inajob/rakuchord/docs/imgs/cheatsheet.jpg

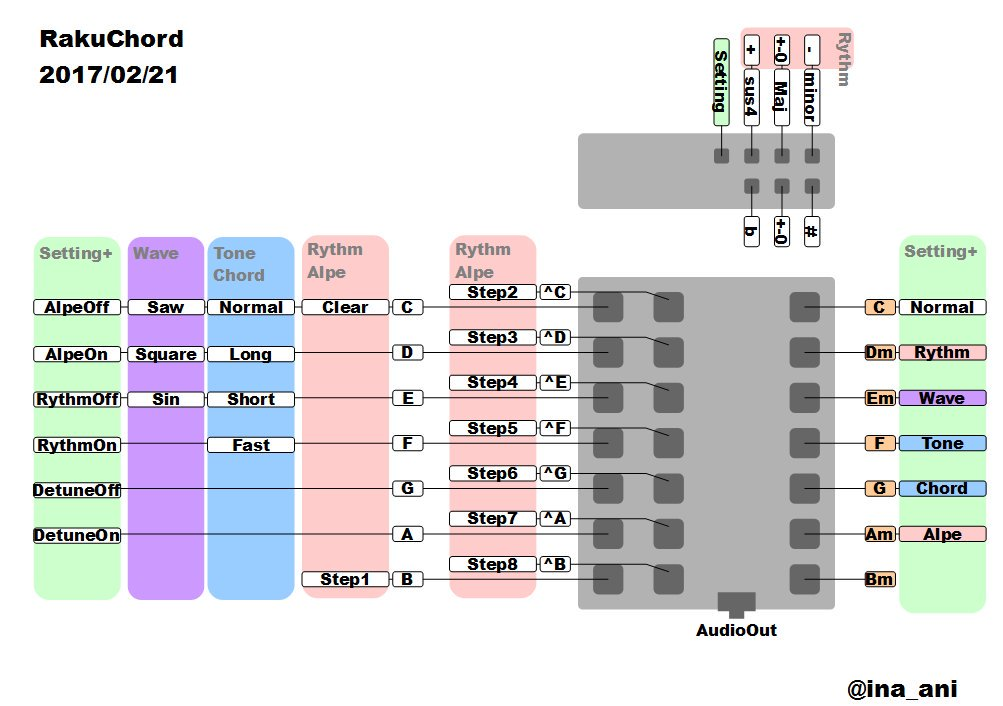
docs/imgs/cheatsheet.jpg
