inajob/rakuchord/docs/imgs/display-v1-3.png

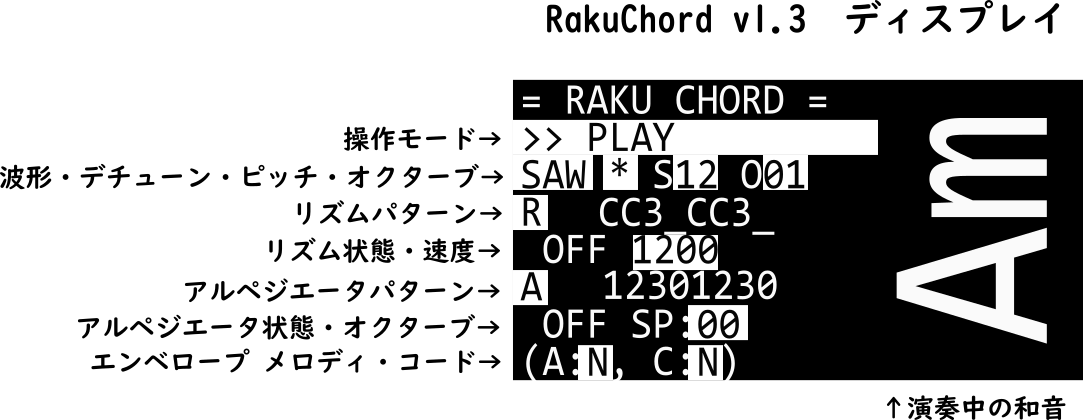
docs/imgs/display-v1-3.png
