inajob/rakuchord/docs/imgs/first-rakuchord.png

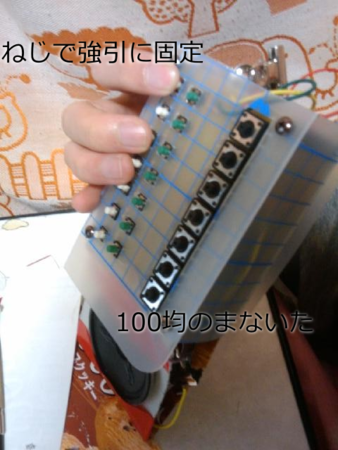
docs/imgs/first-rakuchord.png
