inajob/rakuchord/docs/imgs/latest-rakuchord.jpg

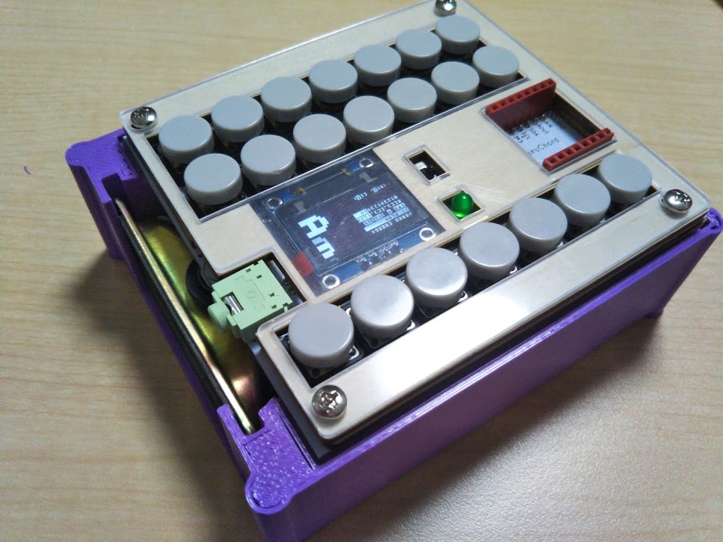
docs/imgs/latest-rakuchord.jpg
