inajob/rakuchord/docs/imgs/many-rakuchord.jpg

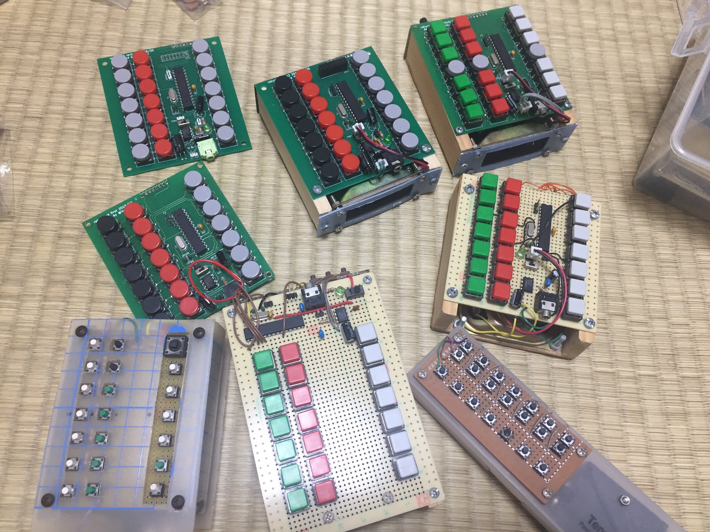
docs/imgs/many-rakuchord.jpg
