inajob/rakuchord/docs/imgs/rakuchord2018.jpg

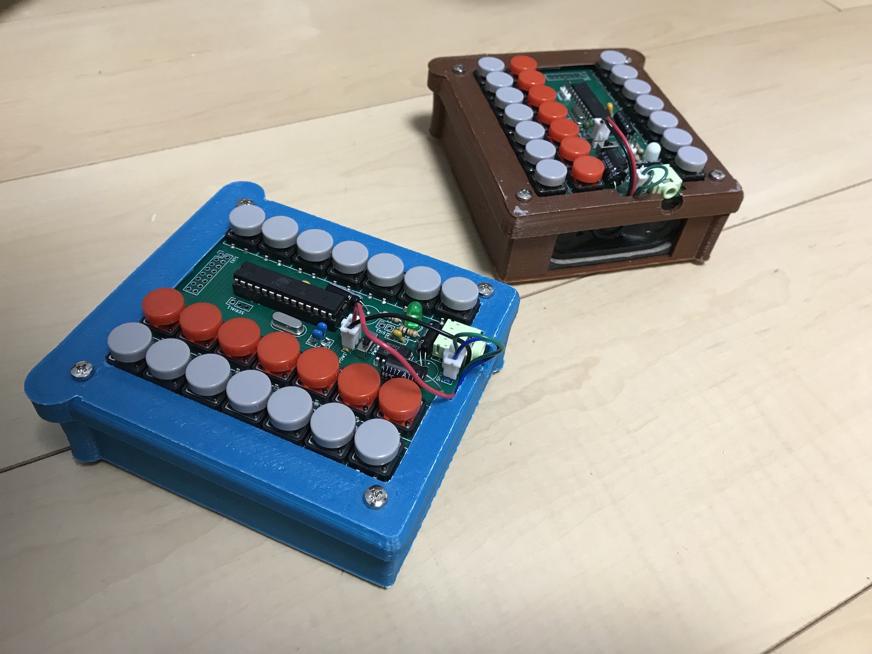
docs/imgs/rakuchord2018.jpg
