inajob/rakuchord/docs/imgs/rakuchord-long.jpg

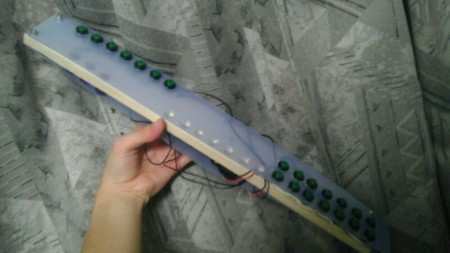
docs/imgs/rakuchord-long.jpg
