inajob/rakuchord/docs/imgs/rakuchord-mobile-3.png

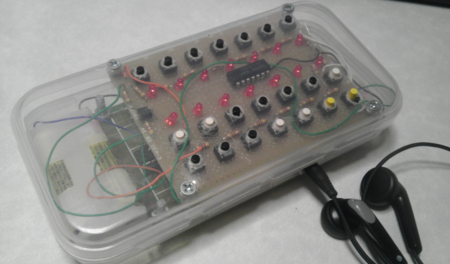
docs/imgs/rakuchord-mobile-3.png
