inajob/rakuchord/docs/imgs/rakuchord-p-v1-4.png

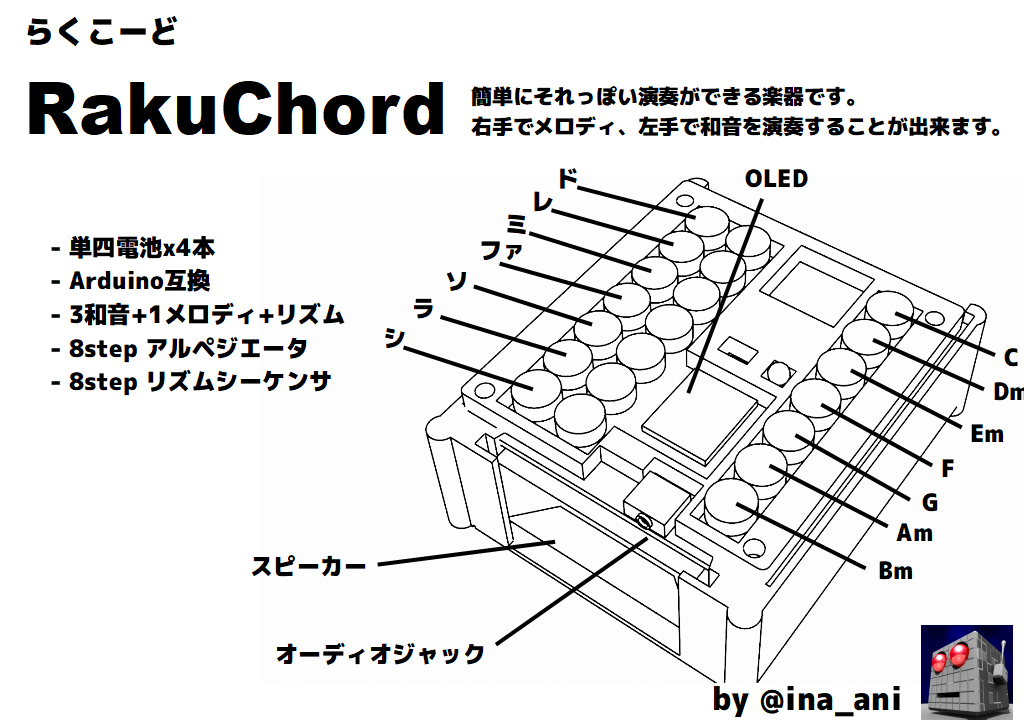
docs/imgs/rakuchord-p-v1-4.png
