inajob/rakuchord/docs/imgs/rakuchord-p.jpg

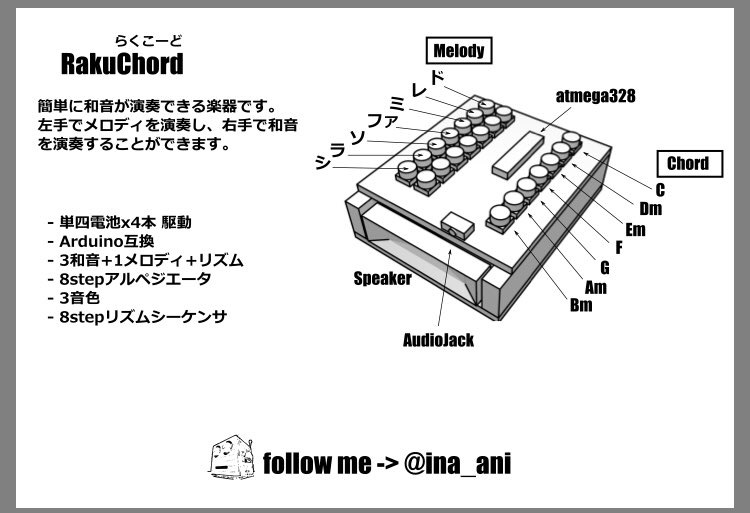
docs/imgs/rakuchord-p.jpg
