inajob/rakuchord/docs/imgs/rakuchord-v1-3-2.jpg

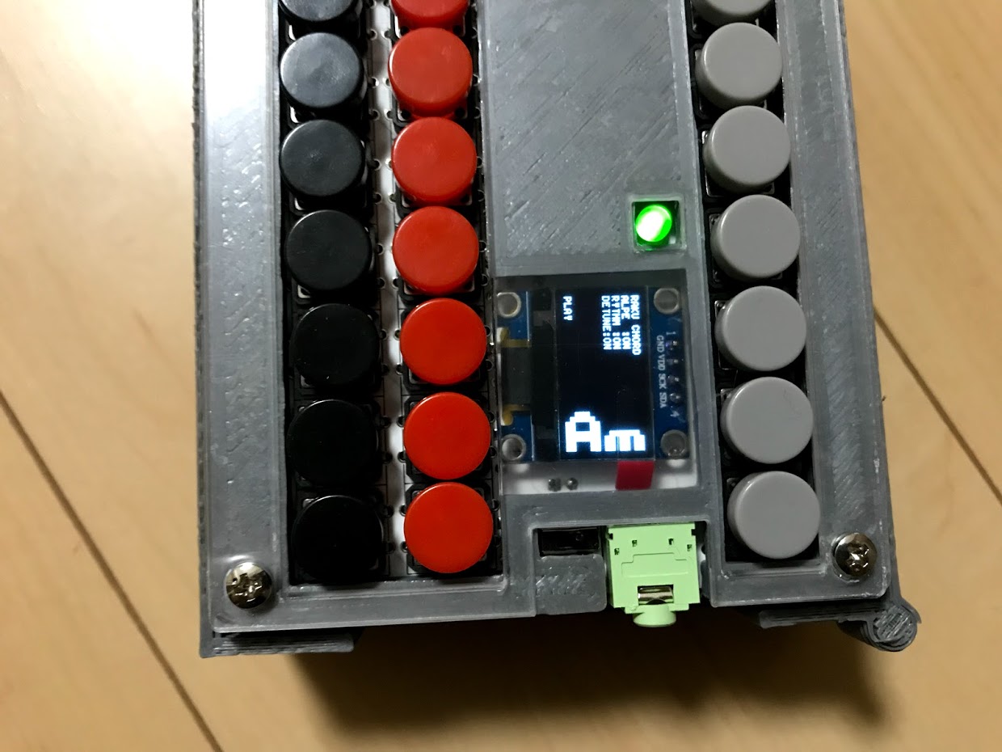
docs/imgs/rakuchord-v1-3-2.jpg
