inajob/rakuchord/docs/imgs/rakuchord-v1-3.jpg

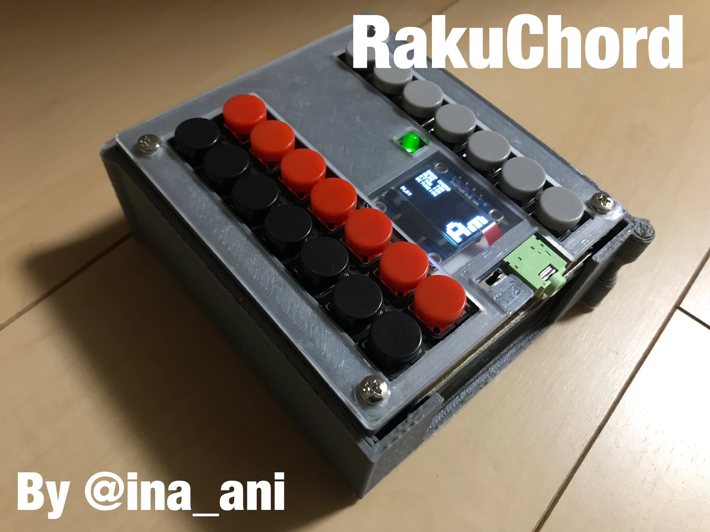
docs/imgs/rakuchord-v1-3.jpg
