inajob/rakuchord/docs/imgs/subkey.jpg

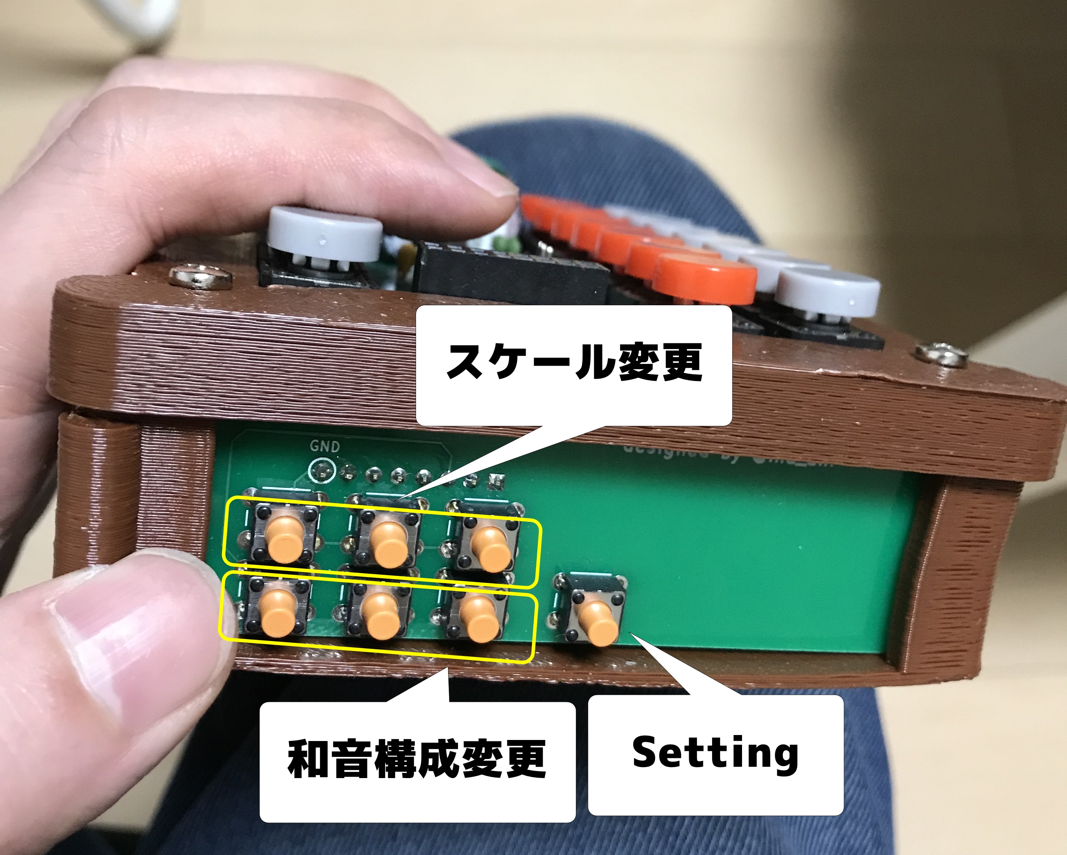
docs/imgs/subkey.jpg
