inajob/rakuchord/docs/imgs/instruction-out-1-4/order.png

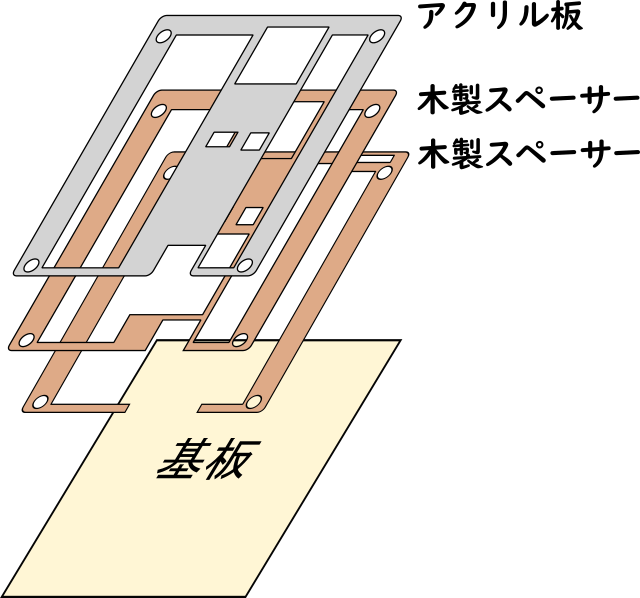
docs/imgs/instruction-out-1-4/order.png
