inajob/rakuchord/docs/imgs/instruction-out/000-first-parts.jpg

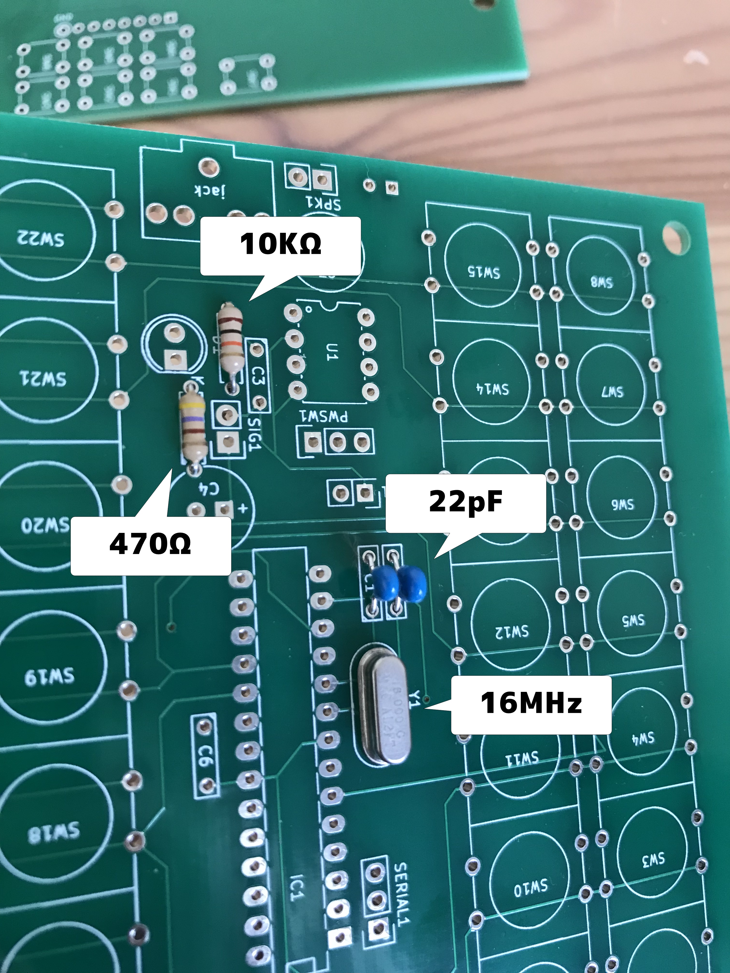
docs/imgs/instruction-out/000-first-parts.jpg
