inajob/rakuchord/docs/imgs/instruction-out/001-first-parts-back.jpg

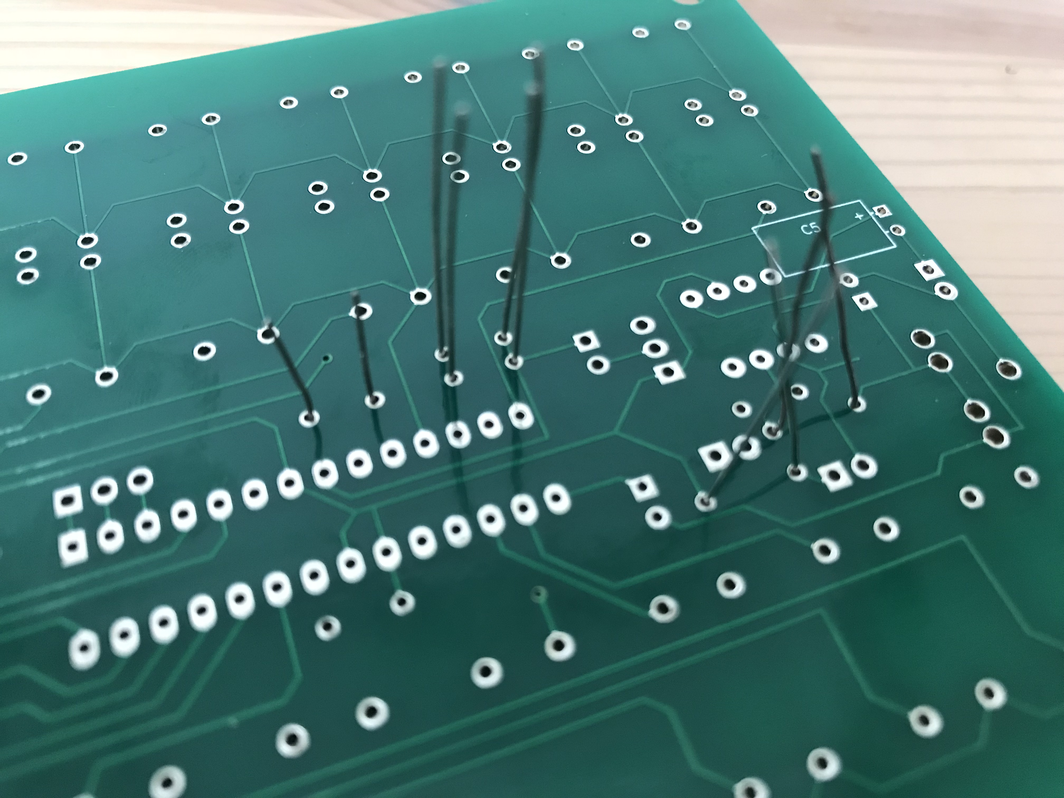
docs/imgs/instruction-out/001-first-parts-back.jpg
