inajob/rakuchord/docs/imgs/instruction-out/002-first-parts-pliers.jpg

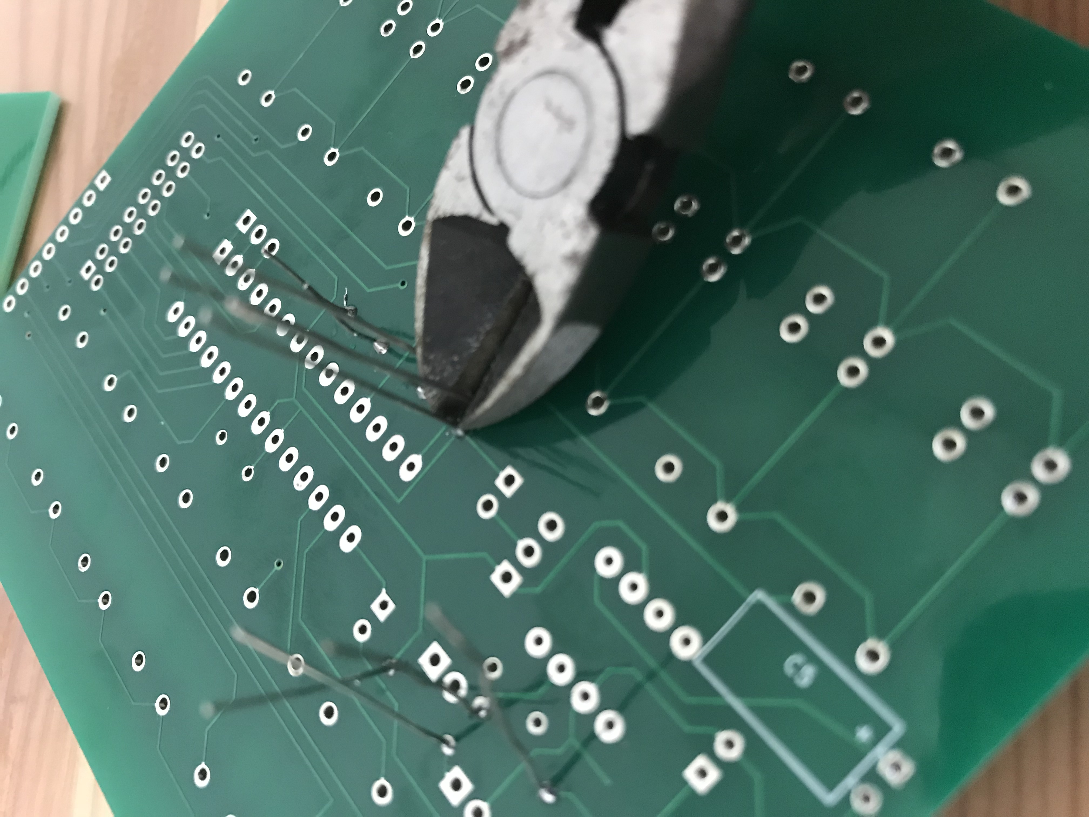
docs/imgs/instruction-out/002-first-parts-pliers.jpg
