inajob/rakuchord/docs/imgs/instruction-out/003-first-parts-complete.jpg

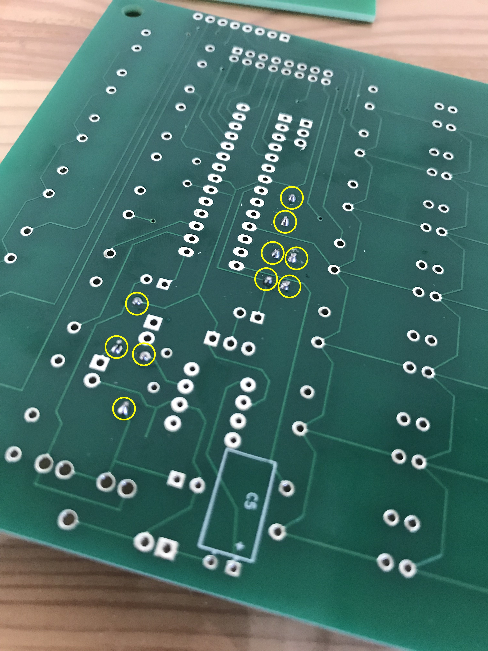
docs/imgs/instruction-out/003-first-parts-complete.jpg
