inajob/rakuchord/docs/imgs/instruction-out/004-second-parts-dub.jpg

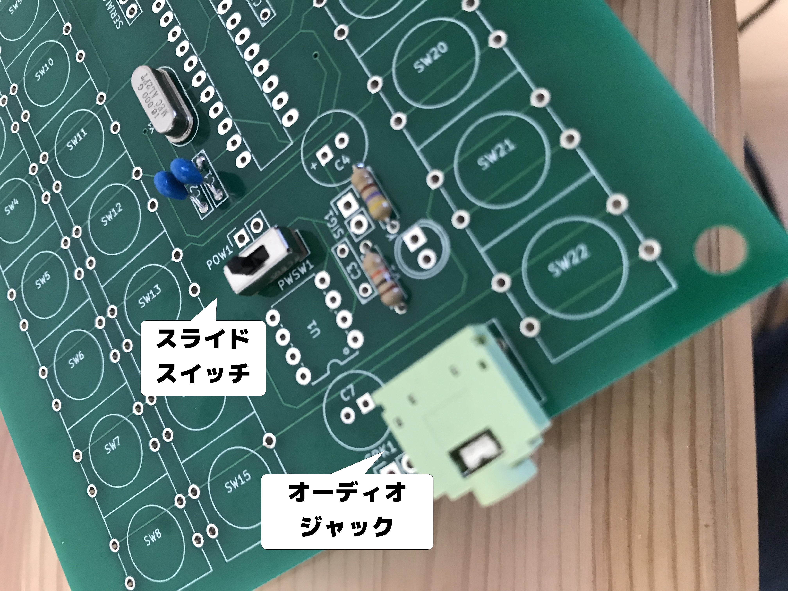
docs/imgs/instruction-out/004-second-parts-dub.jpg
