inajob/rakuchord/docs/imgs/instruction-out/005-second-parts.jpg

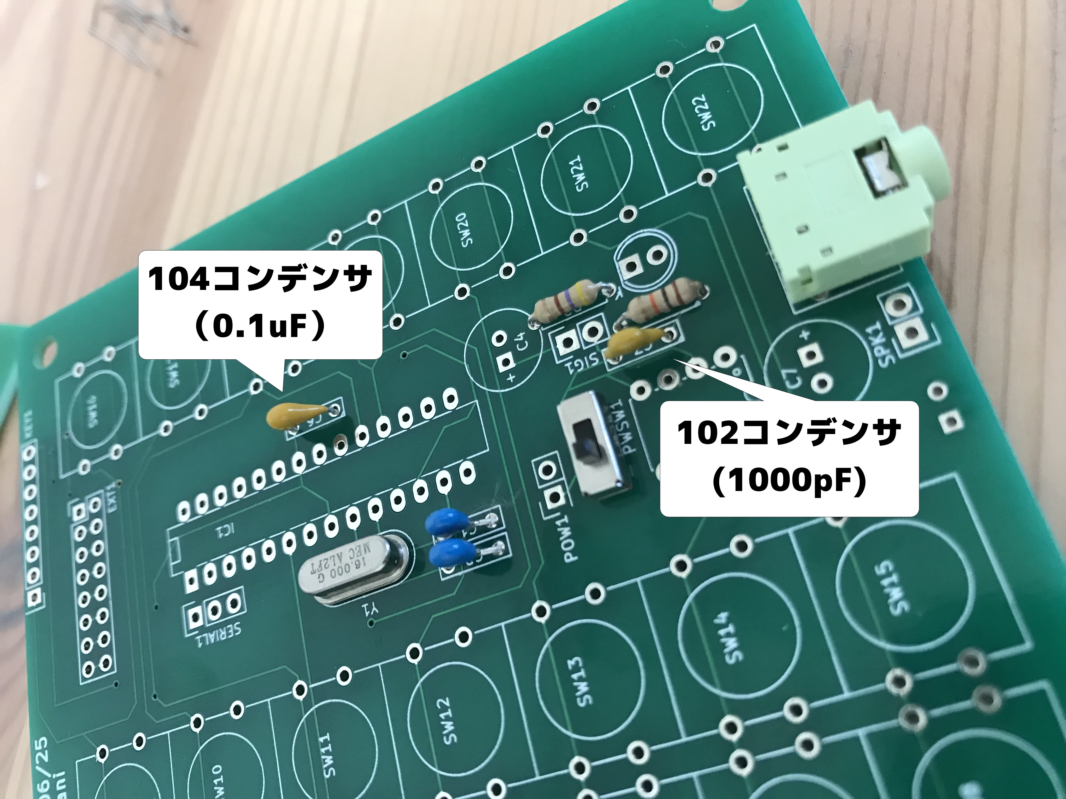
docs/imgs/instruction-out/005-second-parts.jpg
