inajob/rakuchord/docs/imgs/instruction-out/006-second-parts-tips.jpg

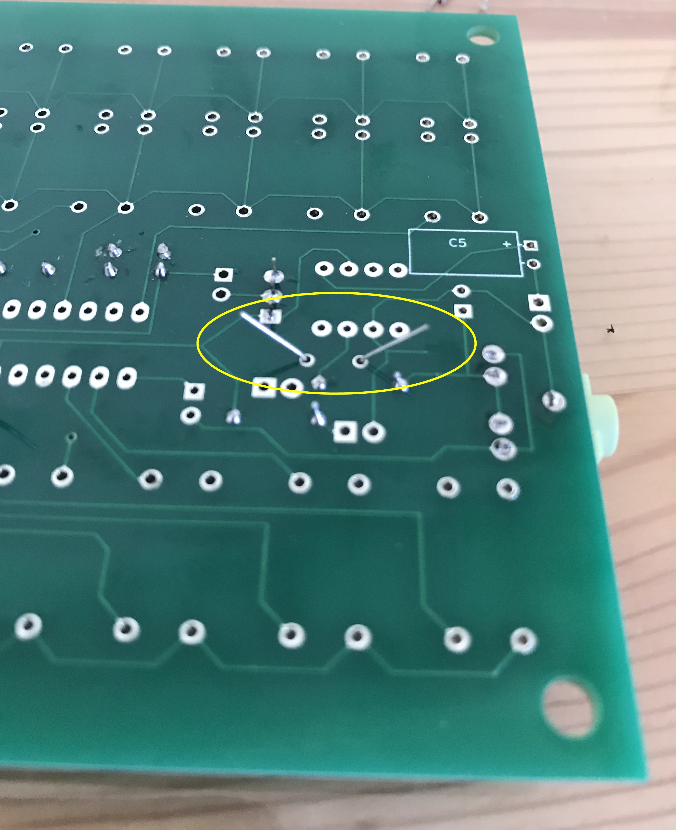
docs/imgs/instruction-out/006-second-parts-tips.jpg
