inajob/rakuchord/docs/imgs/instruction-out/007-third-parts-dub.jpg

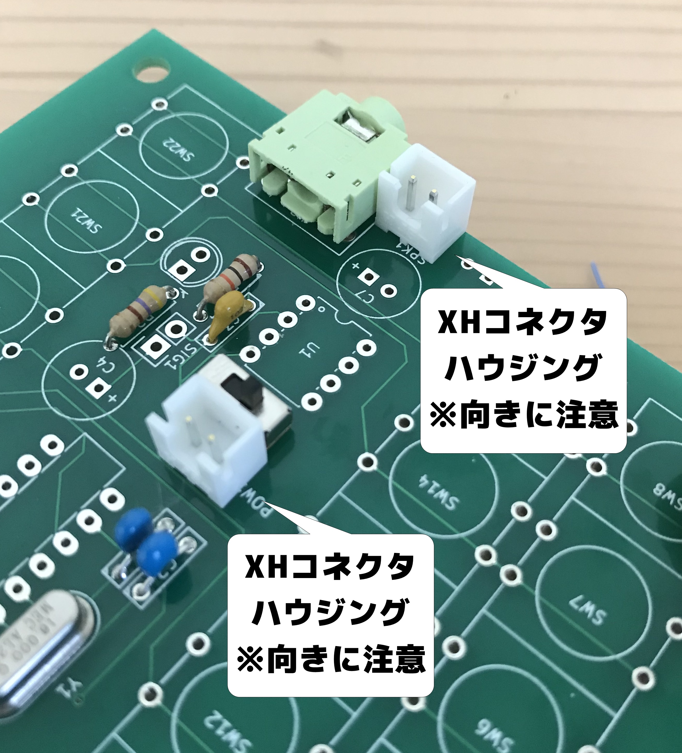
docs/imgs/instruction-out/007-third-parts-dub.jpg
