inajob/rakuchord/docs/imgs/instruction-out/008-third-parts.jpg

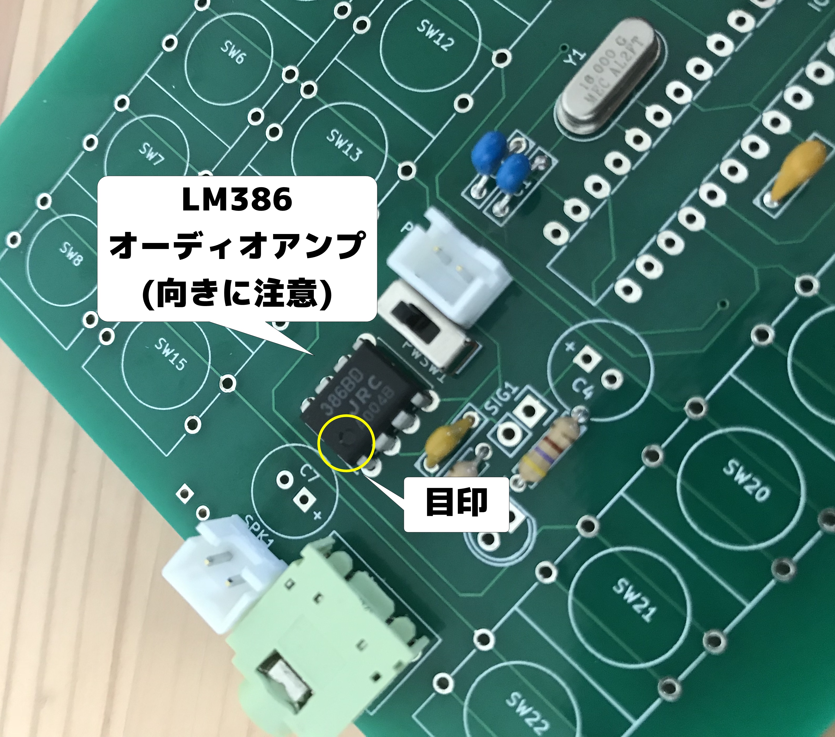
docs/imgs/instruction-out/008-third-parts.jpg
