inajob/rakuchord/docs/imgs/instruction-out/009-forth-parts.jpg

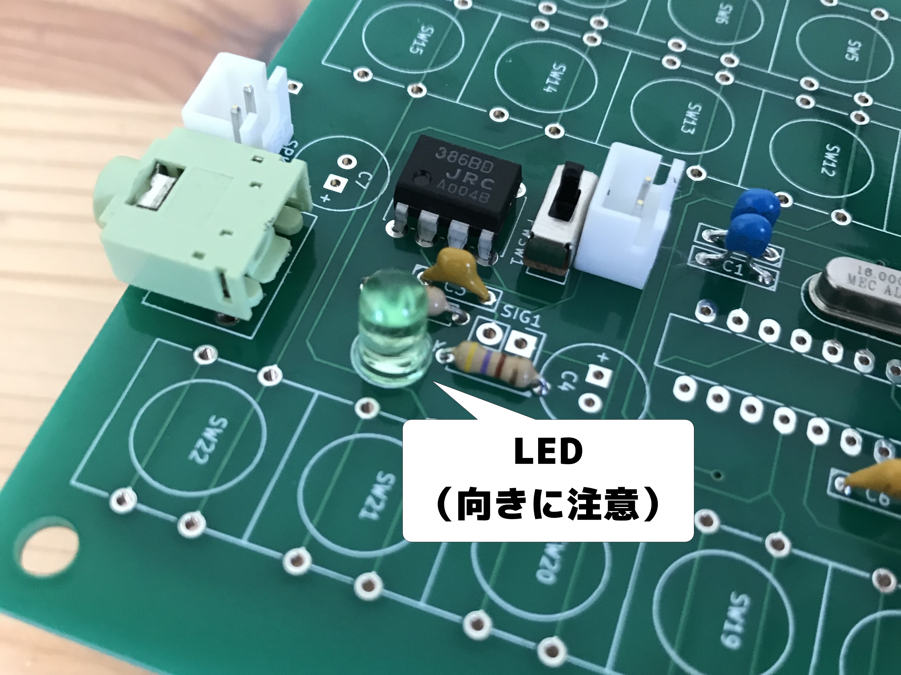
docs/imgs/instruction-out/009-forth-parts.jpg
