inajob/rakuchord/docs/imgs/instruction-out/010-forth-parts-tips.jpg

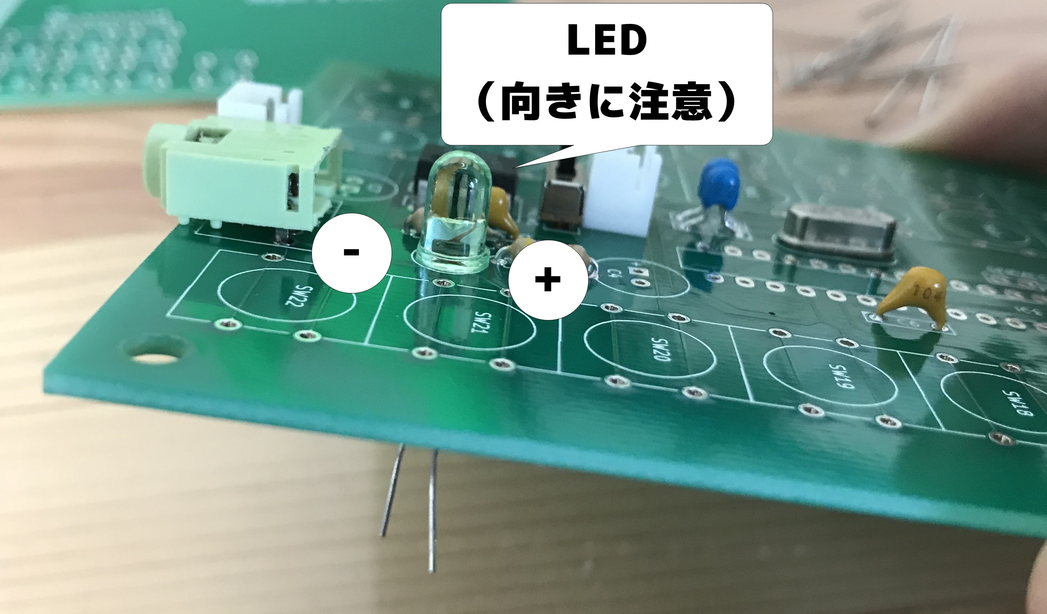
docs/imgs/instruction-out/010-forth-parts-tips.jpg
