inajob/rakuchord/docs/imgs/instruction-out/011-forth-parts-tips-dub.jpg

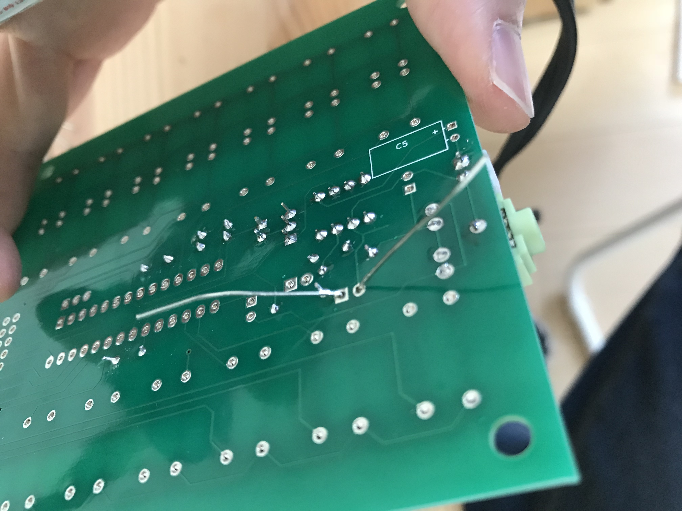
docs/imgs/instruction-out/011-forth-parts-tips-dub.jpg
