inajob/rakuchord/docs/imgs/instruction-out/012-fifth-parts.jpg

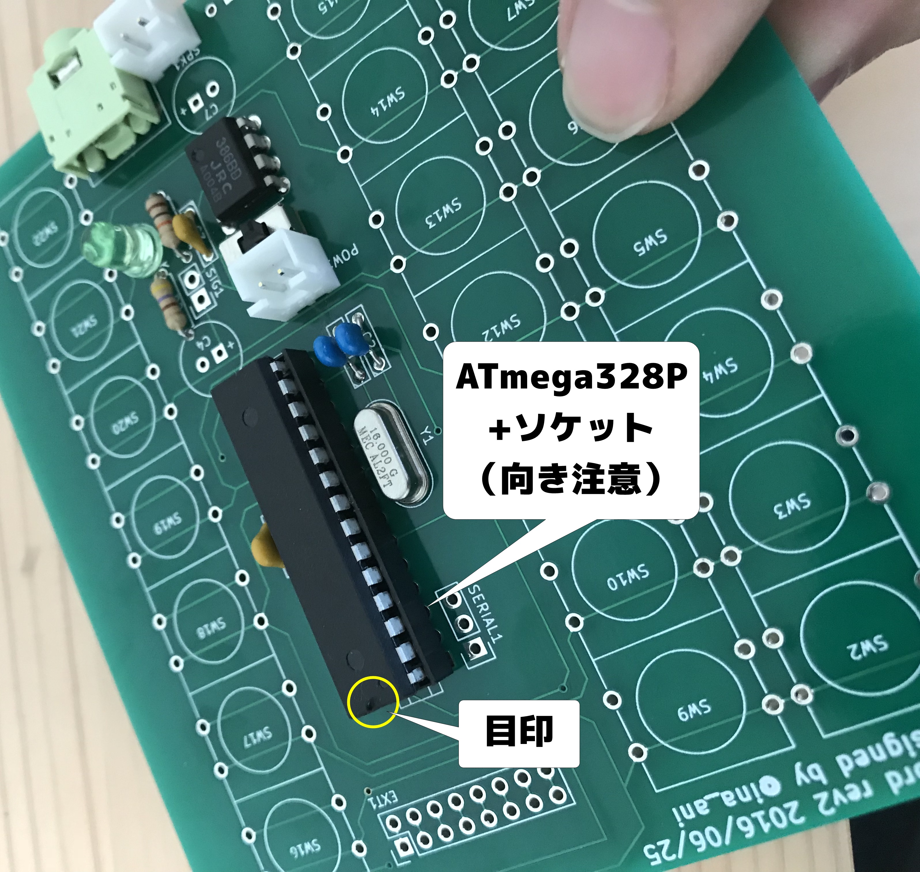
docs/imgs/instruction-out/012-fifth-parts.jpg
