inajob/rakuchord/docs/imgs/instruction-out/013-sixth-parts.jpg

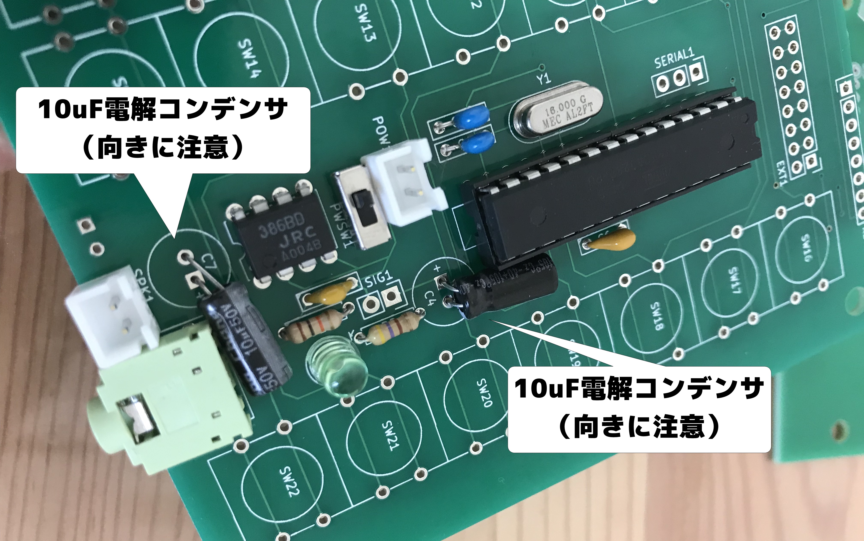
docs/imgs/instruction-out/013-sixth-parts.jpg
