inajob/rakuchord/docs/imgs/instruction-out/014-seventh-parts.jpg

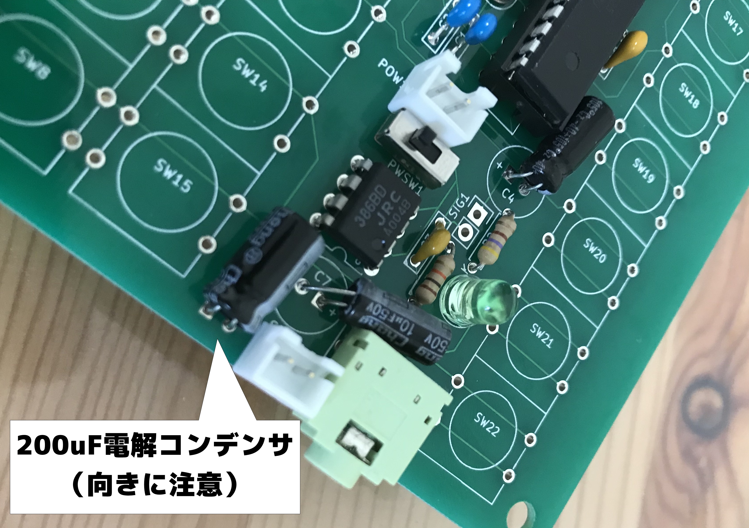
docs/imgs/instruction-out/014-seventh-parts.jpg
