inajob/rakuchord/docs/imgs/parts-1-4/acrylic-cover.jpg

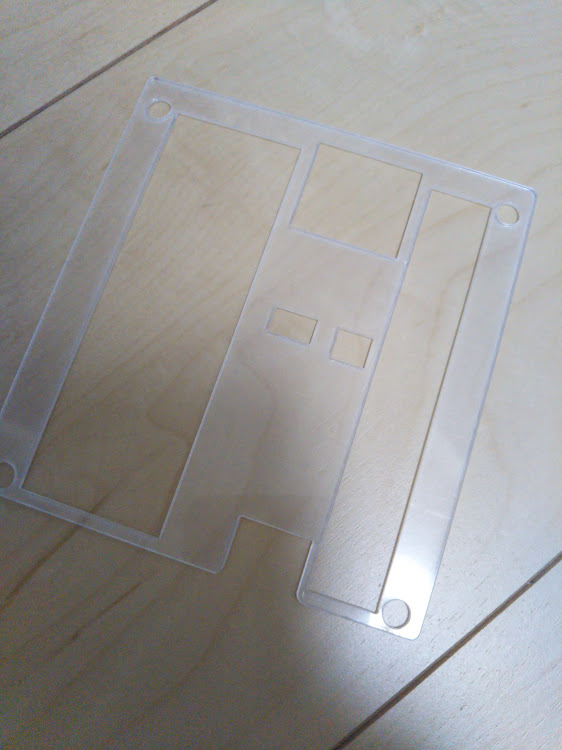
docs/imgs/parts-1-4/acrylic-cover.jpg
