inajob/rakuchord/docs/imgs/parts-1-4/spacer-a.jpg

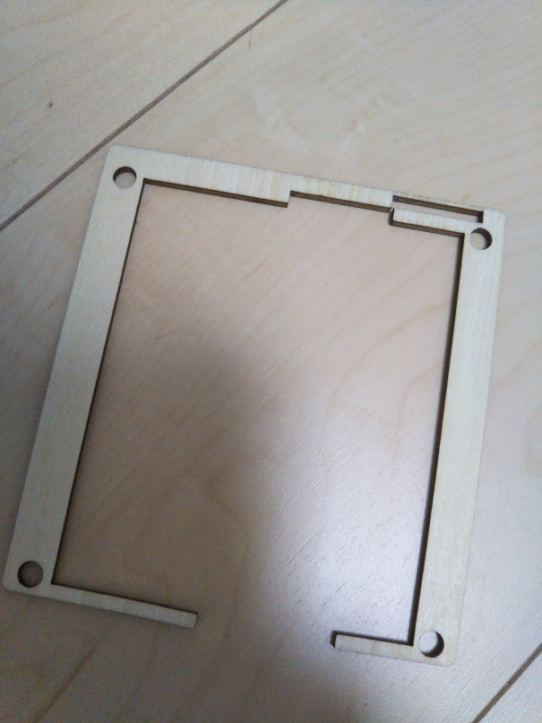
docs/imgs/parts-1-4/spacer-a.jpg
