inajob/rakuchord/docs/imgs/parts-1-4/spacer-b.jpg

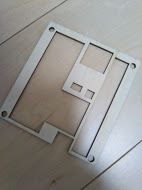
docs/imgs/parts-1-4/spacer-b.jpg
