inajob/rakuchord/docs/imgs/parts-1-4/volume.jpg

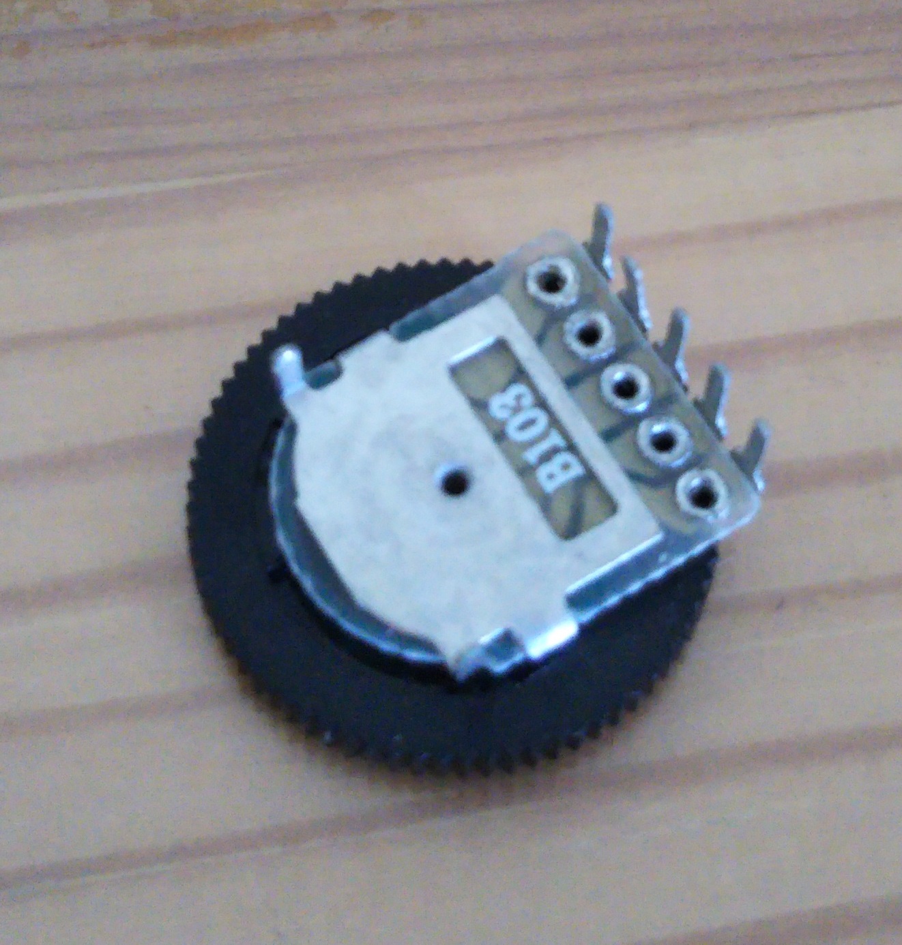
docs/imgs/parts-1-4/volume.jpg
