inajob/rakuchord/docs/imgs/parts-3/c106.jpg

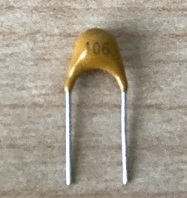
docs/imgs/parts-3/c106.jpg
