inajob/rakuchord/docs/imgs/parts-3/socket8.jpg

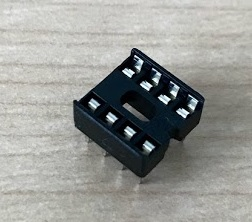
docs/imgs/parts-3/socket8.jpg
