inajob/rakuchord/docs/imgs/parts-next/main.jpg

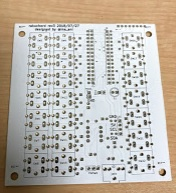
docs/imgs/parts-next/main.jpg
