inajob/rakuchord/docs/imgs/parts-next/oled.jpg

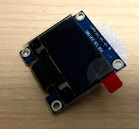
docs/imgs/parts-next/oled.jpg
