inajob/rakuchord/docs/imgs/parts-next/top.jpg

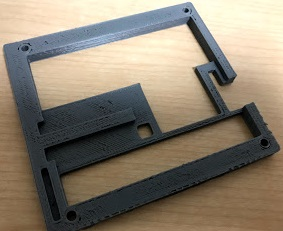
docs/imgs/parts-next/top.jpg
