inajob/rakuchord/docs/imgs/parts/8lpin.jpg

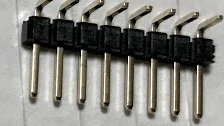
docs/imgs/parts/8lpin.jpg
