inajob/rakuchord/docs/imgs/parts/8pinsocket.jpg

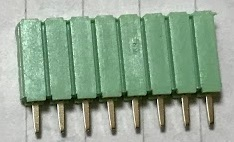
docs/imgs/parts/8pinsocket.jpg
