inajob/rakuchord/docs/imgs/parts/battery.jpg

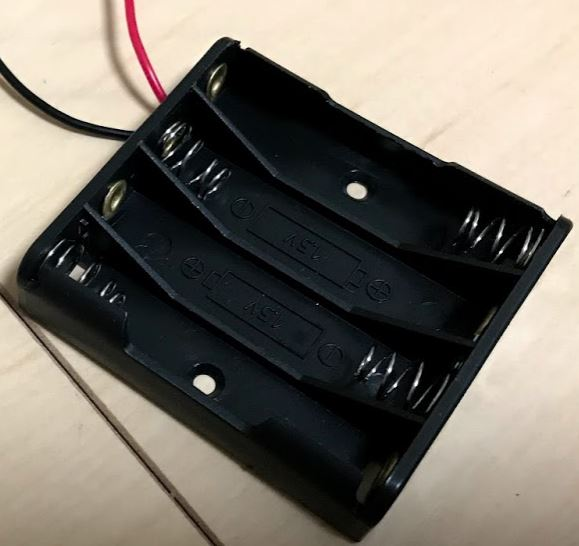
docs/imgs/parts/battery.jpg
