inajob/rakuchord/docs/imgs/parts/boltmodel.jpg

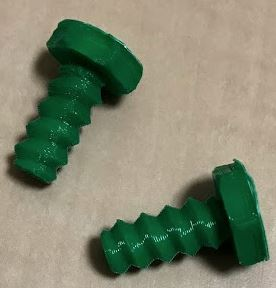
docs/imgs/parts/boltmodel.jpg
