inajob/rakuchord/docs/imgs/parts/bottom.jpg

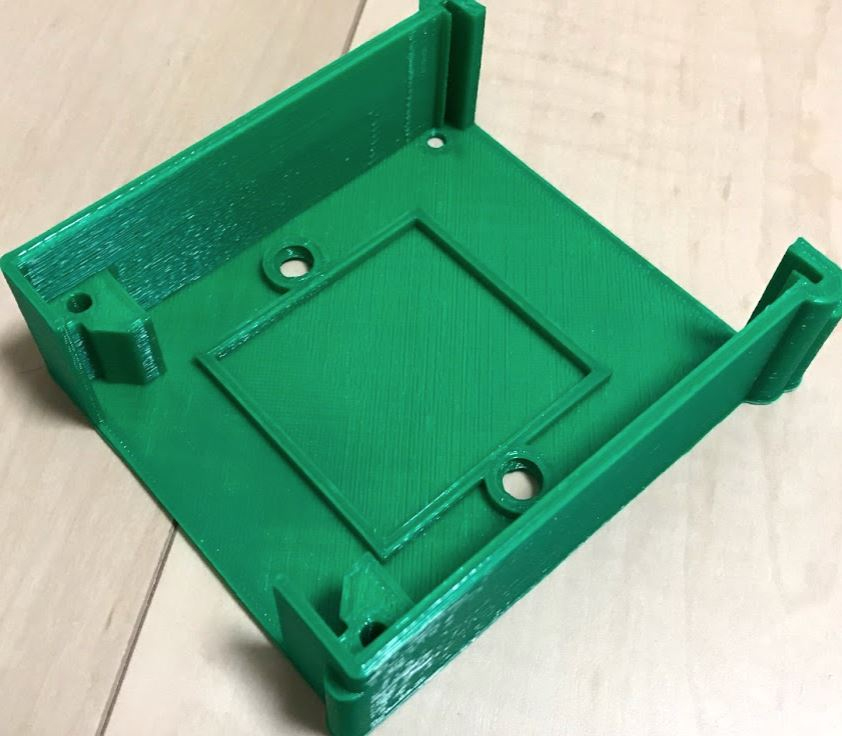
docs/imgs/parts/bottom.jpg
