inajob/rakuchord/docs/imgs/parts/c102.jpg

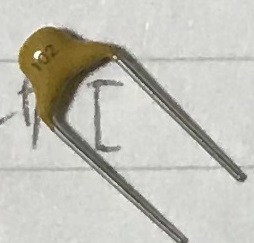
docs/imgs/parts/c102.jpg
