inajob/rakuchord/docs/imgs/parts/c104.jpg

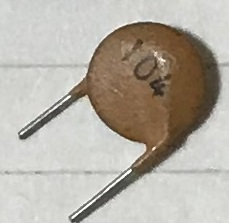
docs/imgs/parts/c104.jpg
