inajob/rakuchord/docs/imgs/parts/c220.jpg

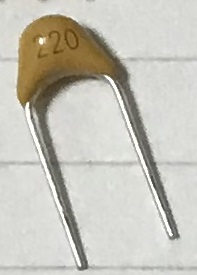
docs/imgs/parts/c220.jpg
