inajob/rakuchord/docs/imgs/parts/crystal.jpg

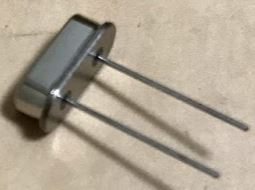
docs/imgs/parts/crystal.jpg
