inajob/rakuchord/docs/imgs/parts/ec10.jpg

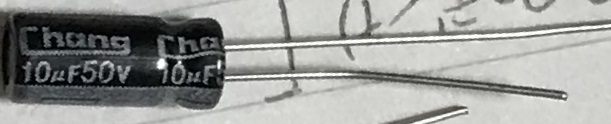
docs/imgs/parts/ec10.jpg
