inajob/rakuchord/docs/imgs/parts/ec220.jpg

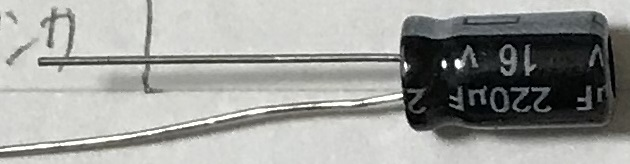
docs/imgs/parts/ec220.jpg
