inajob/rakuchord/docs/imgs/parts/holder.jpg

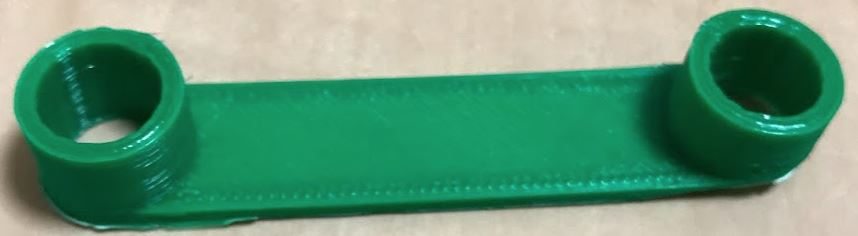
docs/imgs/parts/holder.jpg
