inajob/rakuchord/docs/imgs/parts/jack.jpg

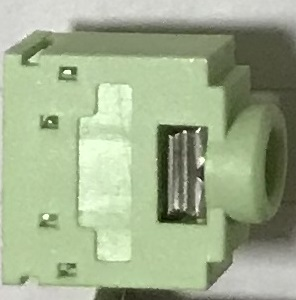
docs/imgs/parts/jack.jpg
