inajob/rakuchord/docs/imgs/parts/lm386.jpg

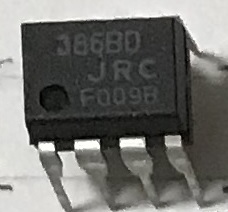
docs/imgs/parts/lm386.jpg
