inajob/rakuchord/docs/imgs/parts/main.jpg

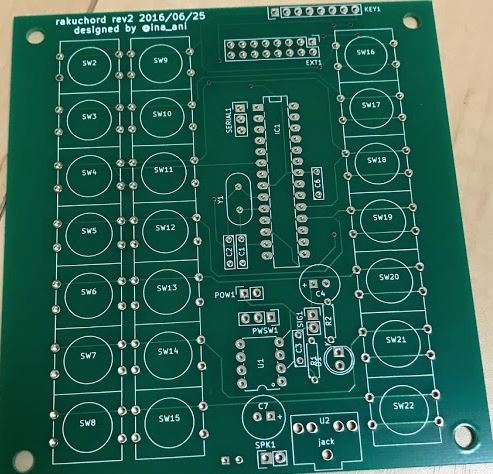
docs/imgs/parts/main.jpg
