inajob/rakuchord/docs/imgs/parts/slideswitch.jpg

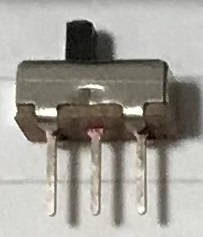
docs/imgs/parts/slideswitch.jpg
