inajob/rakuchord/docs/imgs/parts/speaker.jpg

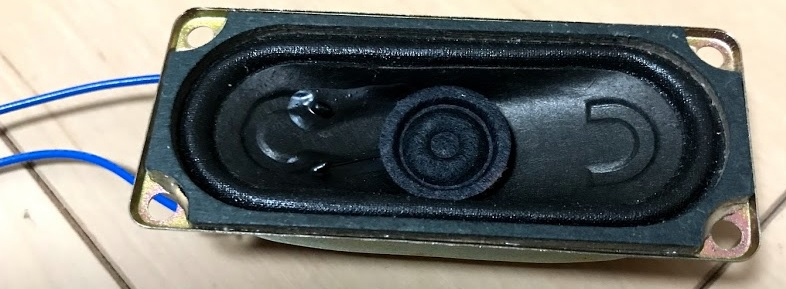
docs/imgs/parts/speaker.jpg
