inajob/rakuchord/docs/imgs/parts/sub.jpg

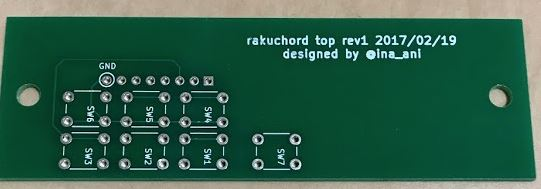
docs/imgs/parts/sub.jpg
