inajob/rakuchord/docs/imgs/parts/sw6.jpg

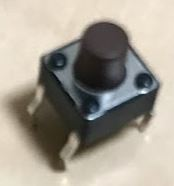
docs/imgs/parts/sw6.jpg
