inajob/rakuchord/docs/imgs/parts/sw12.jpg

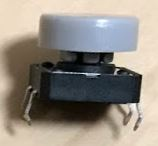
docs/imgs/parts/sw12.jpg
