inajob/rakuchord/docs/imgs/parts/top.jpg

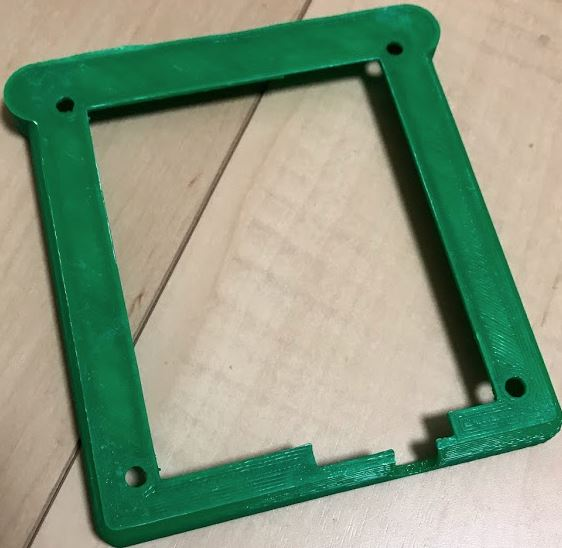
docs/imgs/parts/top.jpg
