inajob/rakuchord/docs/imgs/parts/xhconnector.jpg

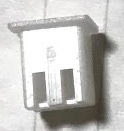
docs/imgs/parts/xhconnector.jpg
