inajob/rakuchord/docs/imgs/howto-hold.jpg

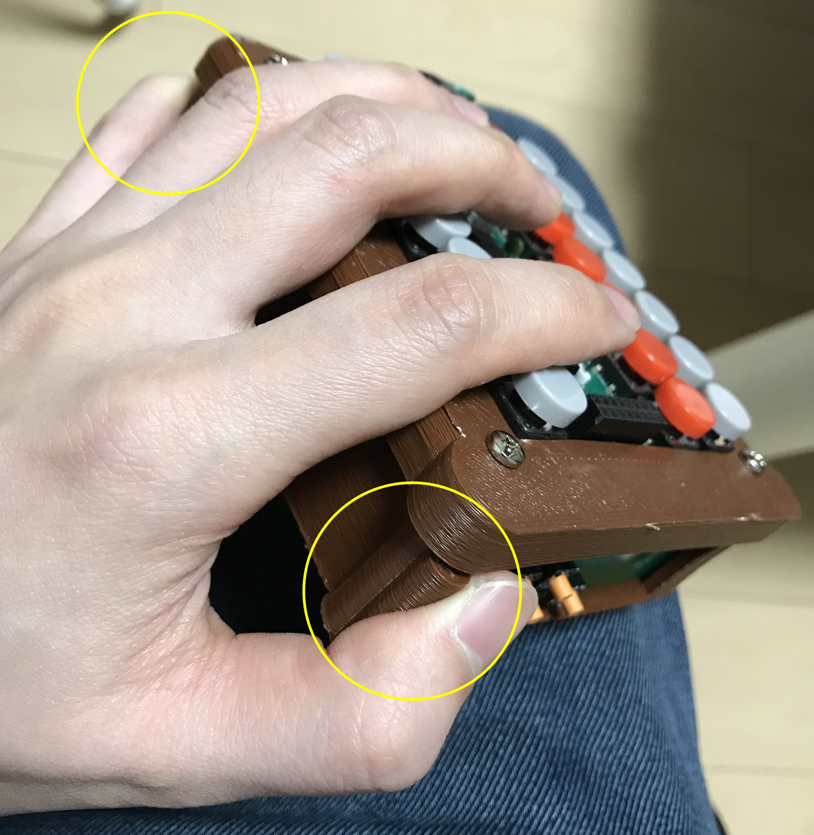
docs/imgs/howto-hold.jpg
