inajob/rakuchord/docs/imgs/instruction-out-1-4/0000-board.jpg

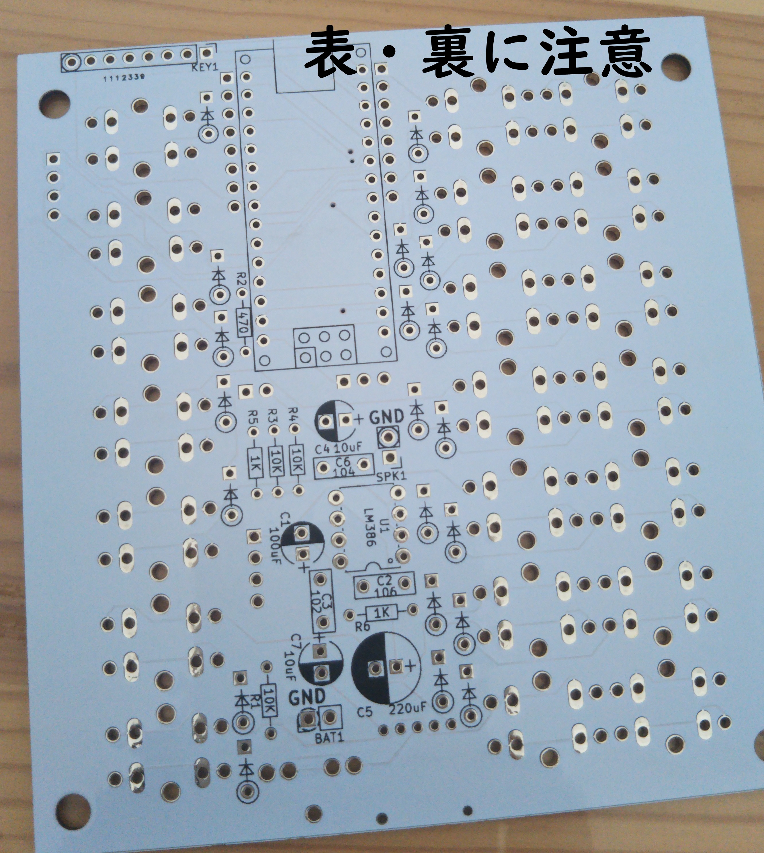
docs/imgs/instruction-out-1-4/0000-board.jpg
