inajob/rakuchord/docs/imgs/instruction-out-1-4/0100-diode.jpg

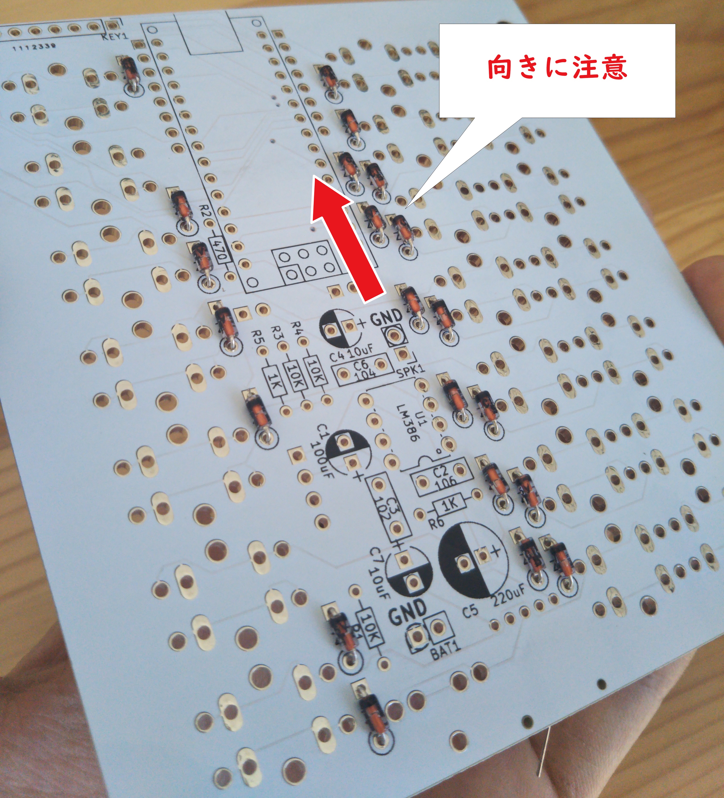
docs/imgs/instruction-out-1-4/0100-diode.jpg
