inajob/rakuchord/docs/imgs/instruction-out-1-4/0110-diode-foot.jpg

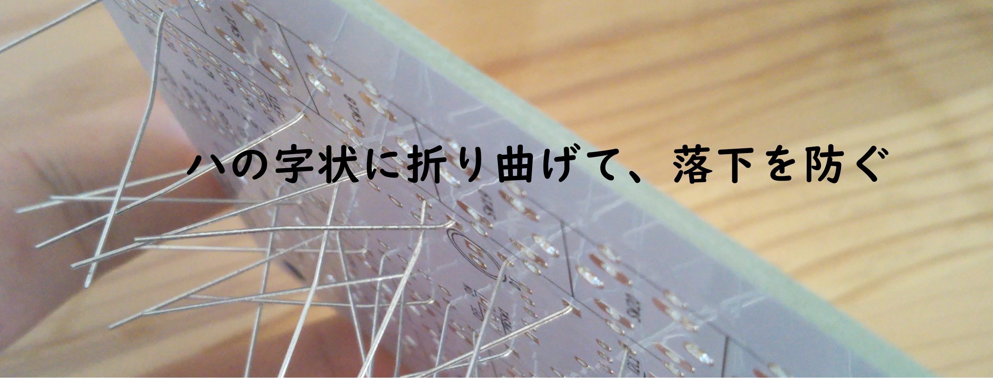
docs/imgs/instruction-out-1-4/0110-diode-foot.jpg
