inajob/rakuchord/docs/imgs/instruction-out-1-4/0120-diode-mount.jpg

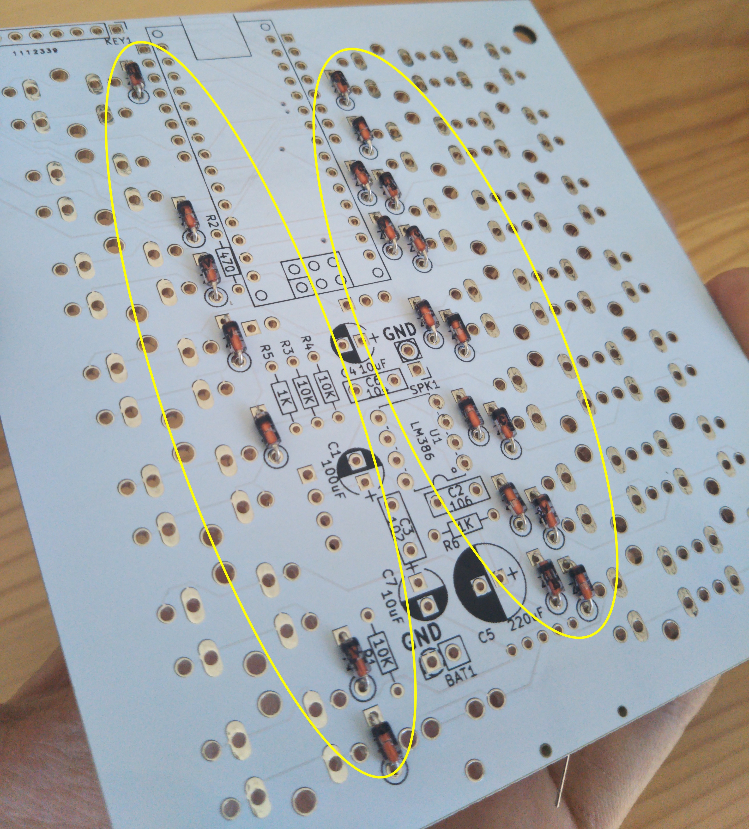
docs/imgs/instruction-out-1-4/0120-diode-mount.jpg
