inajob/rakuchord/docs/imgs/instruction-out-1-4/0130-diode-back.jpg

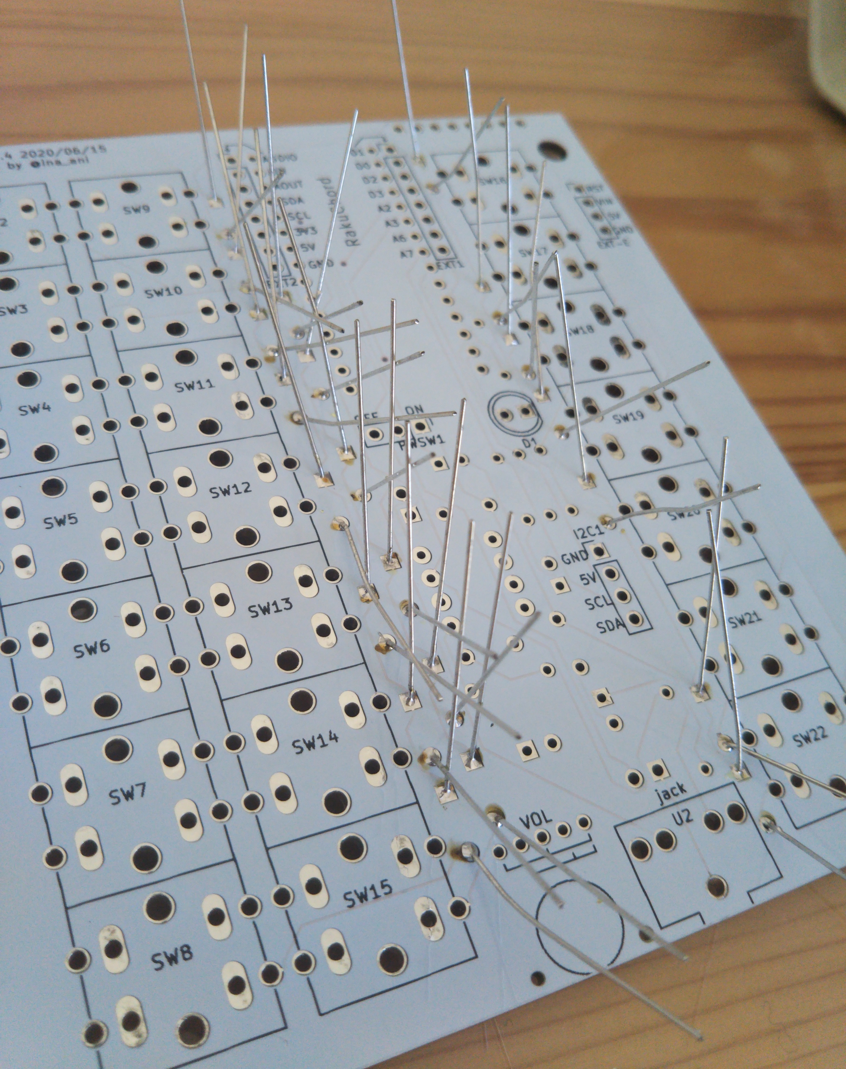
docs/imgs/instruction-out-1-4/0130-diode-back.jpg
