inajob/rakuchord/docs/imgs/instruction-out-1-4/0140-diode-pilers.jpg

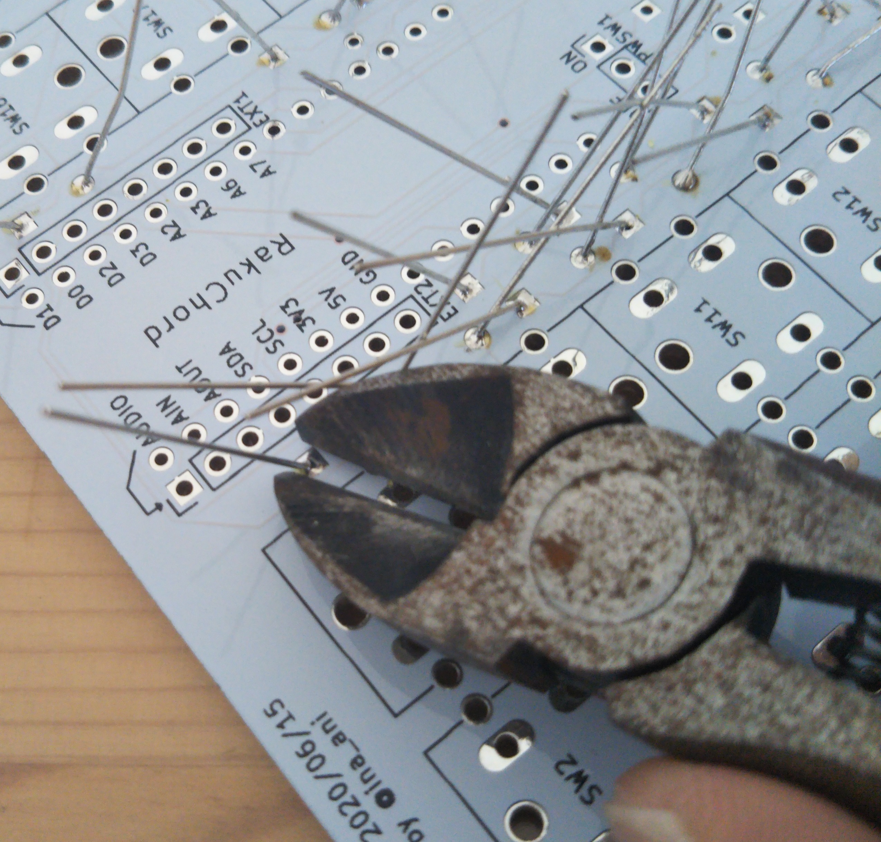
docs/imgs/instruction-out-1-4/0140-diode-pilers.jpg
