inajob/rakuchord/docs/imgs/instruction-out-1-4/0150-diode-back-comp.jpg

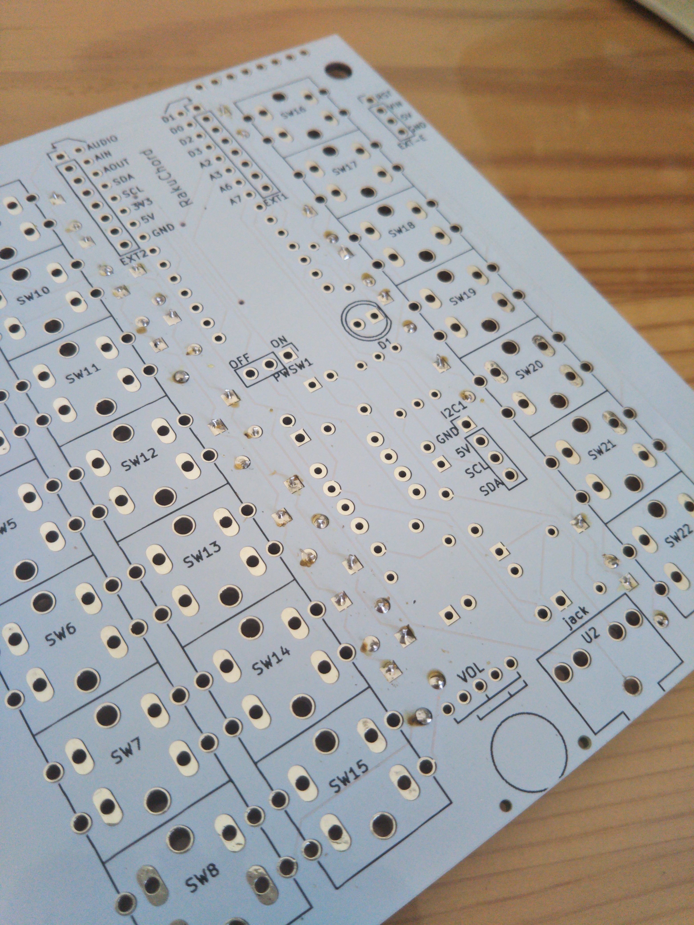
docs/imgs/instruction-out-1-4/0150-diode-back-comp.jpg
