inajob/rakuchord/docs/imgs/instruction-out-1-4/0210-register.jpg

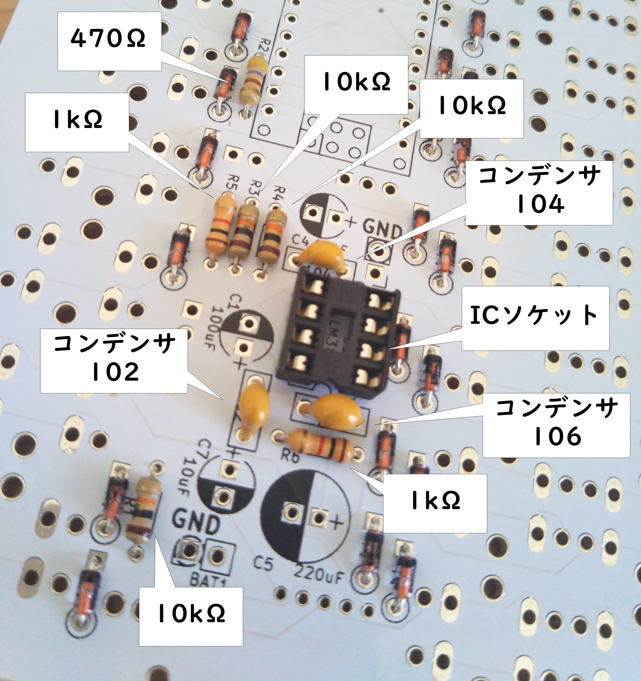
docs/imgs/instruction-out-1-4/0210-register.jpg
