inajob/rakuchord/docs/imgs/instruction-out-1-4/0211-lm386.jpg

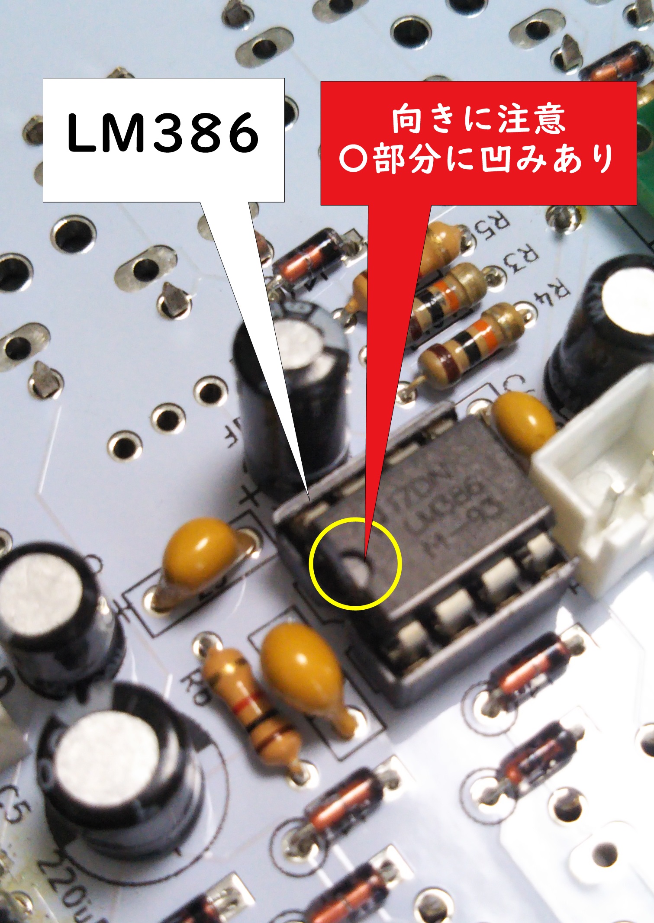
docs/imgs/instruction-out-1-4/0211-lm386.jpg
