inajob/rakuchord/docs/imgs/instruction-out-1-4/0410-connector.jpg

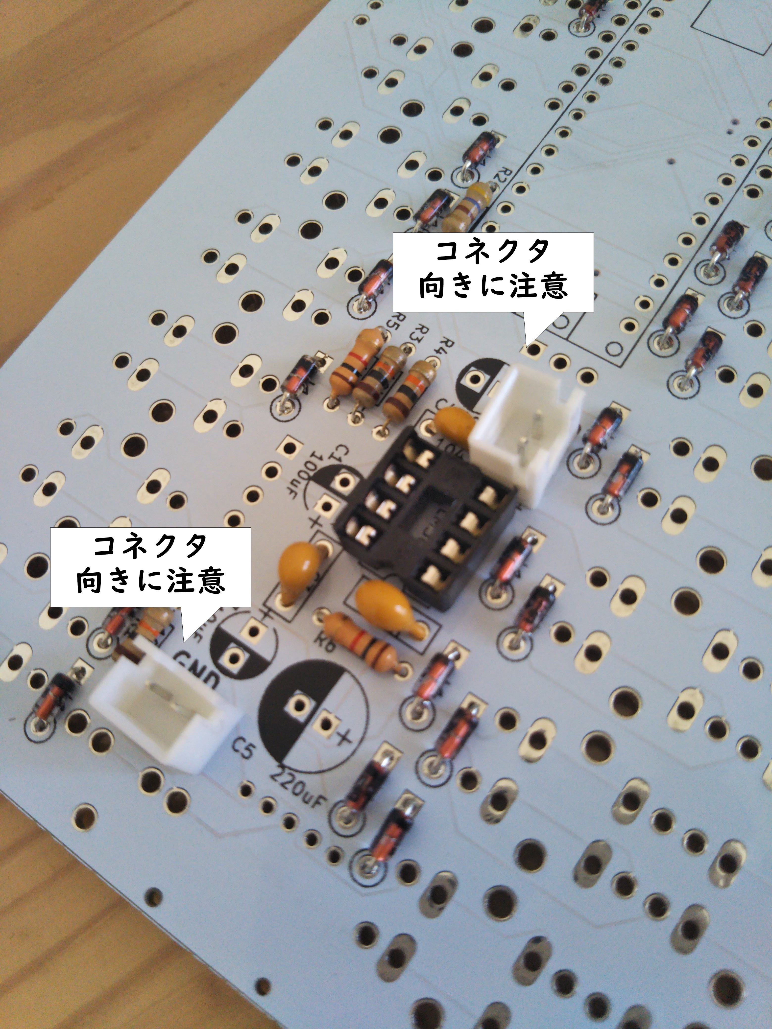
docs/imgs/instruction-out-1-4/0410-connector.jpg
