inajob/rakuchord/docs/imgs/instruction-out-1-4/0510-ecap.jpg

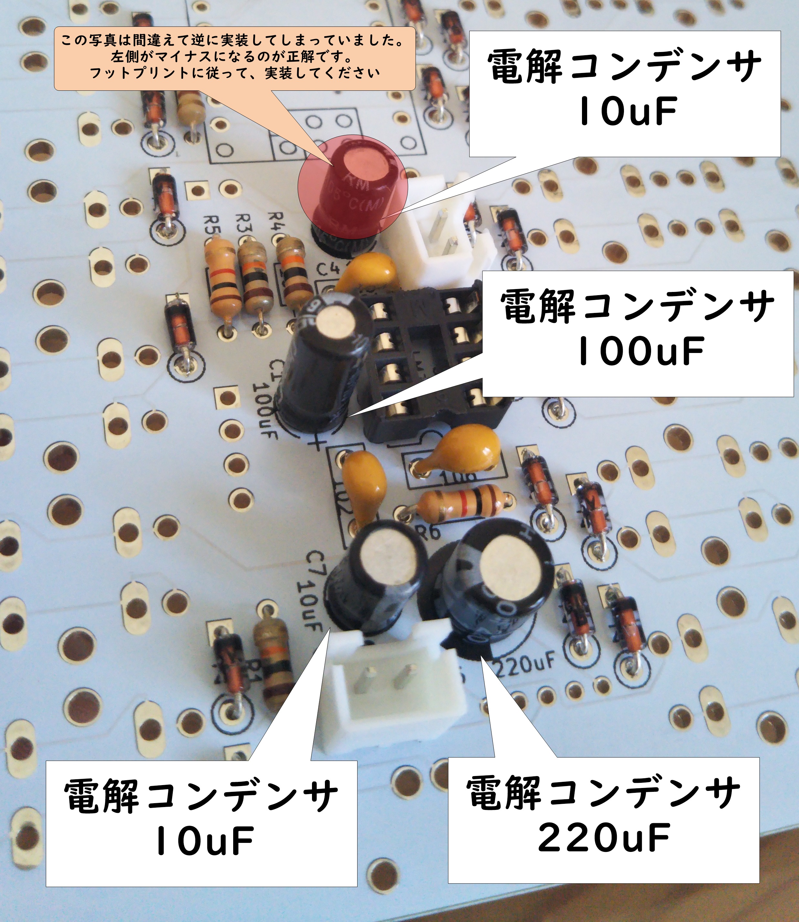
docs/imgs/instruction-out-1-4/0510-ecap.jpg
