inajob/rakuchord/docs/imgs/instruction-out-1-4/0610-arduino.jpg

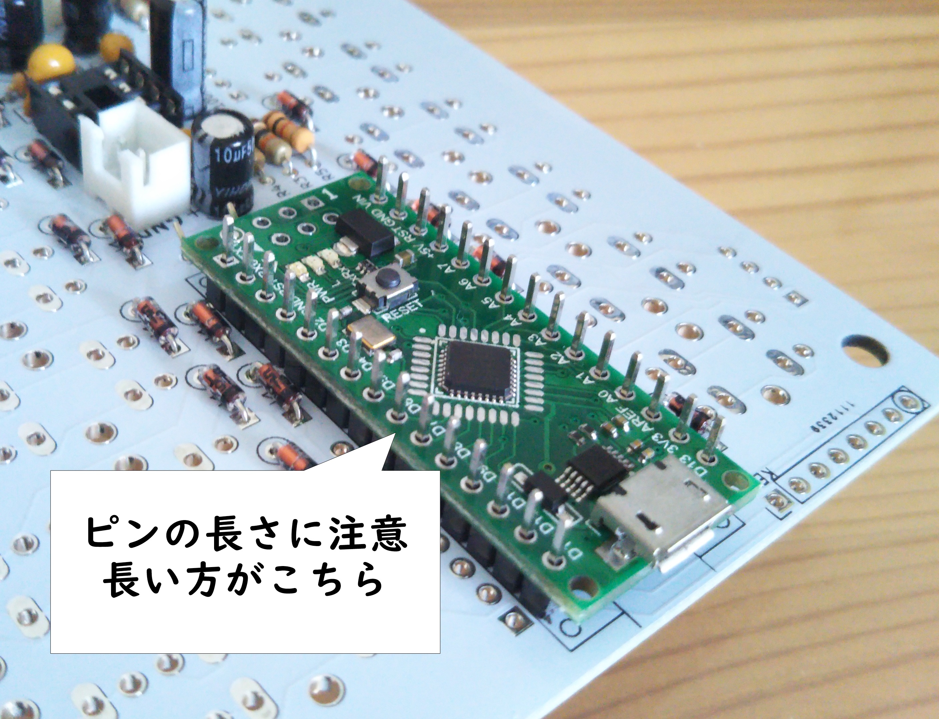
docs/imgs/instruction-out-1-4/0610-arduino.jpg
