inajob/rakuchord/docs/imgs/instruction-out-1-4/0620-arduino-back.jpg

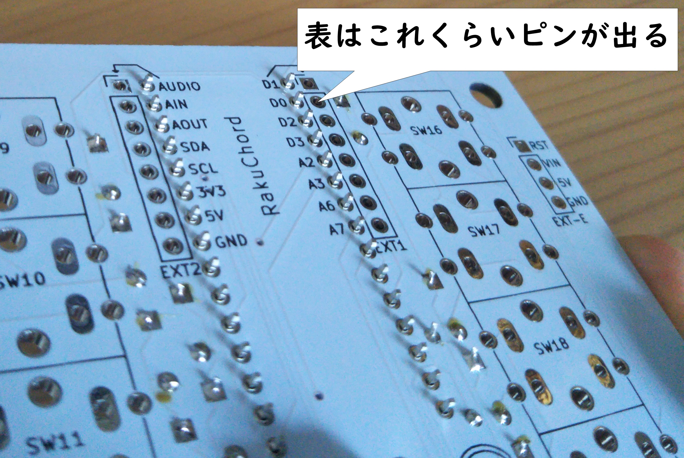
docs/imgs/instruction-out-1-4/0620-arduino-back.jpg
