inajob/rakuchord/docs/imgs/instruction-out-1-4/0710-switch.jpg

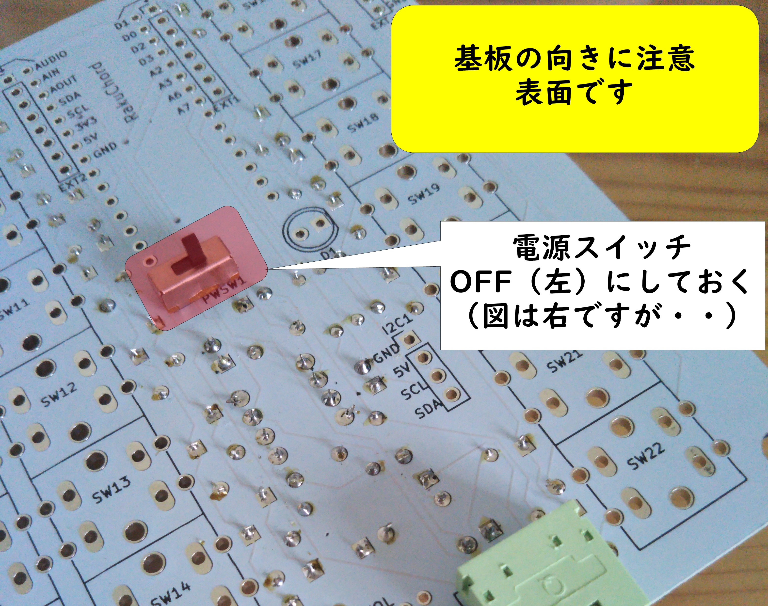
docs/imgs/instruction-out-1-4/0710-switch.jpg
