inajob/rakuchord/docs/imgs/instruction-out-1-4/0810-jack.jpg

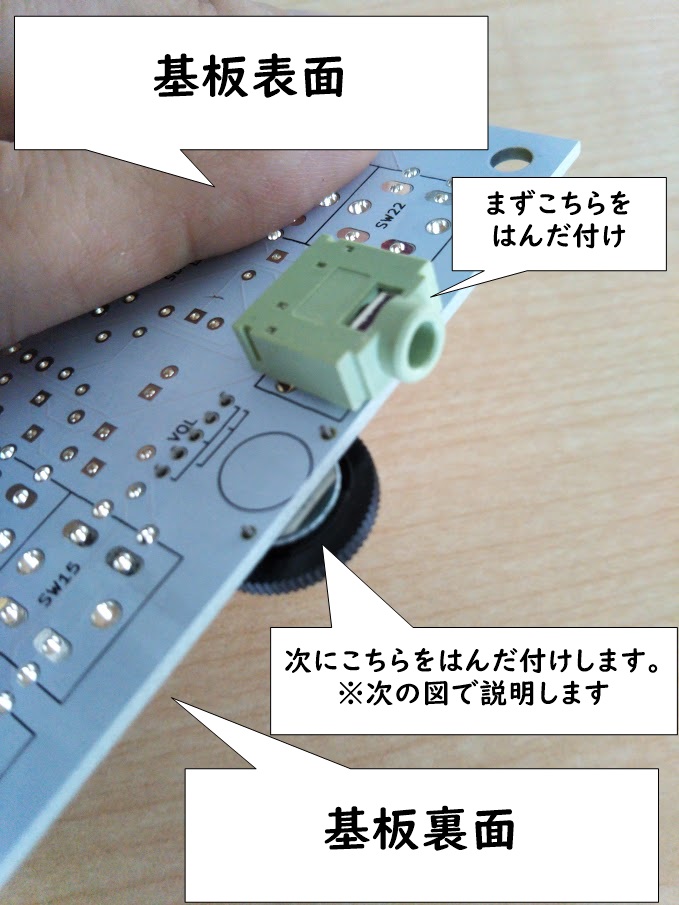
docs/imgs/instruction-out-1-4/0810-jack.jpg
