inajob/rakuchord/docs/imgs/instruction-out-1-4/0820-volume-hack.jpg

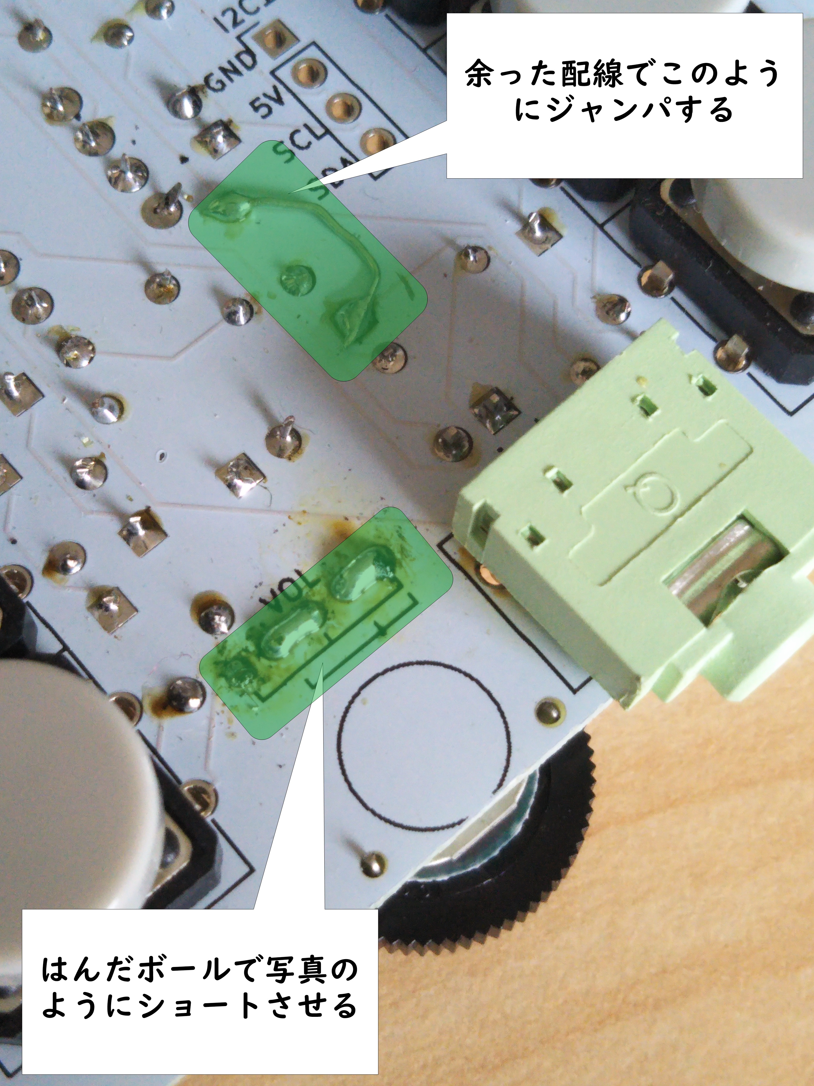
docs/imgs/instruction-out-1-4/0820-volume-hack.jpg
