inajob/rakuchord/docs/imgs/instruction-out-1-4/0910-check.jpg

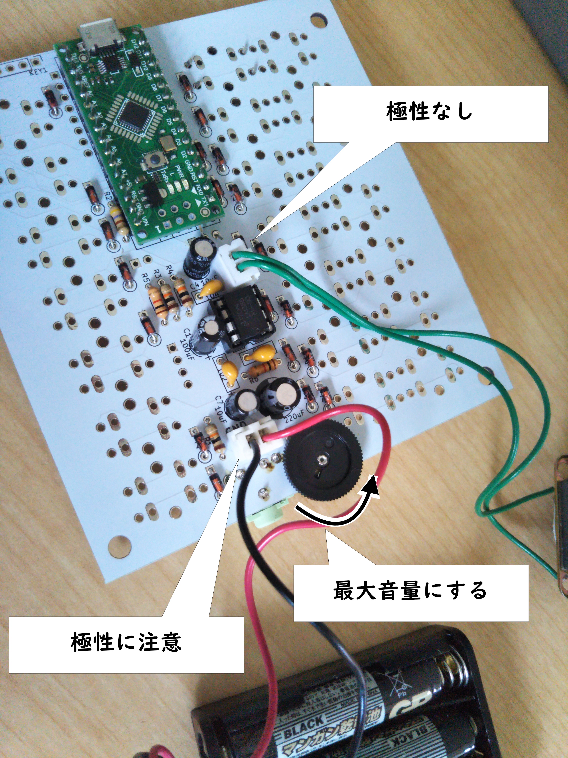
docs/imgs/instruction-out-1-4/0910-check.jpg
