inajob/rakuchord/docs/imgs/instruction-out-1-4/1010-buttons.jpg

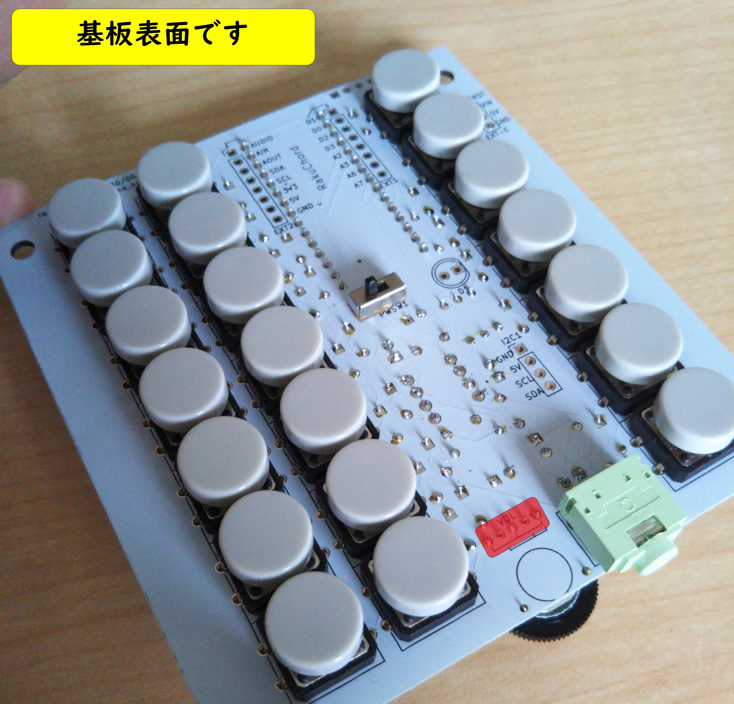
docs/imgs/instruction-out-1-4/1010-buttons.jpg
