inajob/rakuchord/docs/imgs/instruction-out-1-4/1110-led.jpg

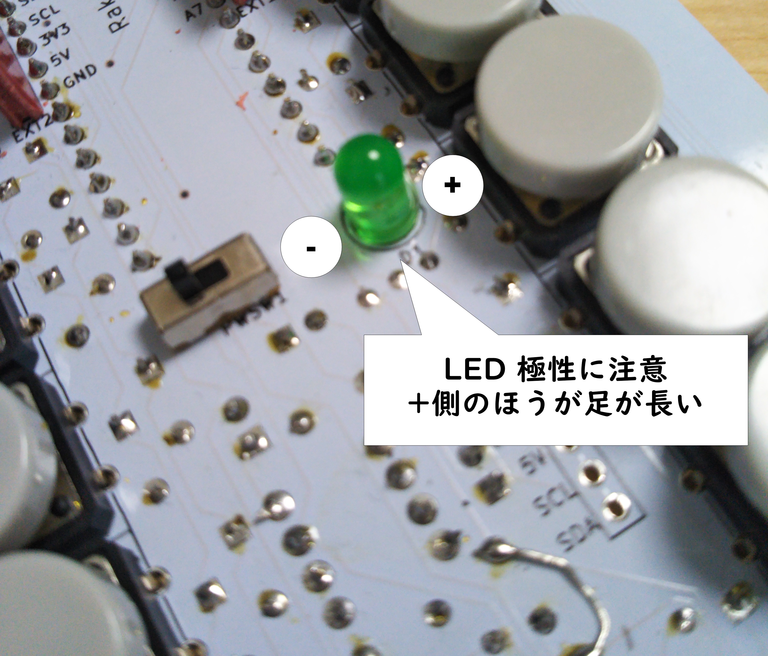
docs/imgs/instruction-out-1-4/1110-led.jpg
