inajob/rakuchord/docs/imgs/instruction-out-1-4/1710-oled-mount.jpg

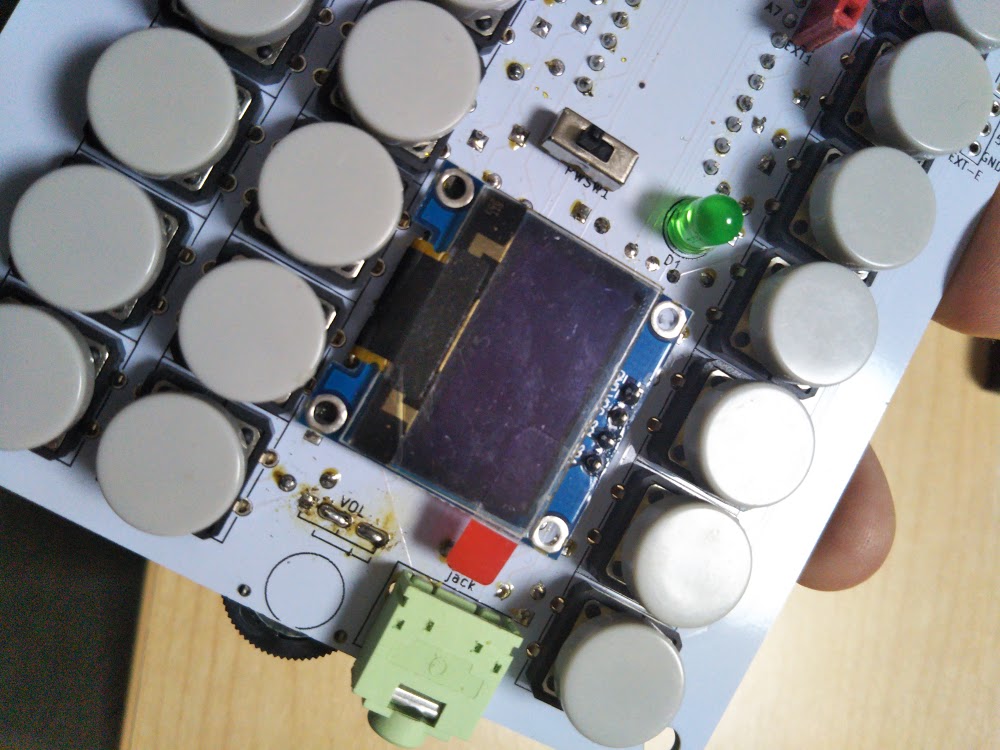
docs/imgs/instruction-out-1-4/1710-oled-mount.jpg
