inajob/rakuchord/docs/imgs/instruction-out-1-4/1720-oled-check.jpg

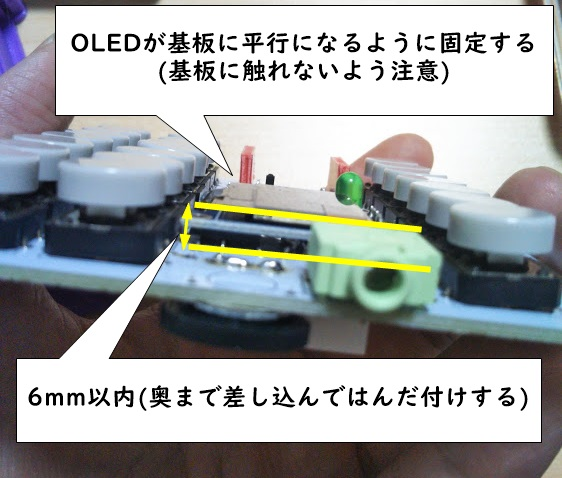
docs/imgs/instruction-out-1-4/1720-oled-check.jpg
