inajob/rakuchord/docs/imgs/instruction-out-1-4/1810-speaker.jpg

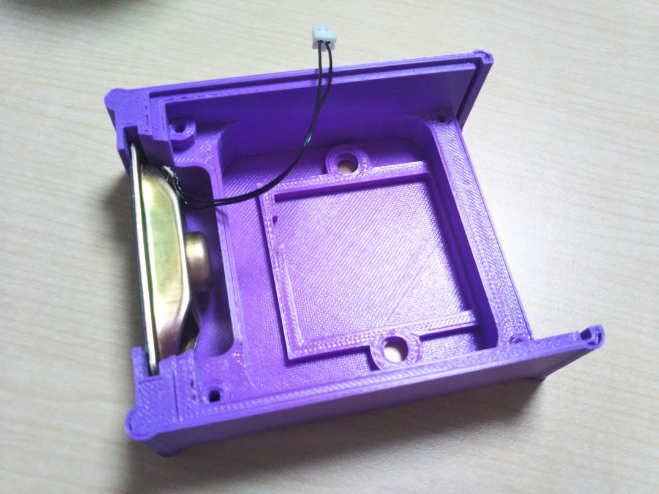
docs/imgs/instruction-out-1-4/1810-speaker.jpg
