inajob/rakuchord/docs/imgs/instruction-out-1-4/1820-battery.jpg

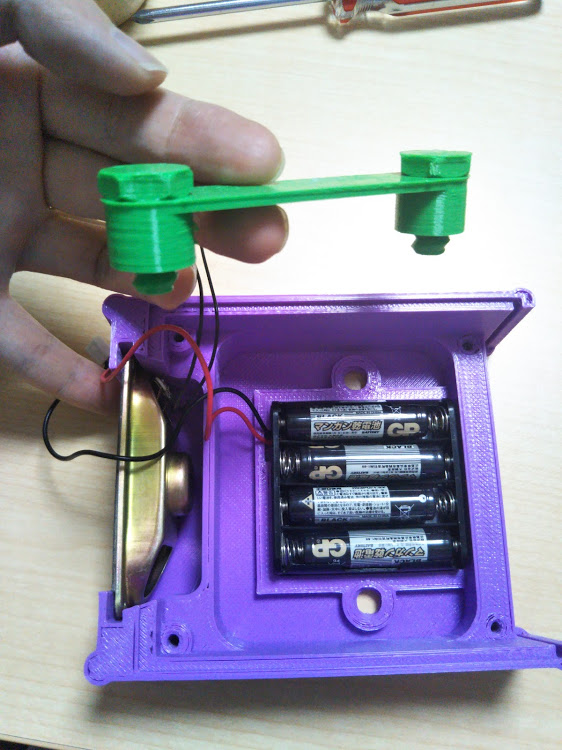
docs/imgs/instruction-out-1-4/1820-battery.jpg
