inajob/rakuchord/docs/imgs/instruction-out-1-4/1910-nut.jpg

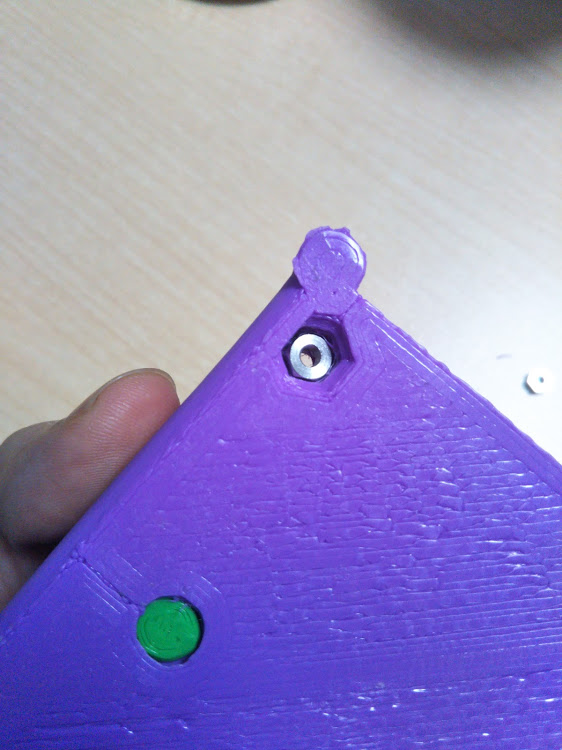
docs/imgs/instruction-out-1-4/1910-nut.jpg
