inajob/rakuchord/docs/imgs/instruction-out-1-4/1920-driver.jpg

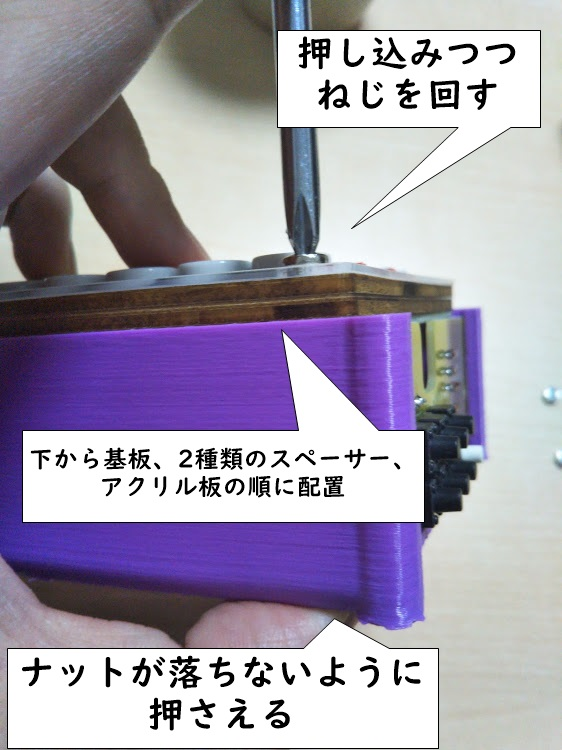
docs/imgs/instruction-out-1-4/1920-driver.jpg
