inajob/rakuchord/docs/imgs/instruction-out-1-4/1930-bottom-nut.jpg

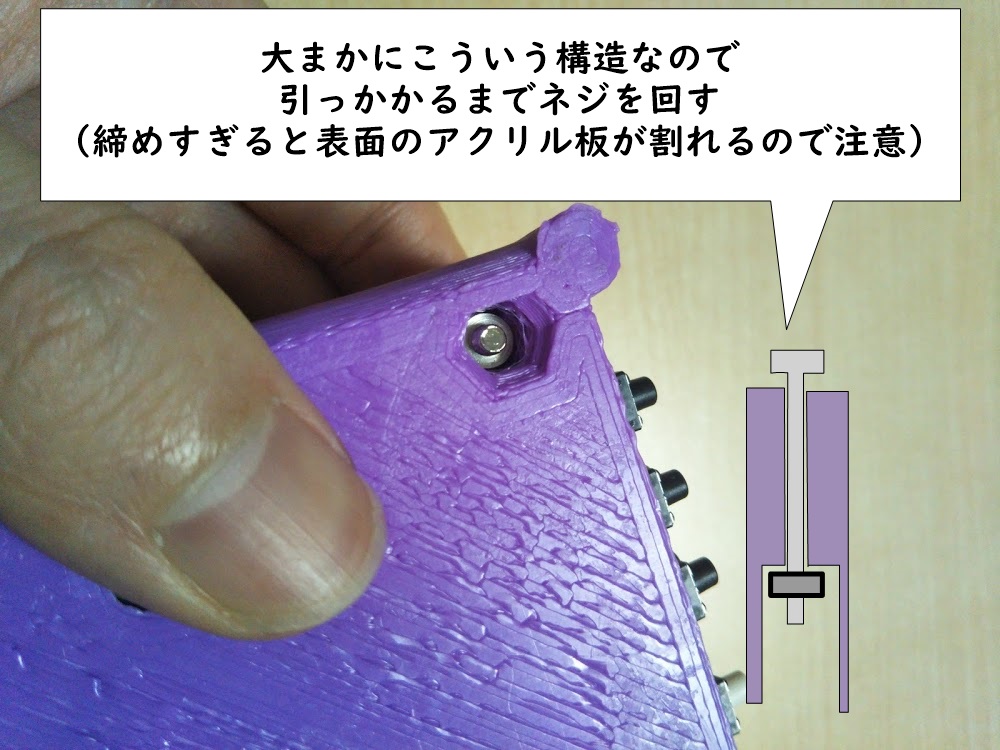
docs/imgs/instruction-out-1-4/1930-bottom-nut.jpg
