inajob/rakuchord/docs/imgs/instruction-out-3/0410-ecap.jpg

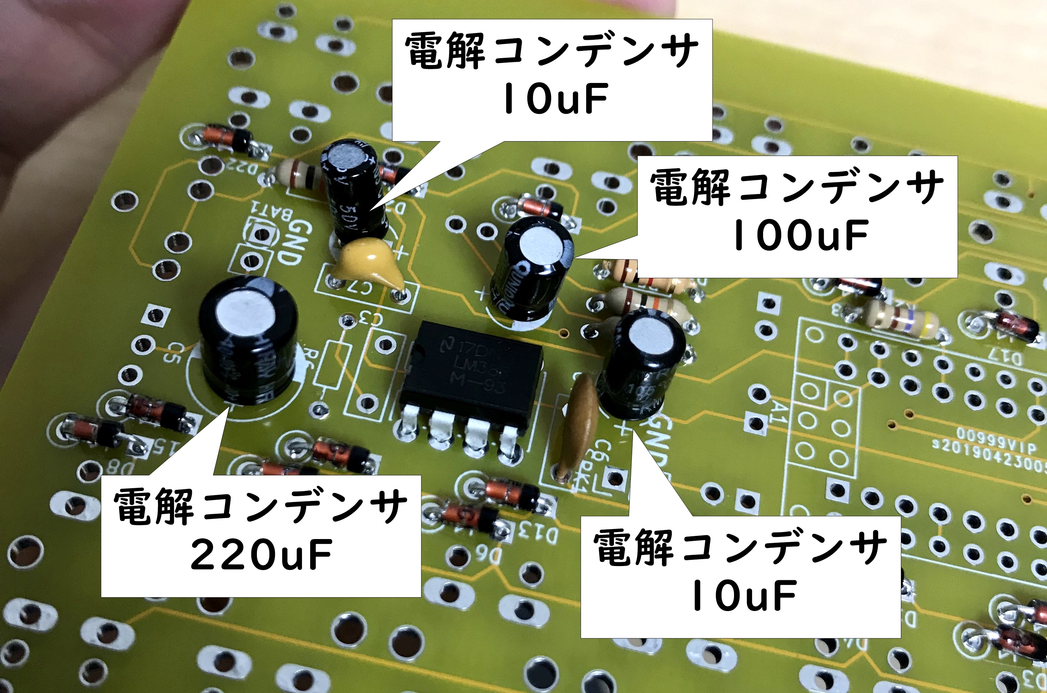
docs/imgs/instruction-out-3/0410-ecap.jpg
