inajob/rakuchord/docs/imgs/instruction-out-3/0510-connector.jpg

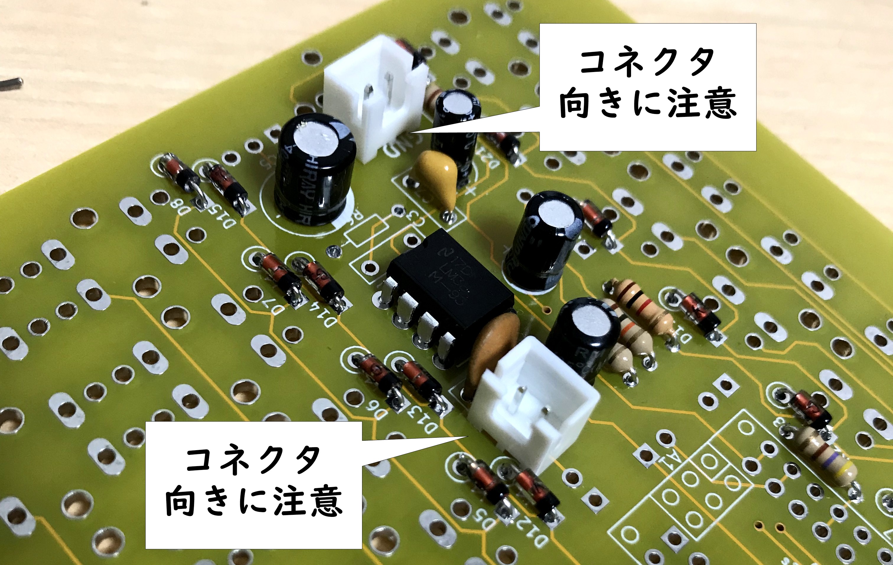
docs/imgs/instruction-out-3/0510-connector.jpg
