inajob/rakuchord/docs/imgs/instruction-out-3/0720-switch-back.jpg

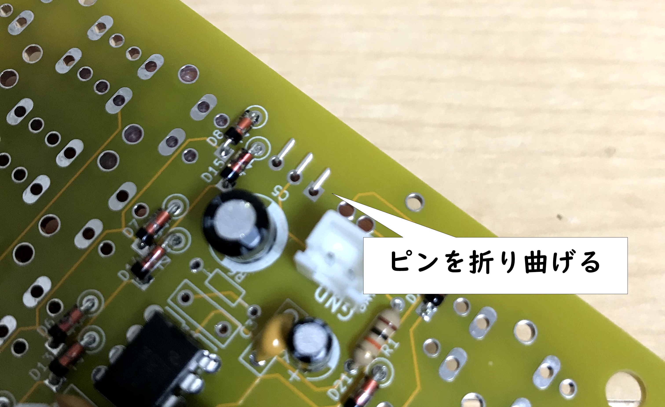
docs/imgs/instruction-out-3/0720-switch-back.jpg
