inajob/rakuchord/docs/imgs/instruction-out-next/0000-board.jpg

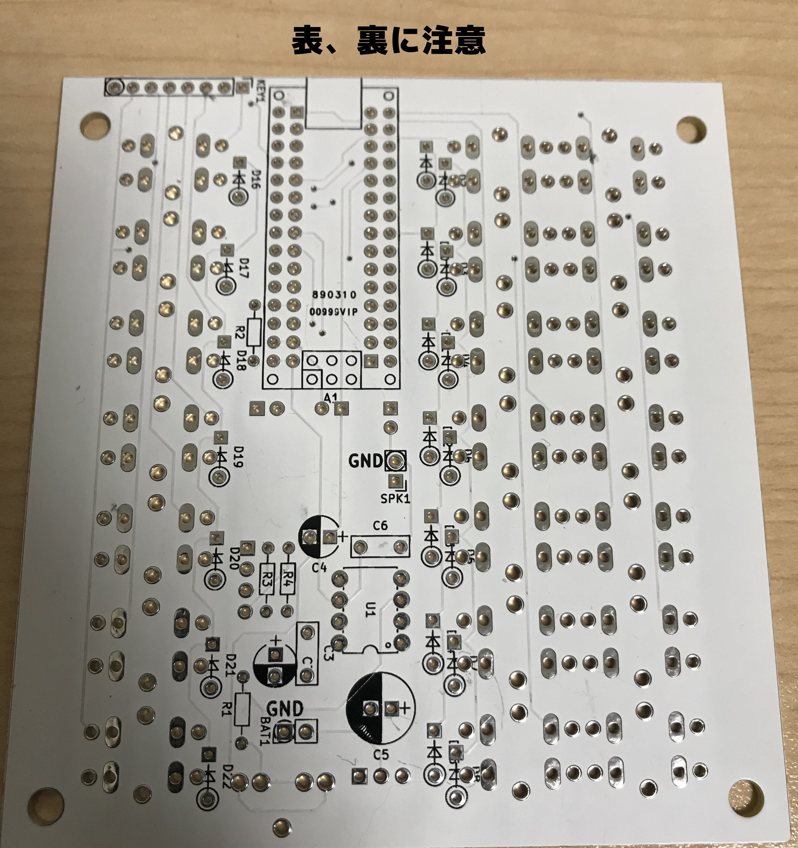
docs/imgs/instruction-out-next/0000-board.jpg
