inajob/rakuchord/docs/imgs/instruction-out-next/0100-diode.jpg

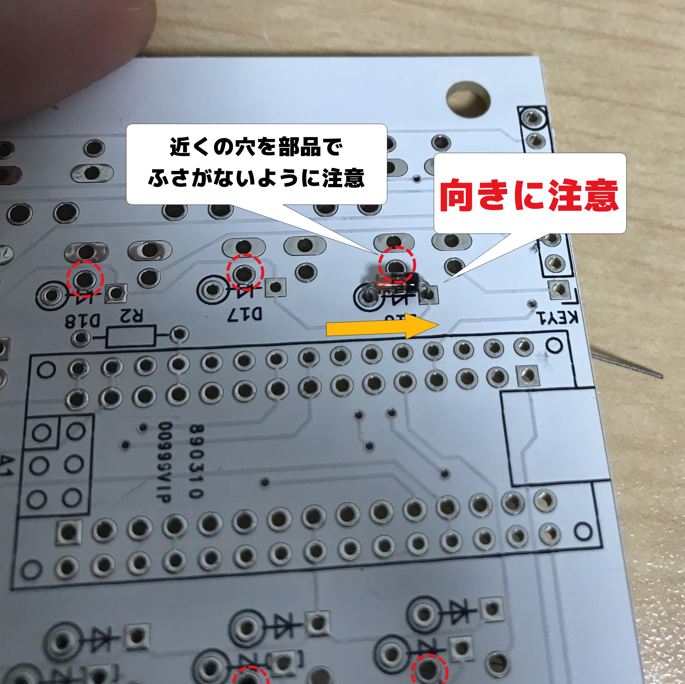
docs/imgs/instruction-out-next/0100-diode.jpg
