inajob/rakuchord/docs/imgs/instruction-out-next/0130-diode-back.jpg

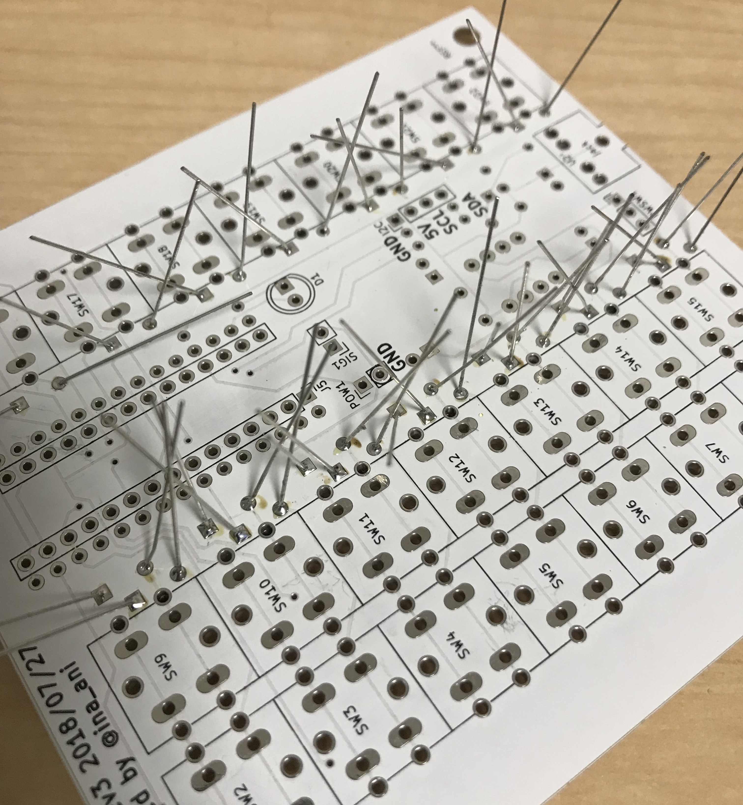
docs/imgs/instruction-out-next/0130-diode-back.jpg
