inajob/rakuchord/docs/imgs/instruction-out-next/0140-diode-pilers.jpg

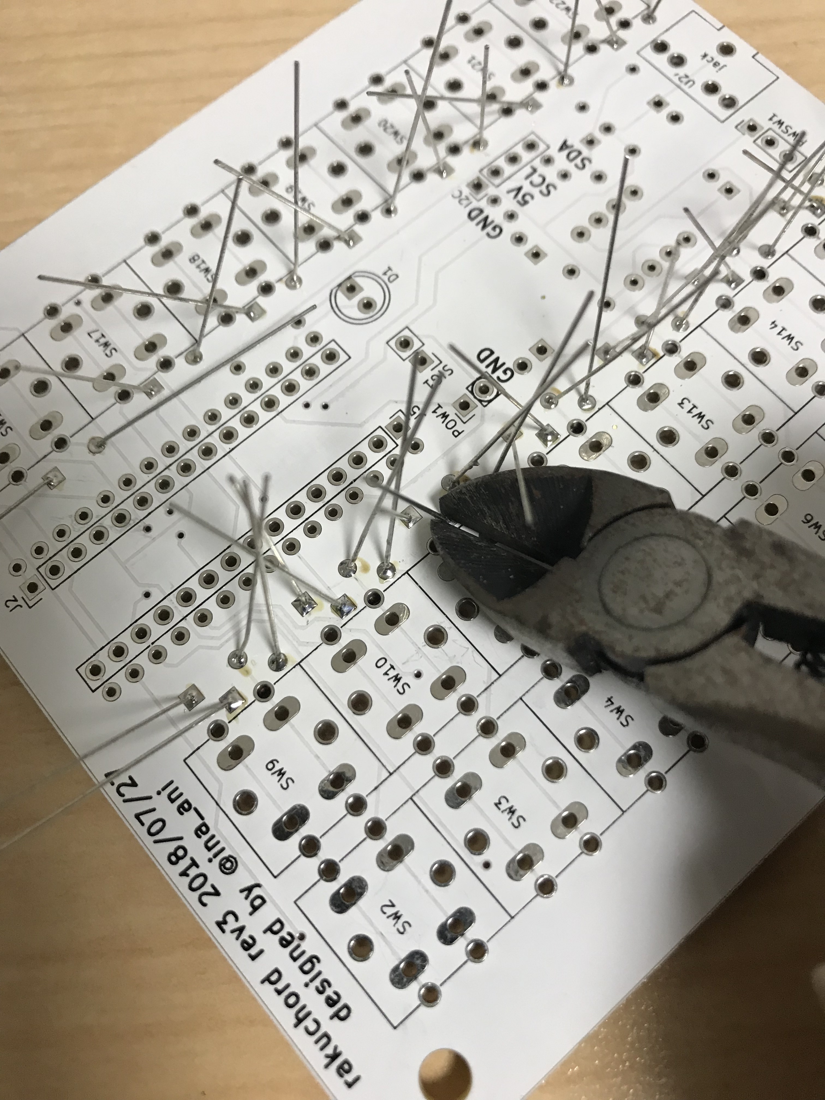
docs/imgs/instruction-out-next/0140-diode-pilers.jpg
