inajob/rakuchord/docs/imgs/instruction-out-next/0150-diode-back-comp.jpg

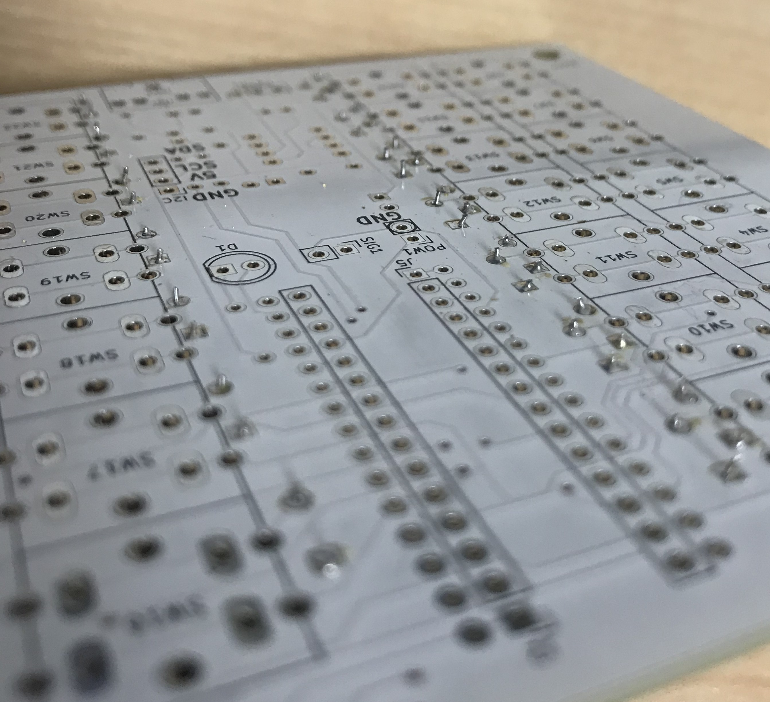
docs/imgs/instruction-out-next/0150-diode-back-comp.jpg
