inajob/rakuchord/docs/imgs/instruction-out-next/0210-register.jpg

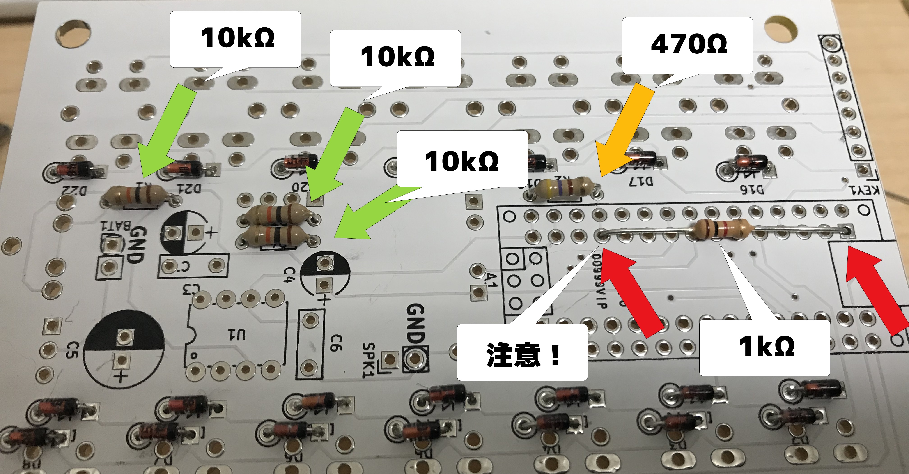
docs/imgs/instruction-out-next/0210-register.jpg
