inajob/rakuchord/docs/imgs/instruction-out-next/0310-amp.jpg

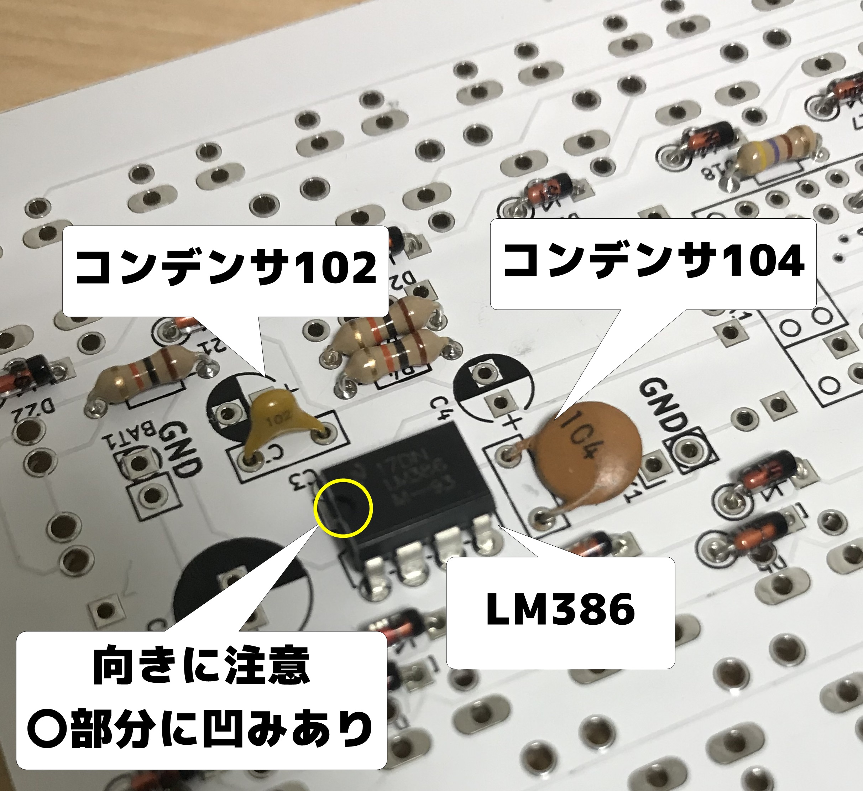
docs/imgs/instruction-out-next/0310-amp.jpg
