inajob/rakuchord/docs/imgs/instruction-out-next/0410-ecap.jpg

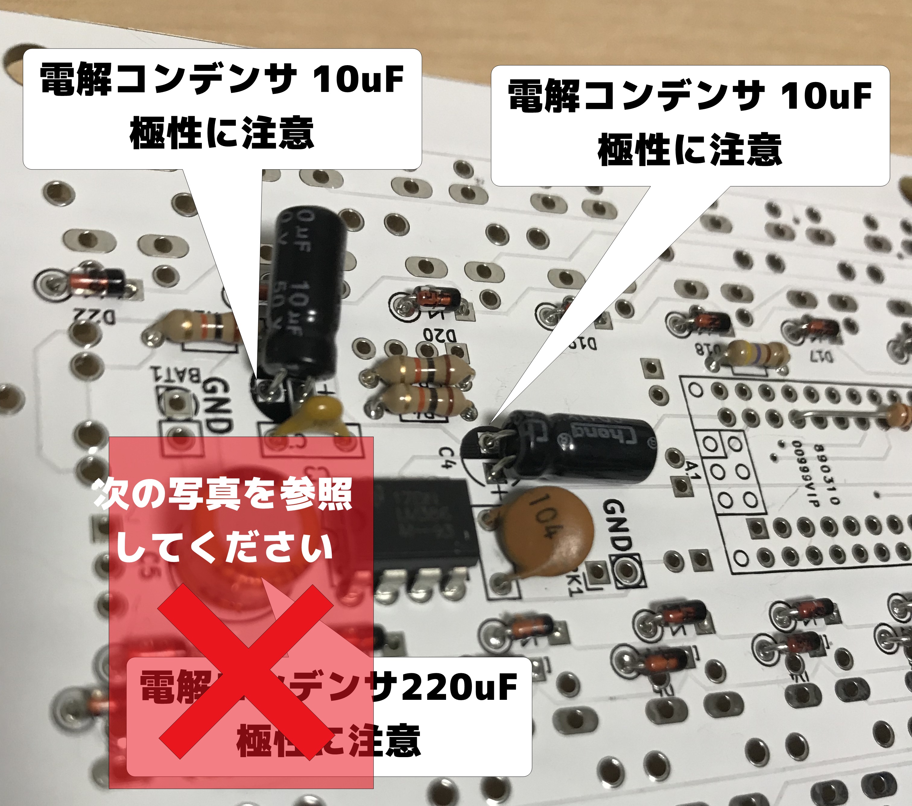
docs/imgs/instruction-out-next/0410-ecap.jpg
