inajob/rakuchord/docs/imgs/instruction-out-next/0420-econ-warning.jpg

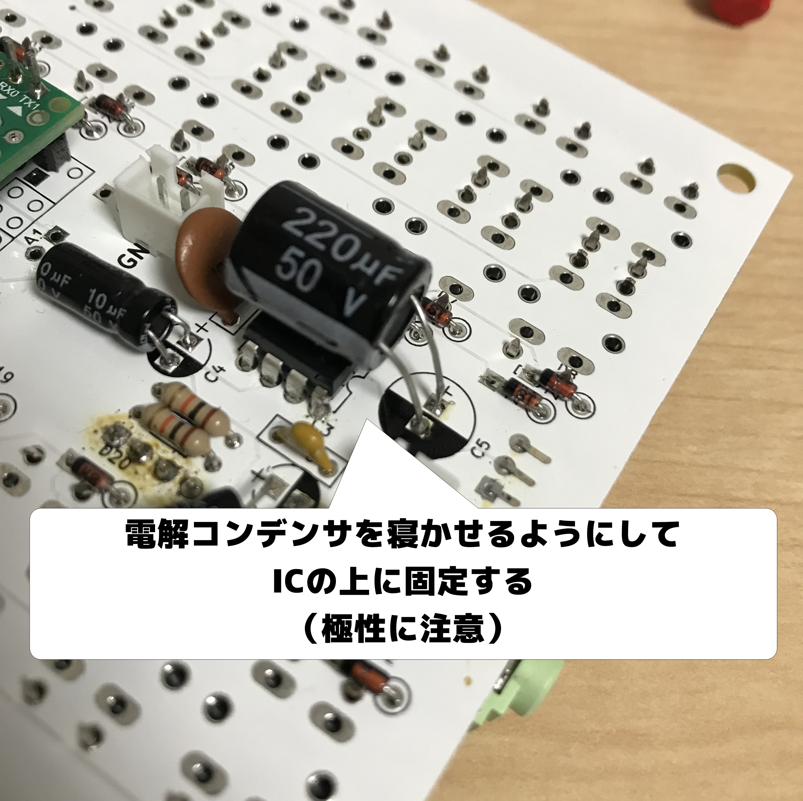
docs/imgs/instruction-out-next/0420-econ-warning.jpg
