inajob/rakuchord/docs/imgs/instruction-out-next/0510-connector.jpg

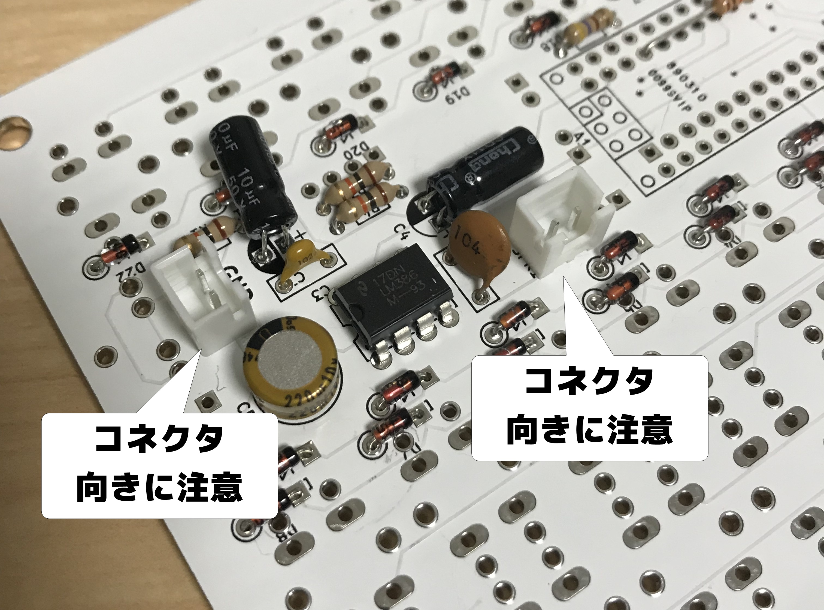
docs/imgs/instruction-out-next/0510-connector.jpg
