inajob/rakuchord/docs/imgs/instruction-out-next/0610-arduino.jpg

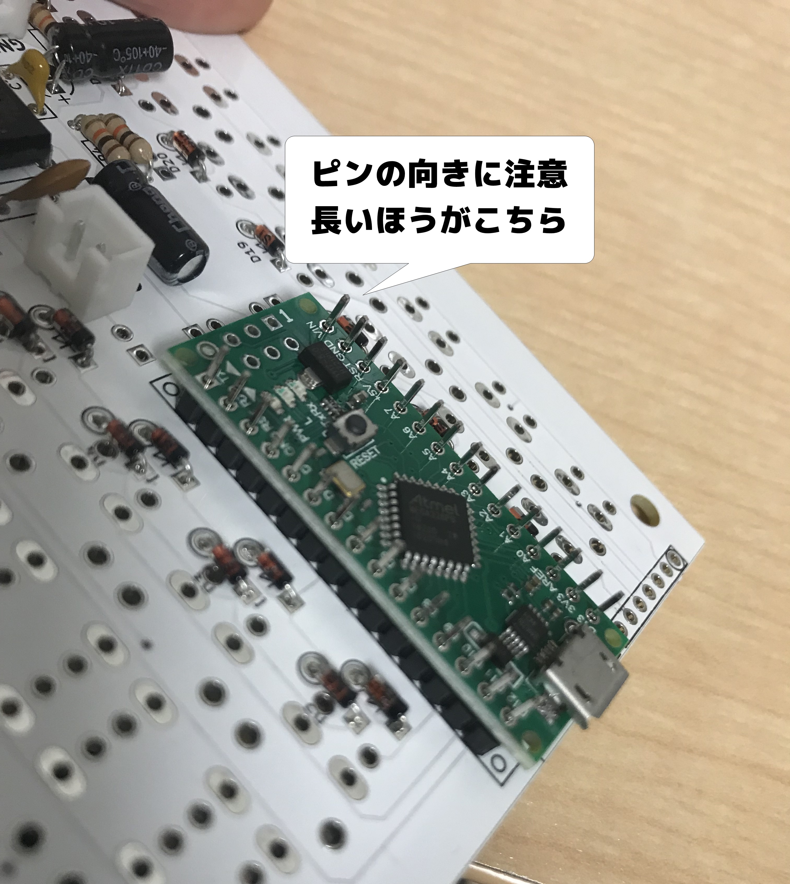
docs/imgs/instruction-out-next/0610-arduino.jpg
