inajob/rakuchord/docs/imgs/instruction-out-next/0620-arduino-back.jpg

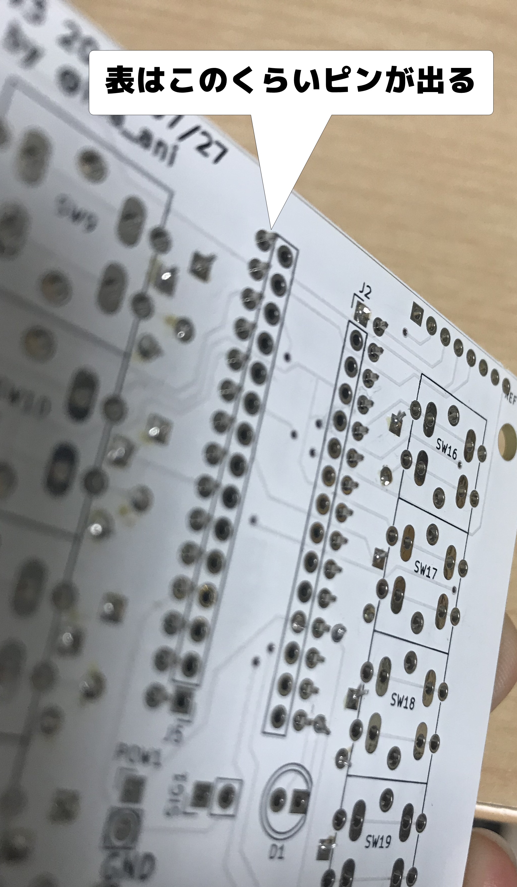
docs/imgs/instruction-out-next/0620-arduino-back.jpg
