inajob/rakuchord/docs/imgs/instruction-out-next/0710-switch.jpg

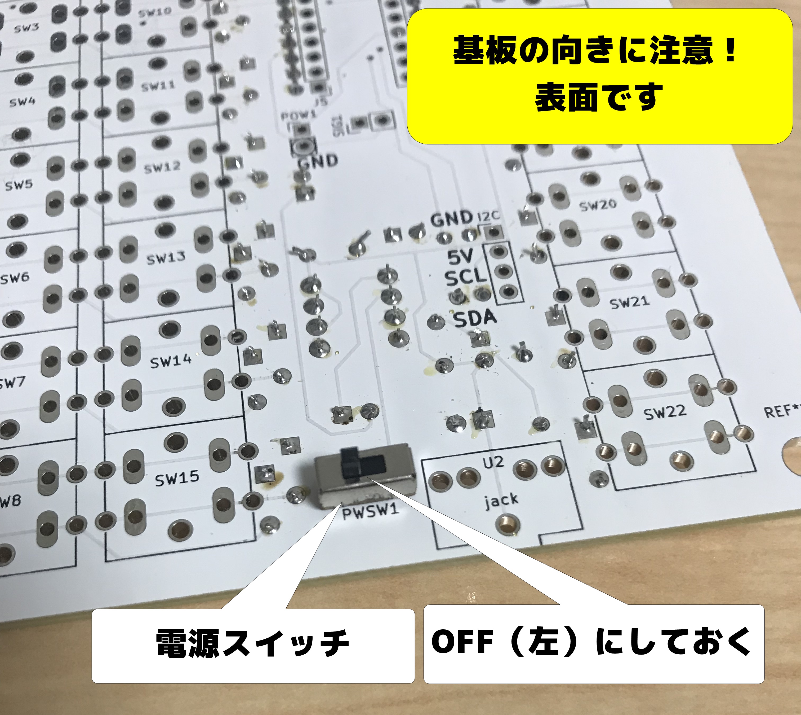
docs/imgs/instruction-out-next/0710-switch.jpg
