inajob/rakuchord/docs/imgs/instruction-out-next/0720-switch-back.jpg

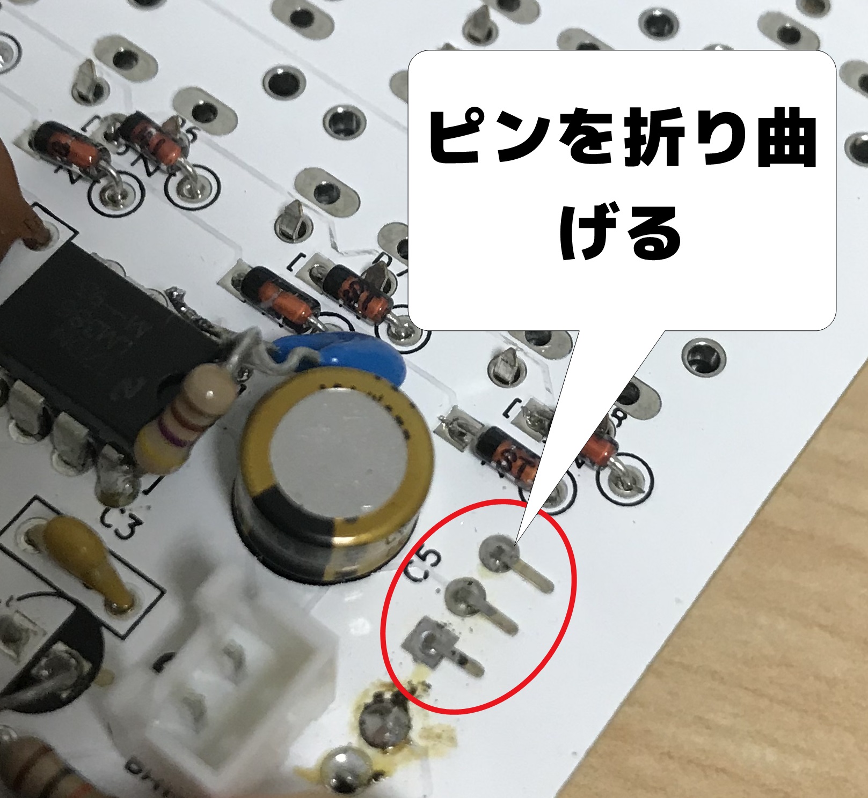
docs/imgs/instruction-out-next/0720-switch-back.jpg
