inajob/rakuchord/docs/imgs/instruction-out-next/0810-jack.jpg

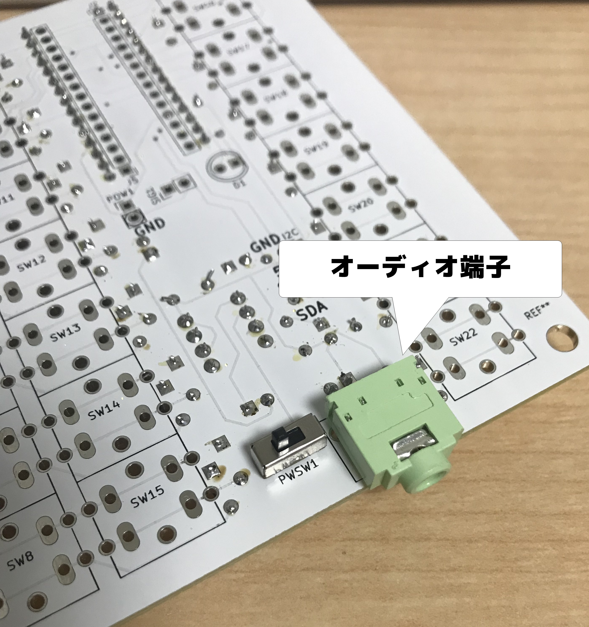
docs/imgs/instruction-out-next/0810-jack.jpg
