inajob/rakuchord/docs/imgs/instruction-out-next/0910-check.jpg

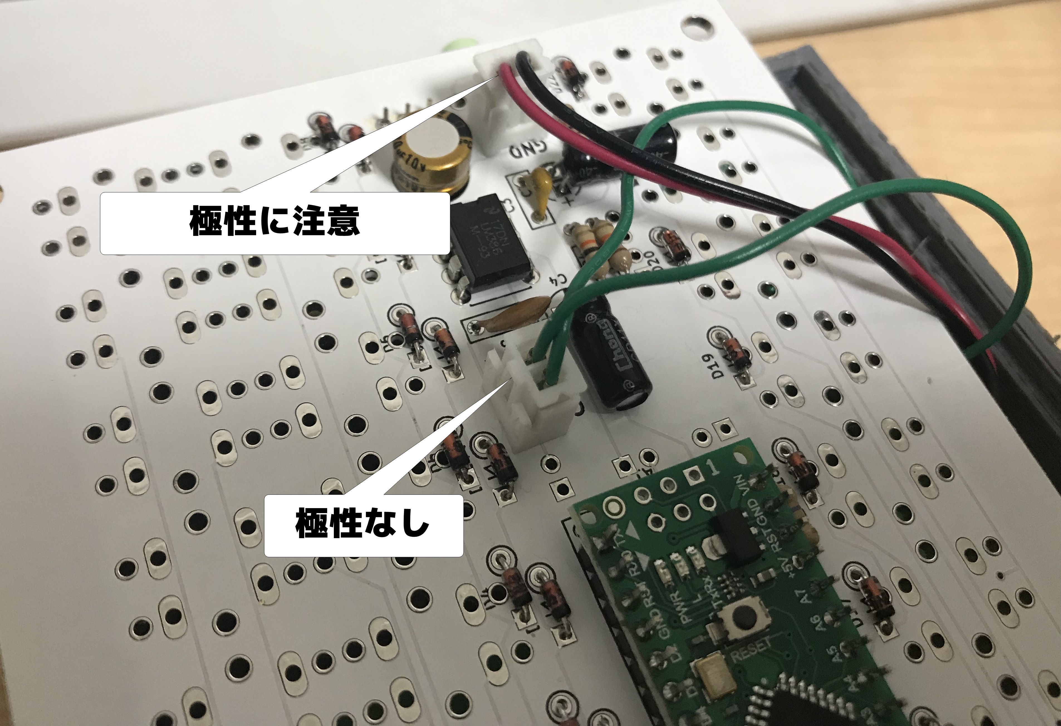
docs/imgs/instruction-out-next/0910-check.jpg
