inajob/rakuchord/docs/imgs/instruction-out-next/1010-buttons.jpg

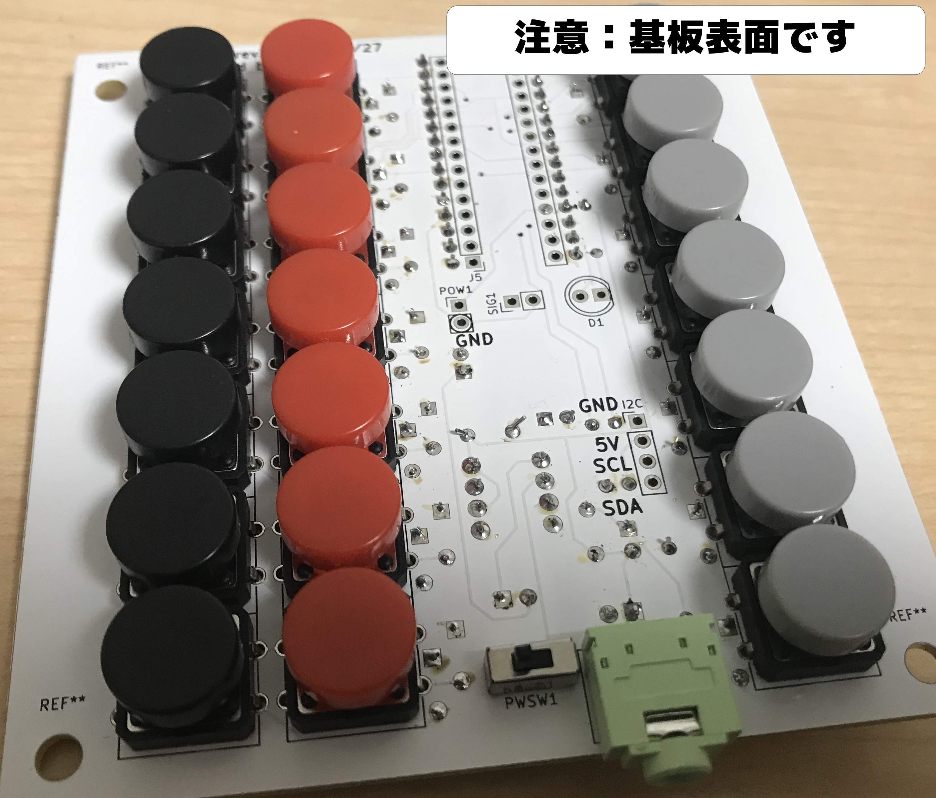
docs/imgs/instruction-out-next/1010-buttons.jpg
