inajob/rakuchord/docs/imgs/instruction-out-next/1110-led.jpg

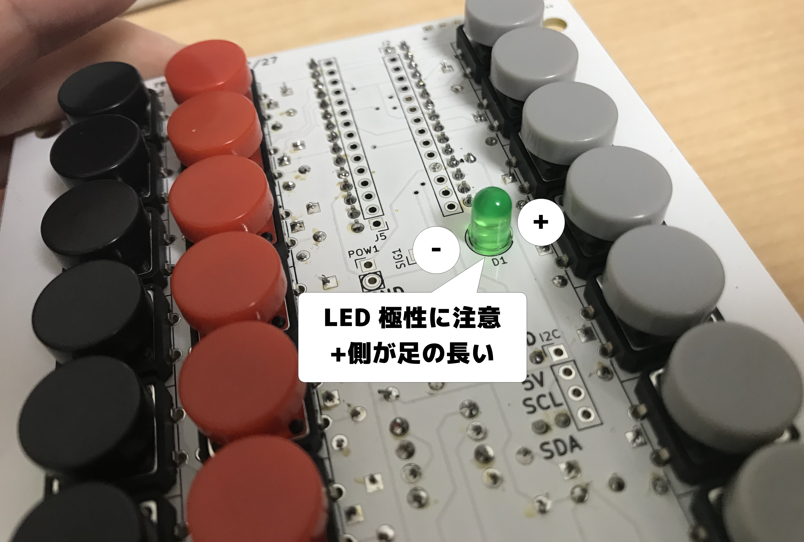
docs/imgs/instruction-out-next/1110-led.jpg
