inajob/rakuchord/docs/imgs/instruction-out-next/1210-diode.jpg

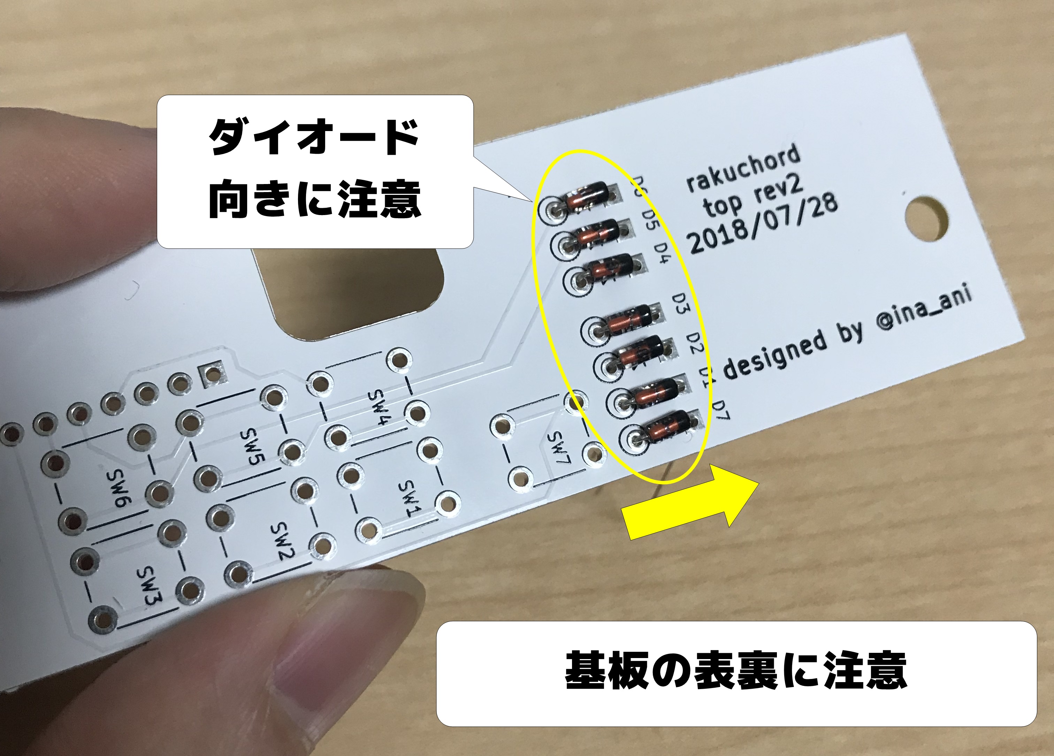
docs/imgs/instruction-out-next/1210-diode.jpg
