inajob/rakuchord/docs/imgs/instruction-out-next/1310-buttons.jpg

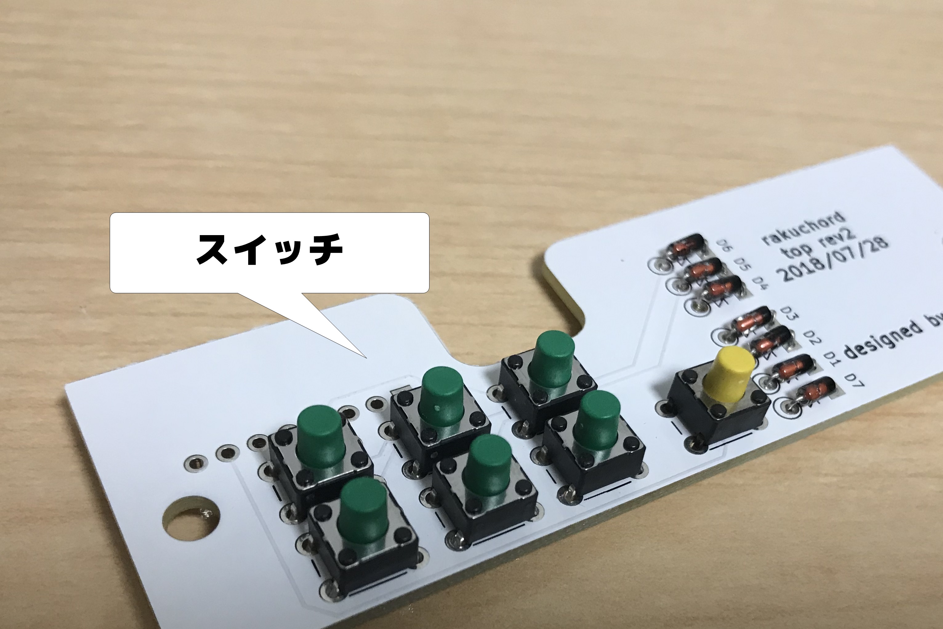
docs/imgs/instruction-out-next/1310-buttons.jpg
