inajob/rakuchord/docs/imgs/instruction-out-next/1410-headers.jpg

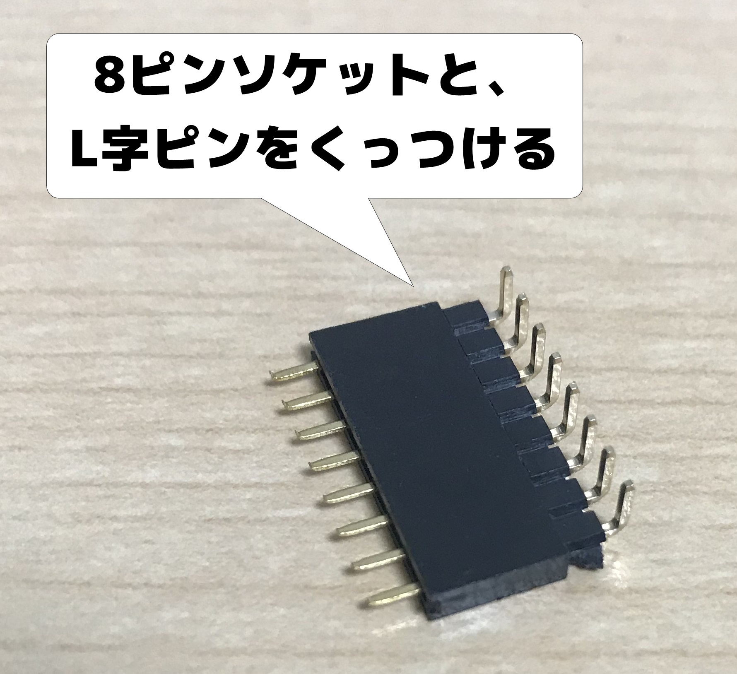
docs/imgs/instruction-out-next/1410-headers.jpg
