inajob/rakuchord/docs/imgs/instruction-out-next/1411-headers.jpg

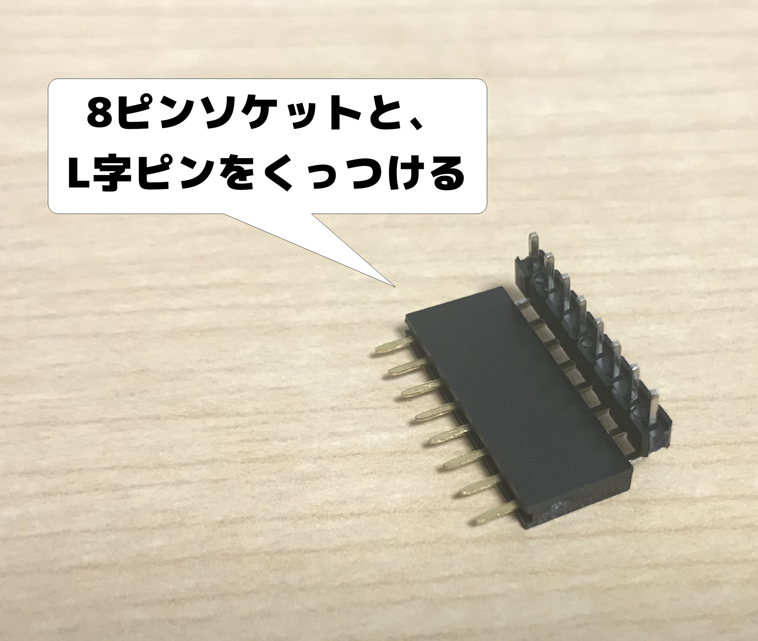
docs/imgs/instruction-out-next/1411-headers.jpg
