inajob/rakuchord/docs/imgs/instruction-out-next/1510-compose.jpg

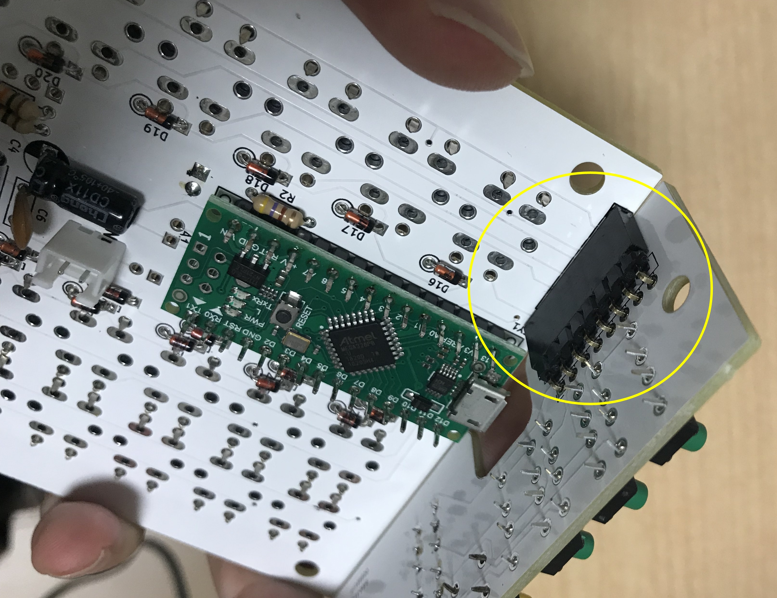
docs/imgs/instruction-out-next/1510-compose.jpg
