inajob/rakuchord/docs/imgs/instruction-out-next/1511-compose.jpg

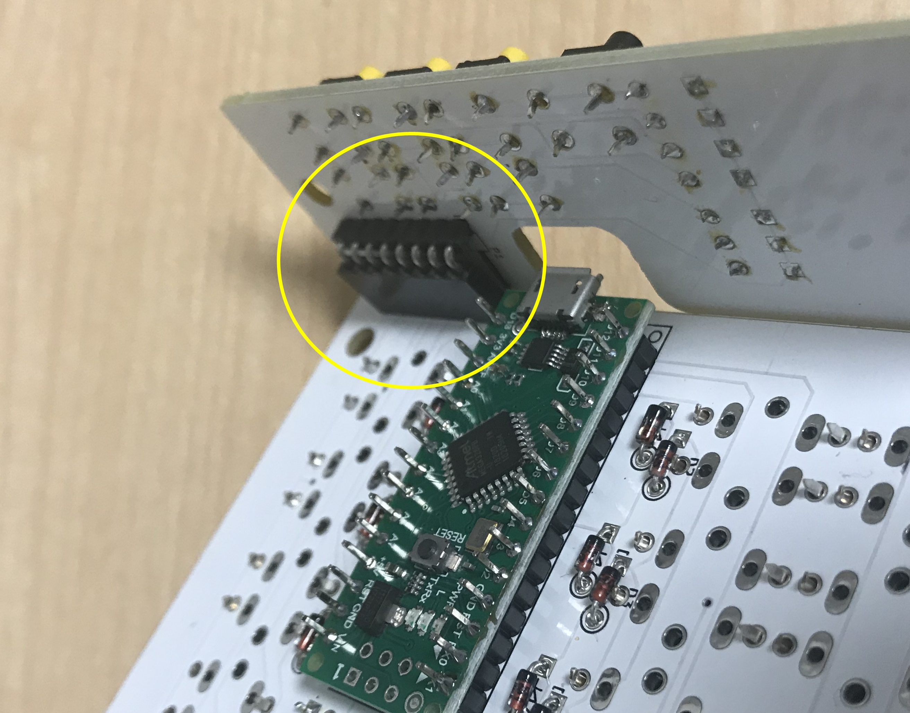
docs/imgs/instruction-out-next/1511-compose.jpg
