inajob/rakuchord/docs/imgs/instruction-out-next/1610-case.jpg

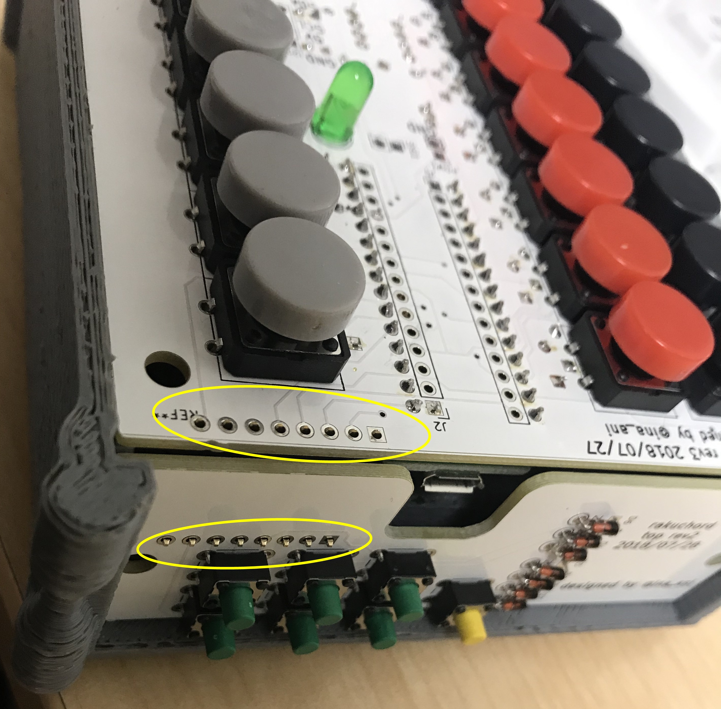
docs/imgs/instruction-out-next/1610-case.jpg
