inajob/rakuchord/docs/imgs/instruction-out-next/1710-oled-mount.jpg

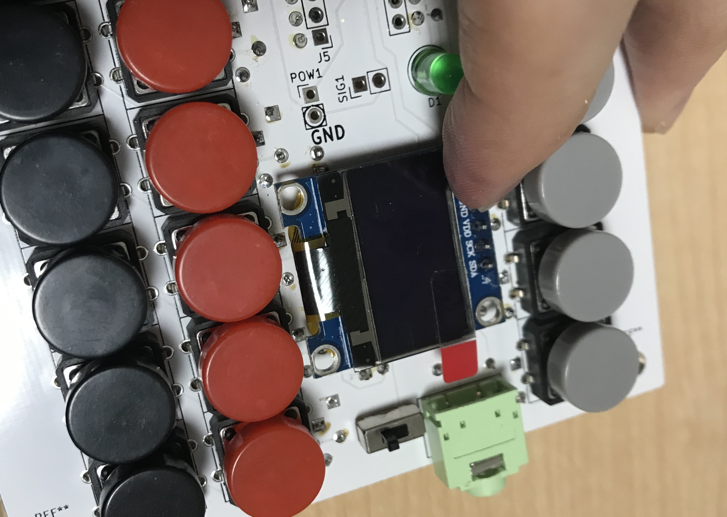
docs/imgs/instruction-out-next/1710-oled-mount.jpg
