inajob/rakuchord/docs/imgs/instruction-out-next/1720-oled-check.jpg

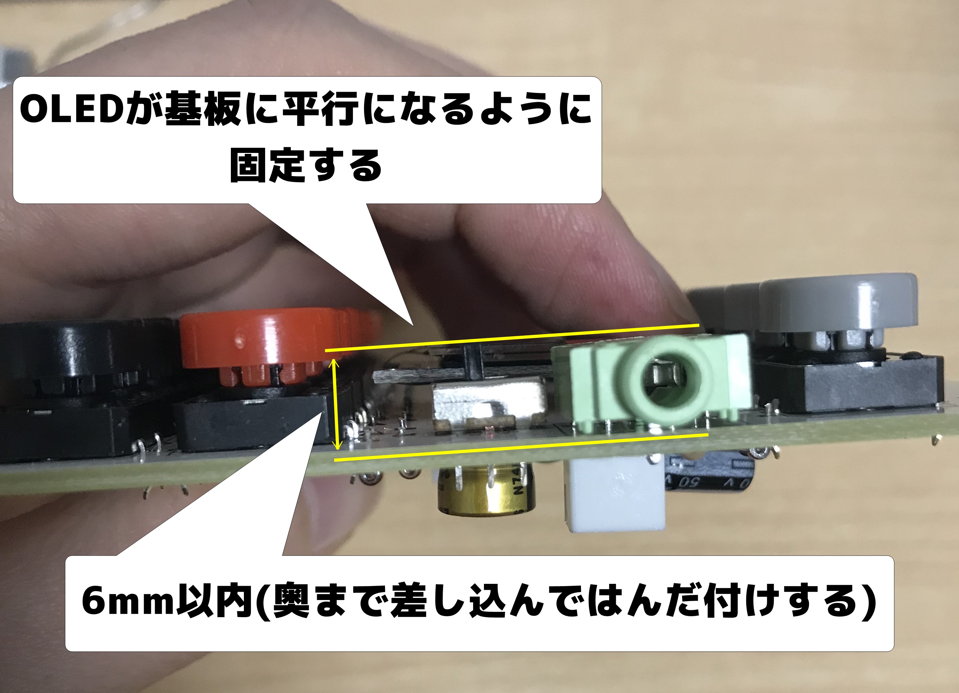
docs/imgs/instruction-out-next/1720-oled-check.jpg
