inajob/rakuchord/docs/imgs/instruction-out-next/1730-oled-check2.jpg

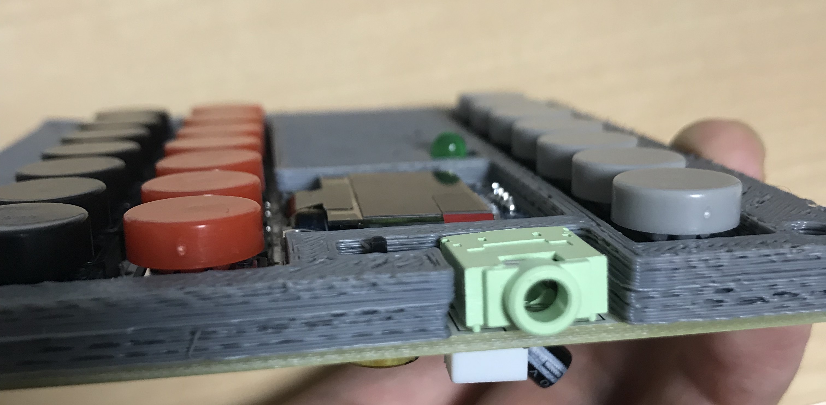
docs/imgs/instruction-out-next/1730-oled-check2.jpg
