inajob/rakuchord/docs/imgs/instruction-out-next/1810-finish.jpg

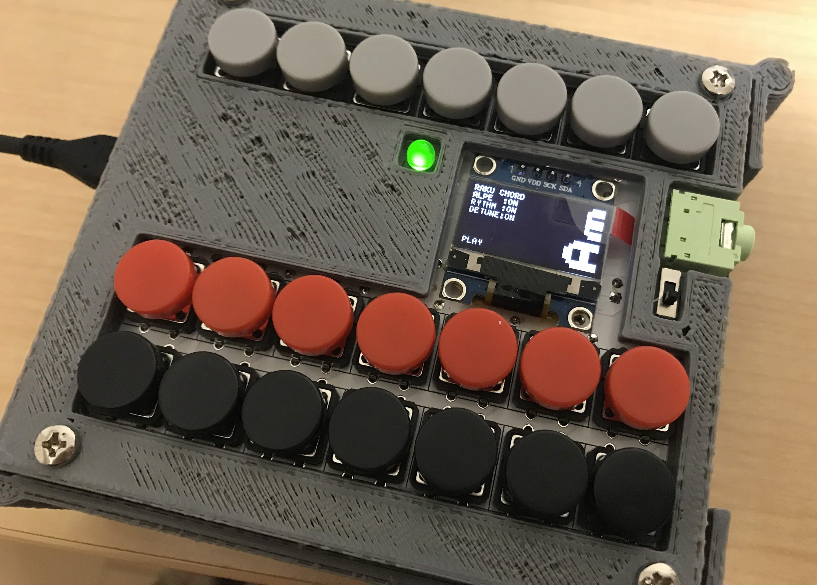
docs/imgs/instruction-out-next/1810-finish.jpg
