inajob/rakuchord/docs/imgs/instruction-out-next/1810-speaker.jpg

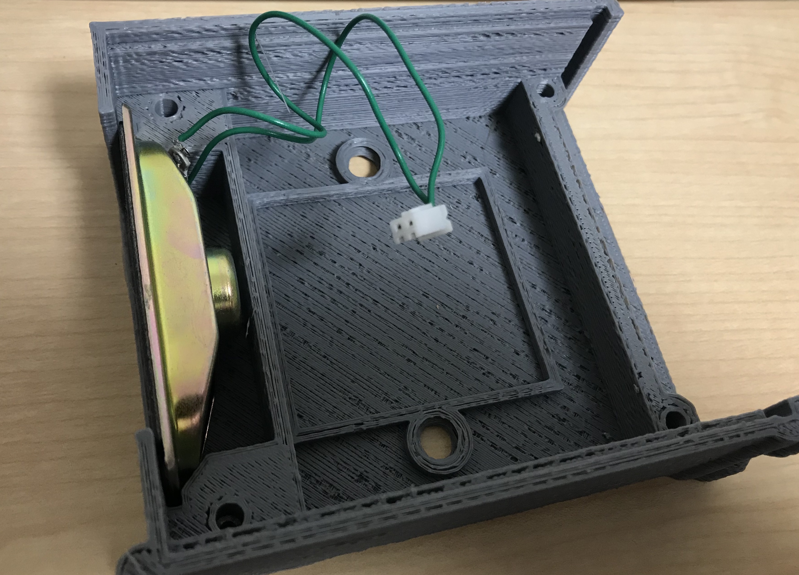
docs/imgs/instruction-out-next/1810-speaker.jpg
