inajob/rakuchord/docs/imgs/instruction-out-next/1830-battery-holder.jpg

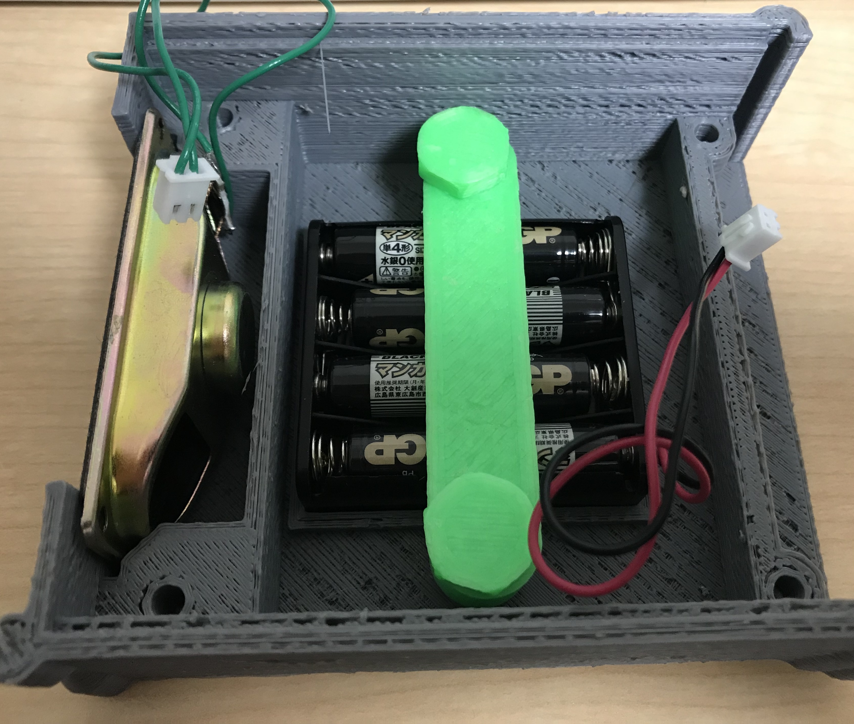
docs/imgs/instruction-out-next/1830-battery-holder.jpg
