inajob/rakuchord/docs/imgs/instruction-out-next/1910-nut.jpg

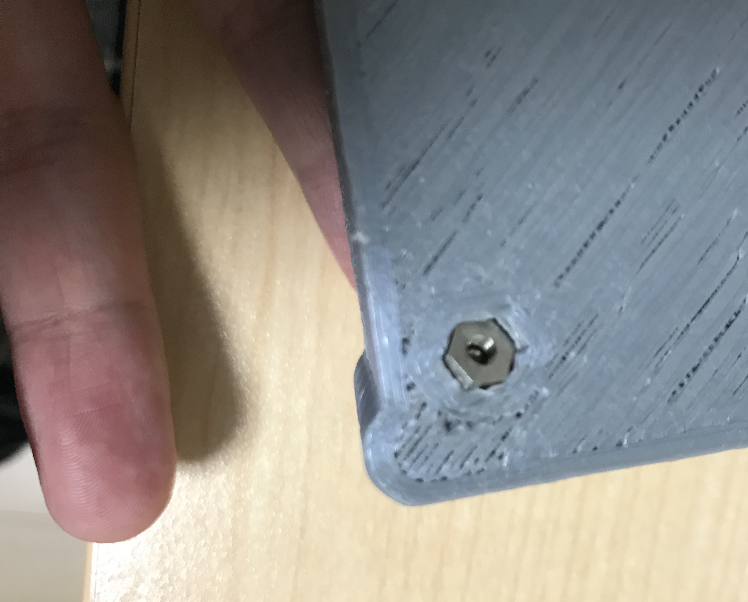
docs/imgs/instruction-out-next/1910-nut.jpg
