inajob/rakuchord/docs/imgs/instruction-out-next/1920-driver.jpg

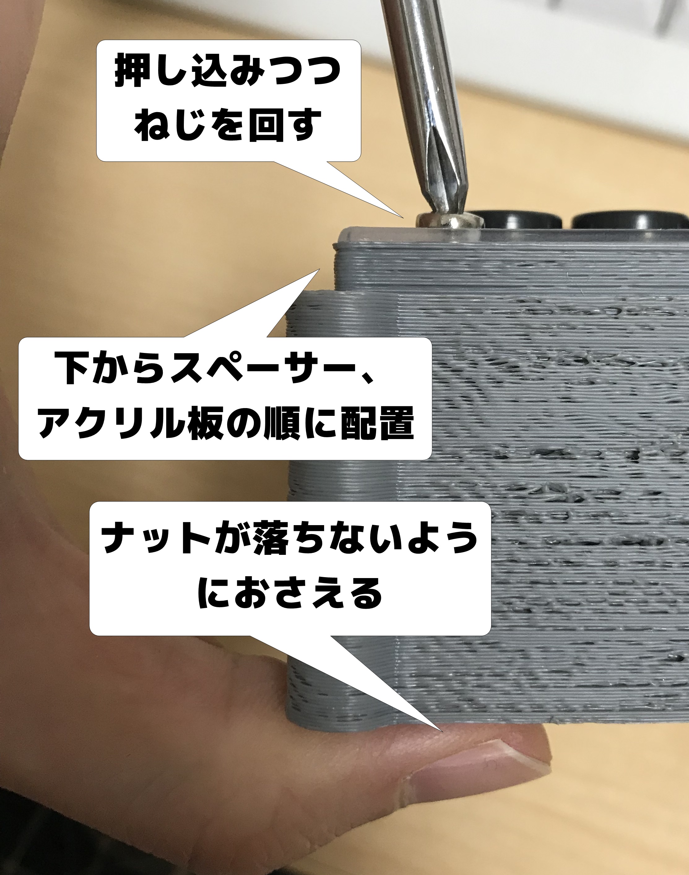
docs/imgs/instruction-out-next/1920-driver.jpg
