inajob/rakuchord/docs/imgs/instruction-out-next/1930-bottom-nut.jpg

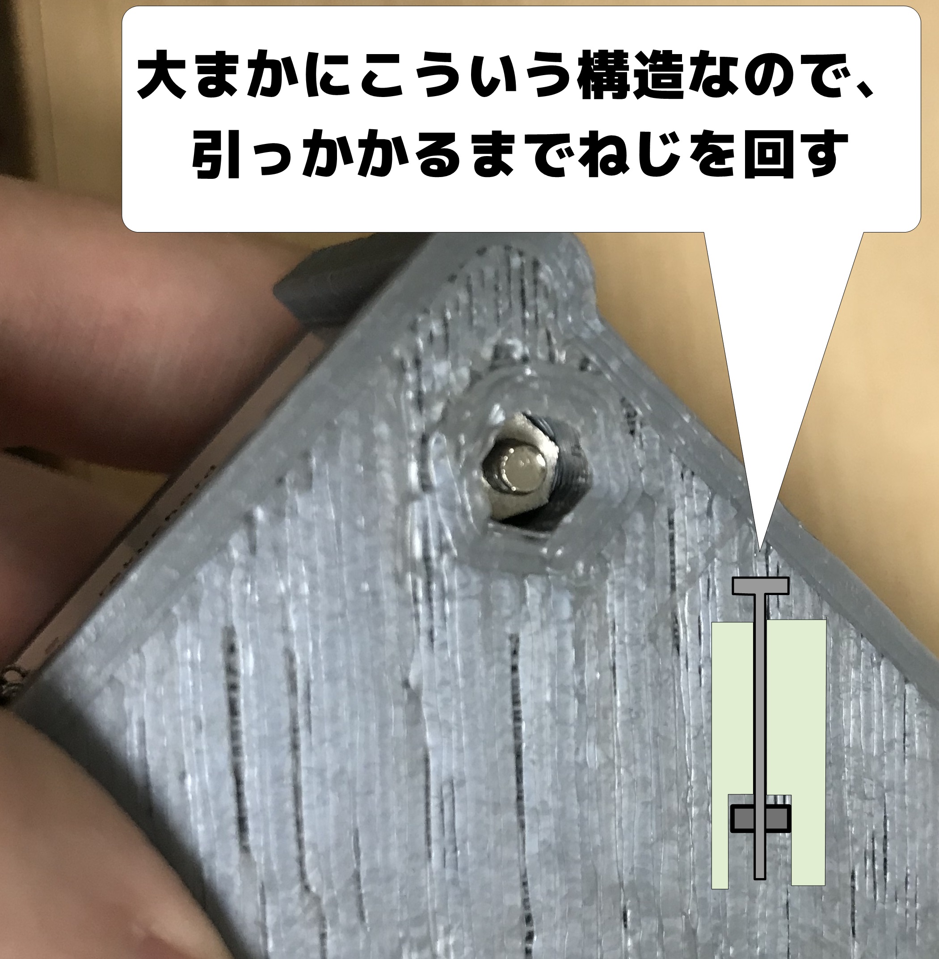
docs/imgs/instruction-out-next/1930-bottom-nut.jpg
