inajob/rakuchord/docs/imgs/instruction-out-next/2010-finish.jpg

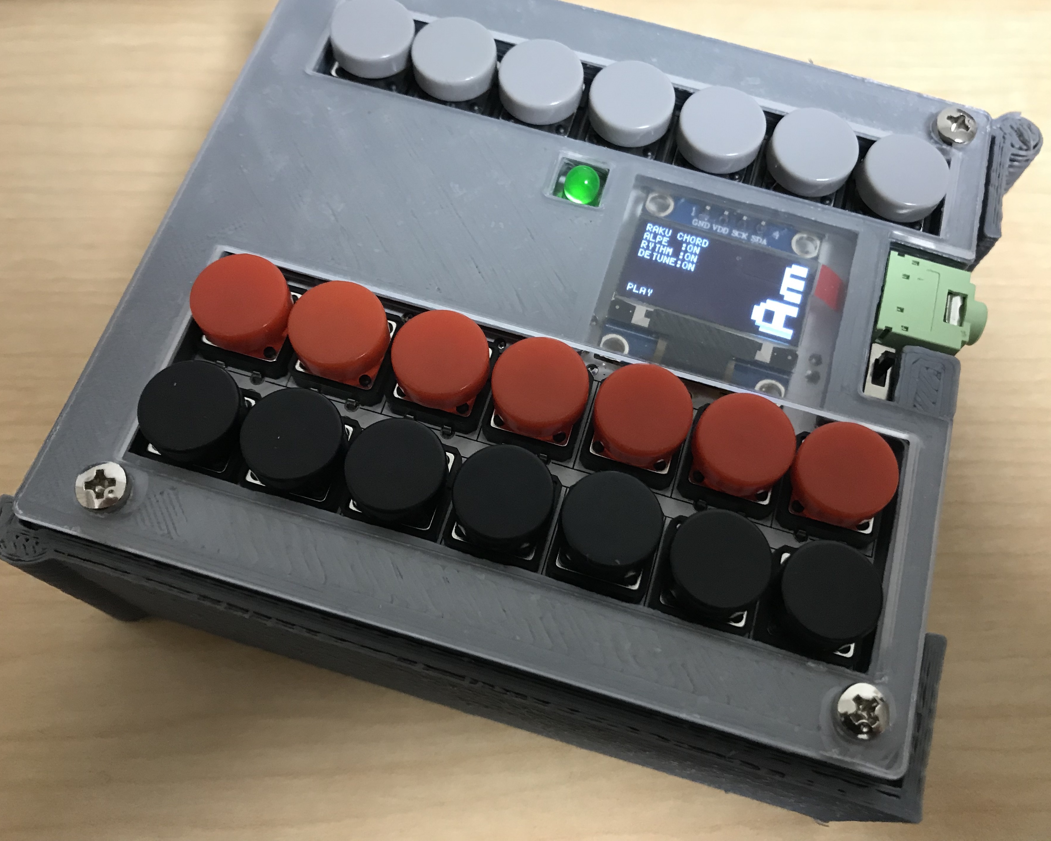
docs/imgs/instruction-out-next/2010-finish.jpg
