inajob/rakuchord/docs/imgs/instruction-out-next/2110-noise-reduction.jpg

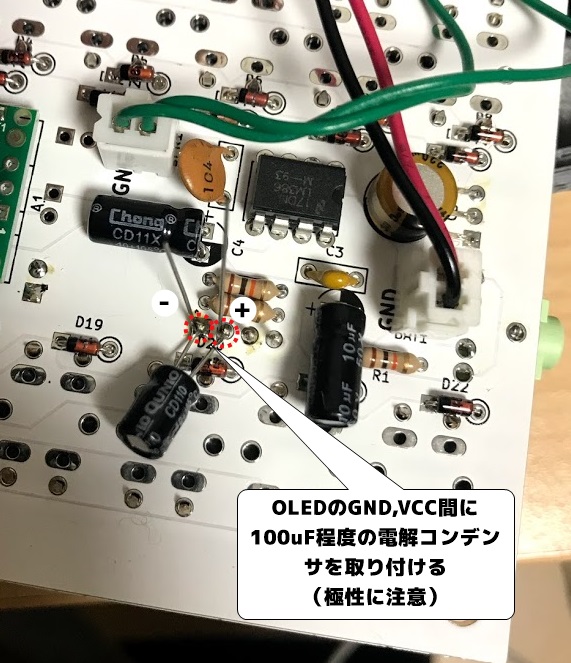
docs/imgs/instruction-out-next/2110-noise-reduction.jpg
