inajob/rakuchord/docs/imgs/instruction-out/018-settle-switch.jpg

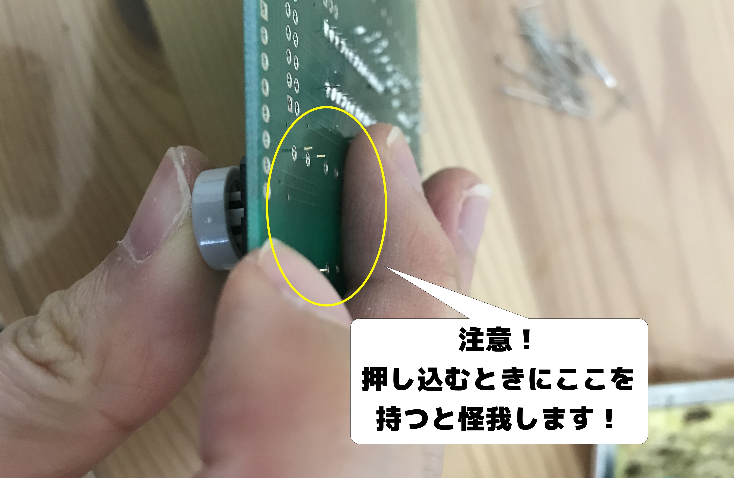
docs/imgs/instruction-out/018-settle-switch.jpg
