inajob/rakuchord/docs/imgs/instruction-out/019-settle-switch2.jpg

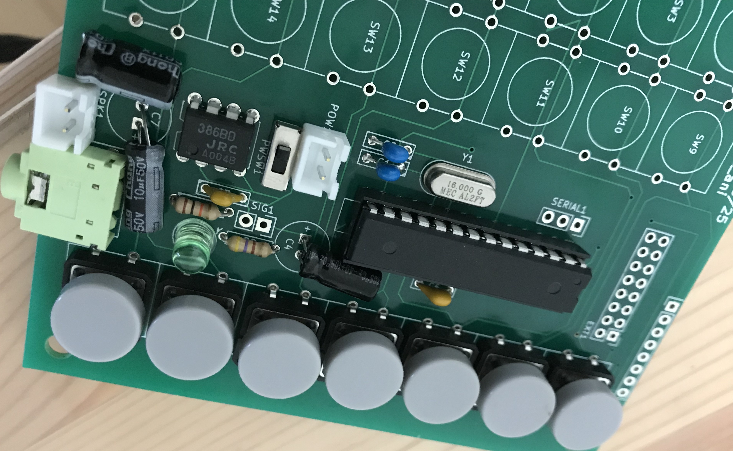
docs/imgs/instruction-out/019-settle-switch2.jpg
