inajob/rakuchord/docs/imgs/instruction-out/020-switch-back.jpg

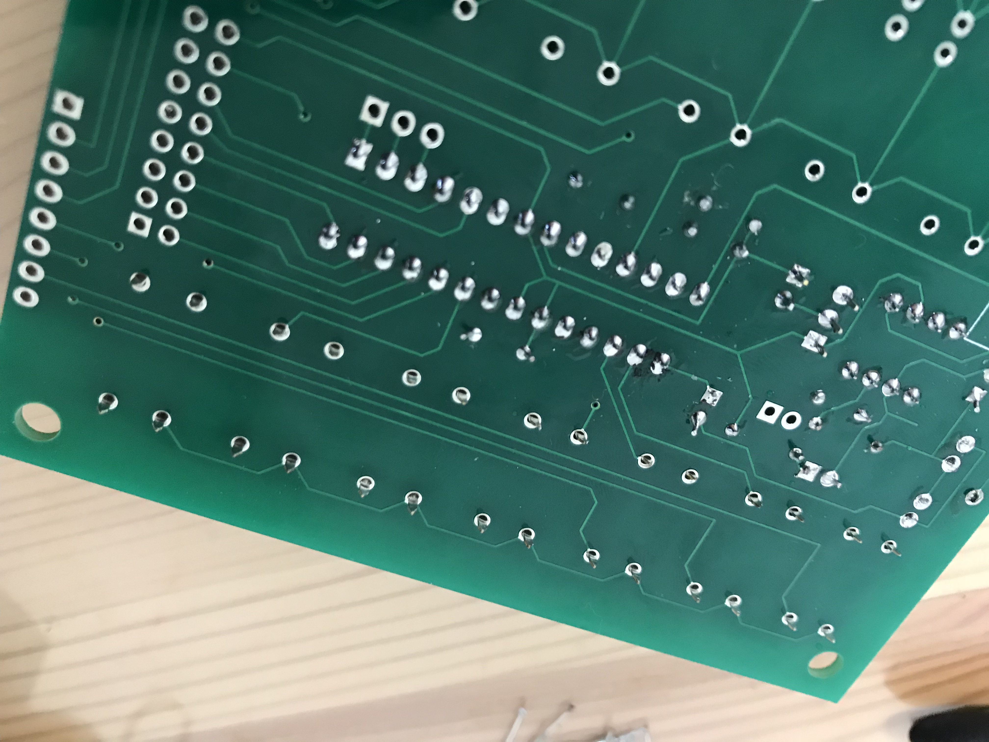
docs/imgs/instruction-out/020-switch-back.jpg
