inajob/rakuchord/docs/imgs/instruction-out/021-switch-back2.jpg

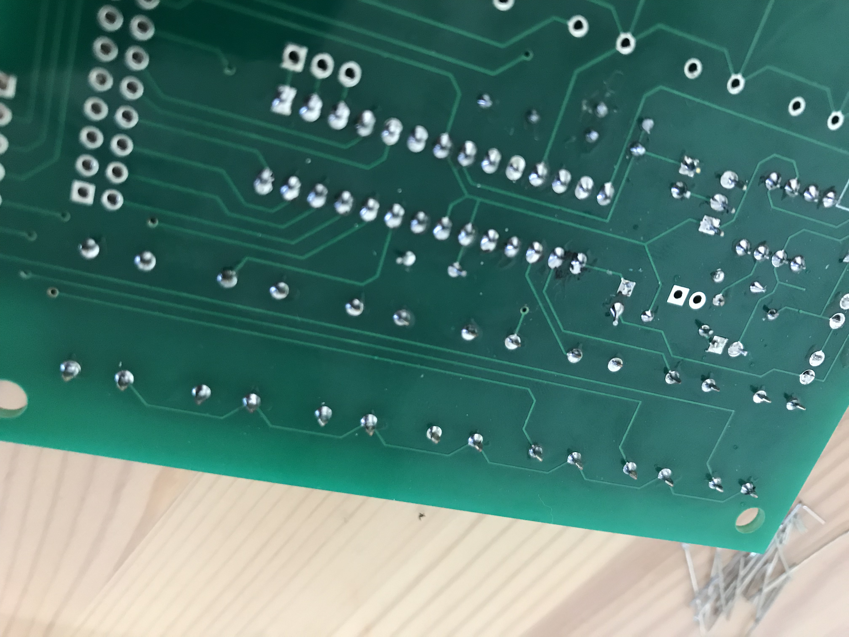
docs/imgs/instruction-out/021-switch-back2.jpg
