inajob/rakuchord/docs/imgs/instruction-out/022-switch-high.jpg

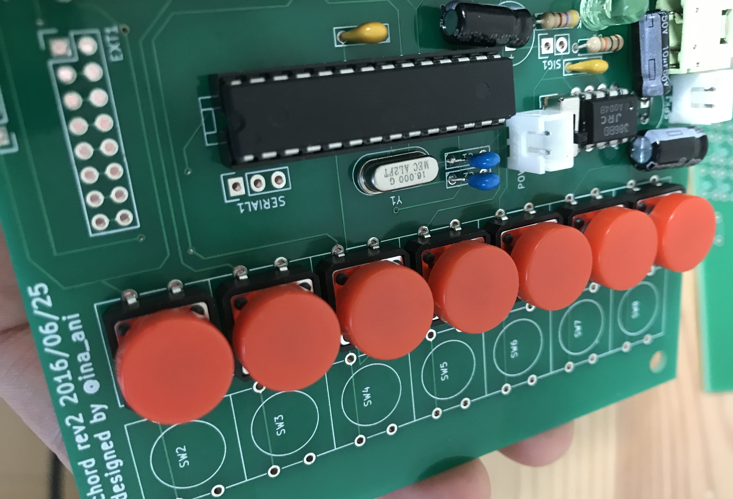
docs/imgs/instruction-out/022-switch-high.jpg
