inajob/rakuchord/docs/imgs/instruction-out/023-switch-check.jpg

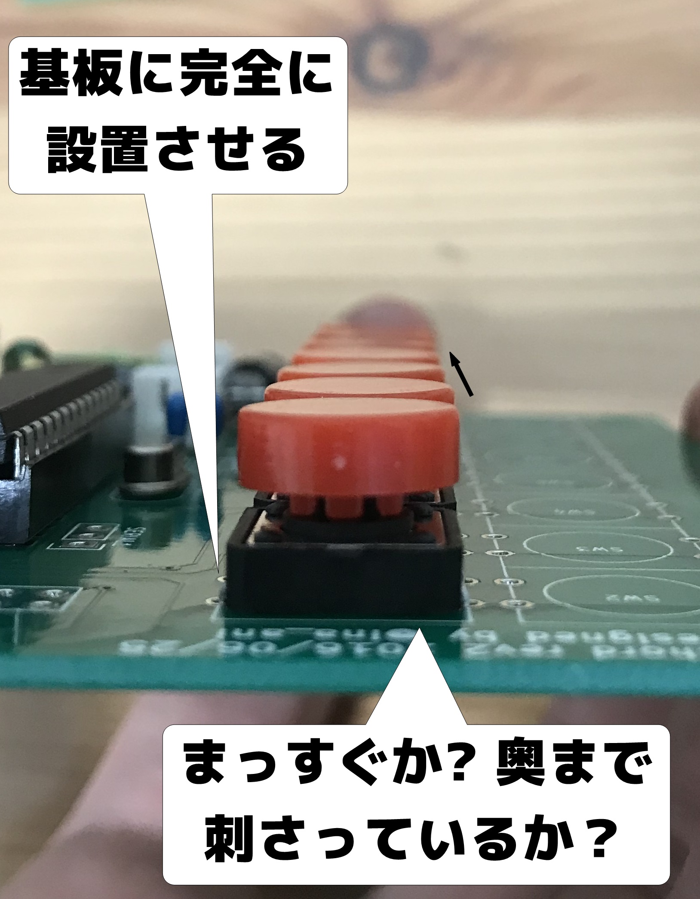
docs/imgs/instruction-out/023-switch-check.jpg
