inajob/rakuchord/docs/imgs/instruction-out/024-switch-low.jpg

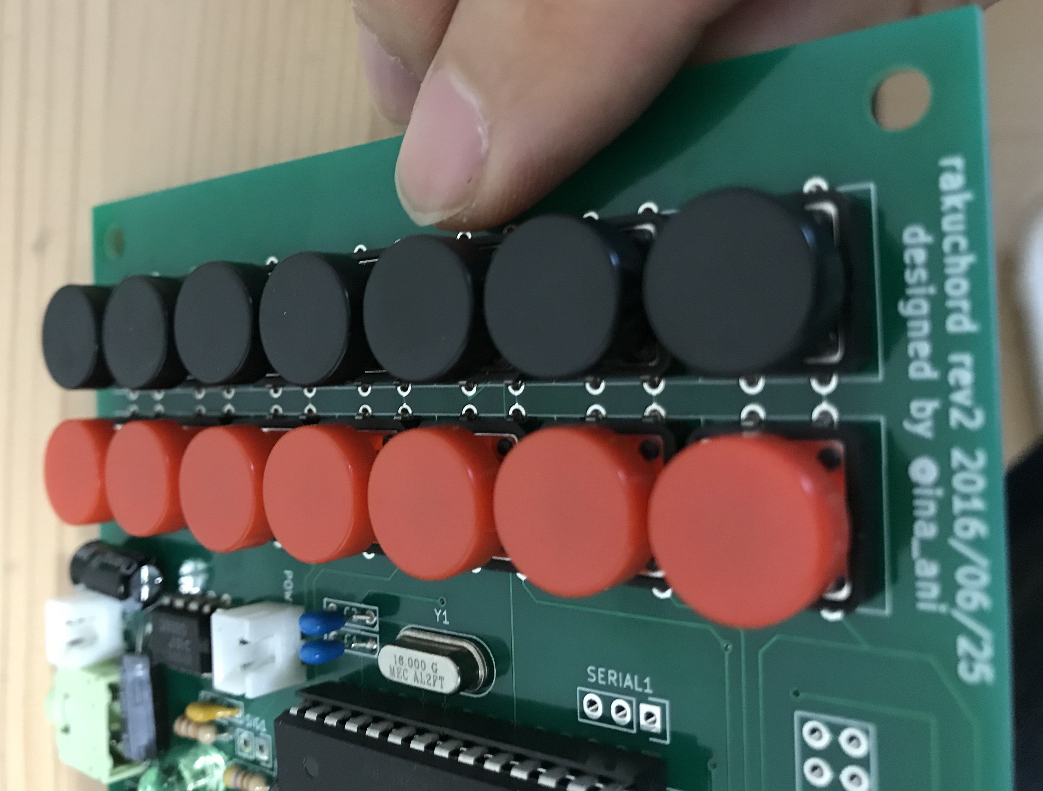
docs/imgs/instruction-out/024-switch-low.jpg
