inajob/rakuchord/docs/imgs/instruction-out/025-switch-check-second.jpg

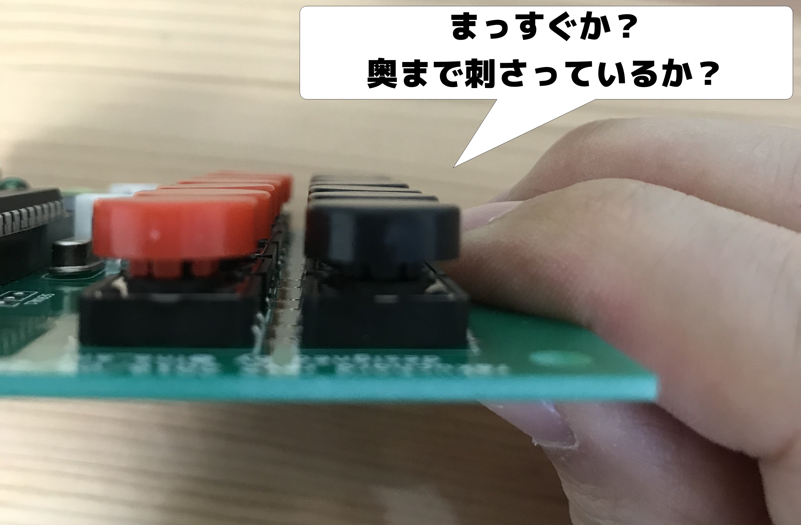
docs/imgs/instruction-out/025-switch-check-second.jpg
