inajob/rakuchord/docs/imgs/instruction-out/026-switch-back3.jpg

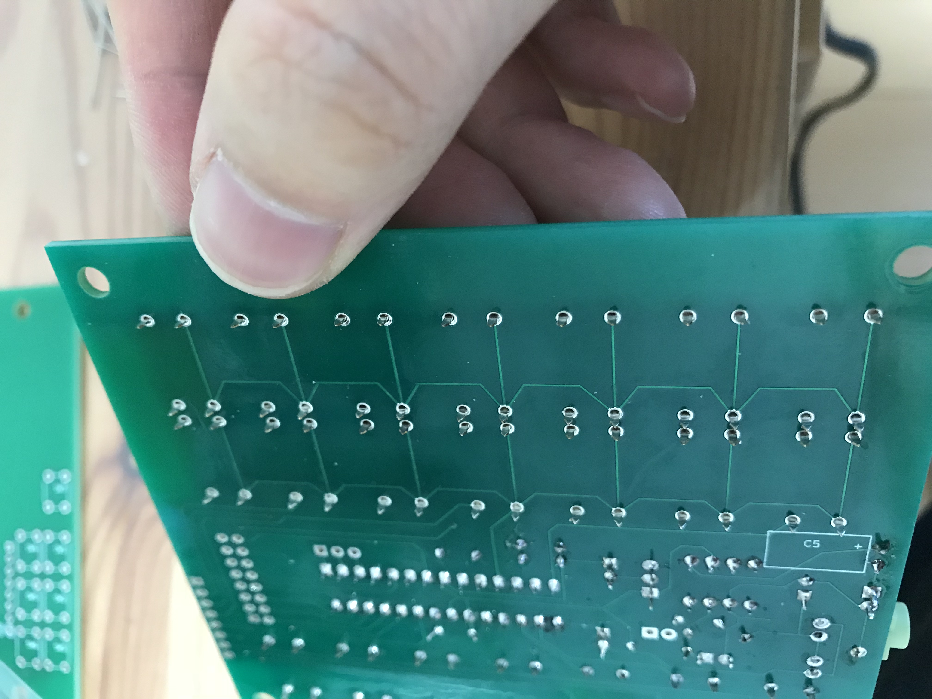
docs/imgs/instruction-out/026-switch-back3.jpg
