inajob/rakuchord/docs/imgs/instruction-out/027-subboard.jpg

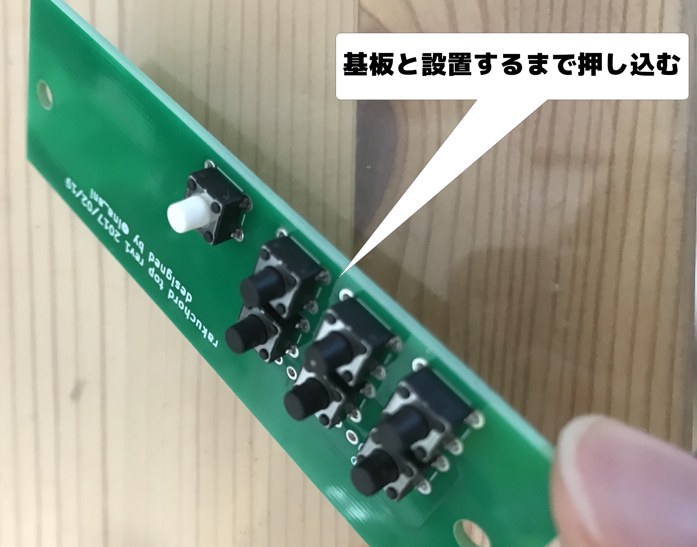
docs/imgs/instruction-out/027-subboard.jpg
