inajob/rakuchord/docs/imgs/instruction-out/028-subboard-back.jpg

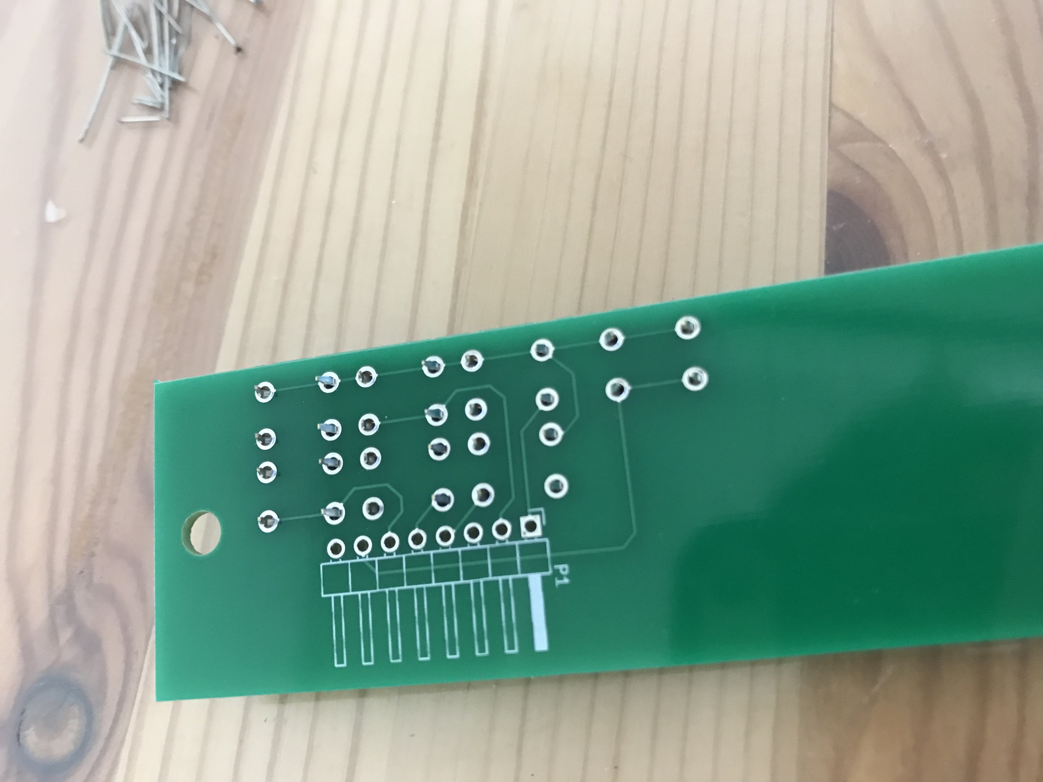
docs/imgs/instruction-out/028-subboard-back.jpg
