inajob/rakuchord/docs/imgs/instruction-out/029-subboard-back-after.jpg

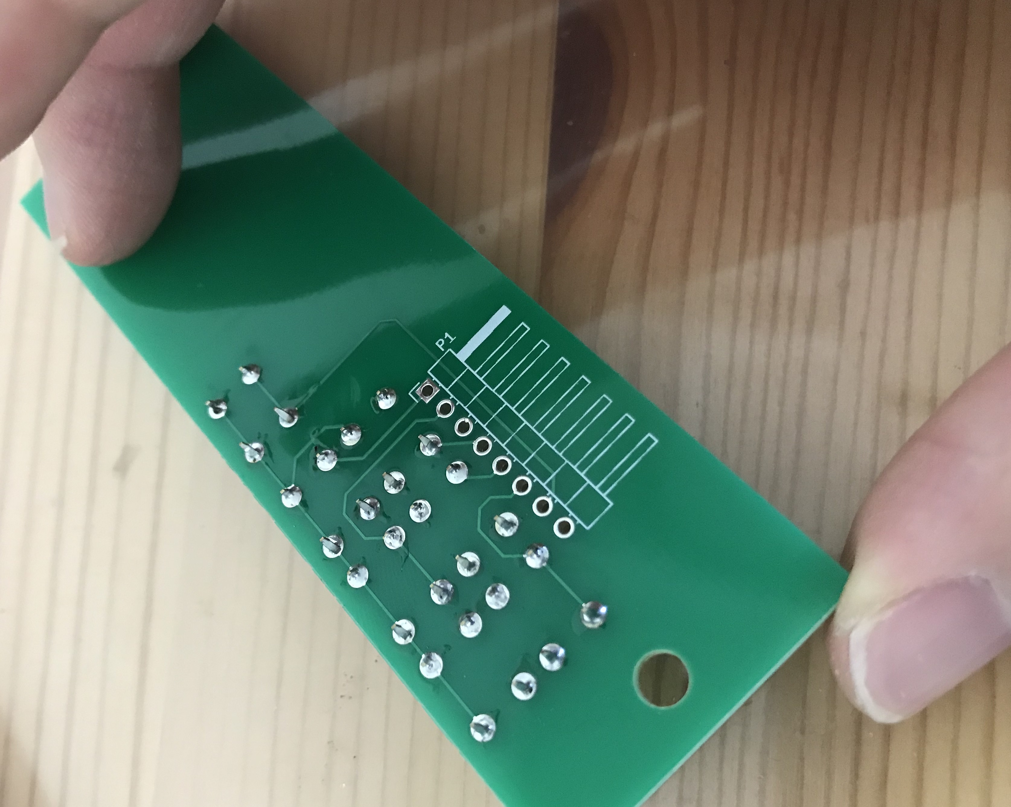
docs/imgs/instruction-out/029-subboard-back-after.jpg
