inajob/rakuchord/docs/imgs/instruction-out/030-connector.jpg

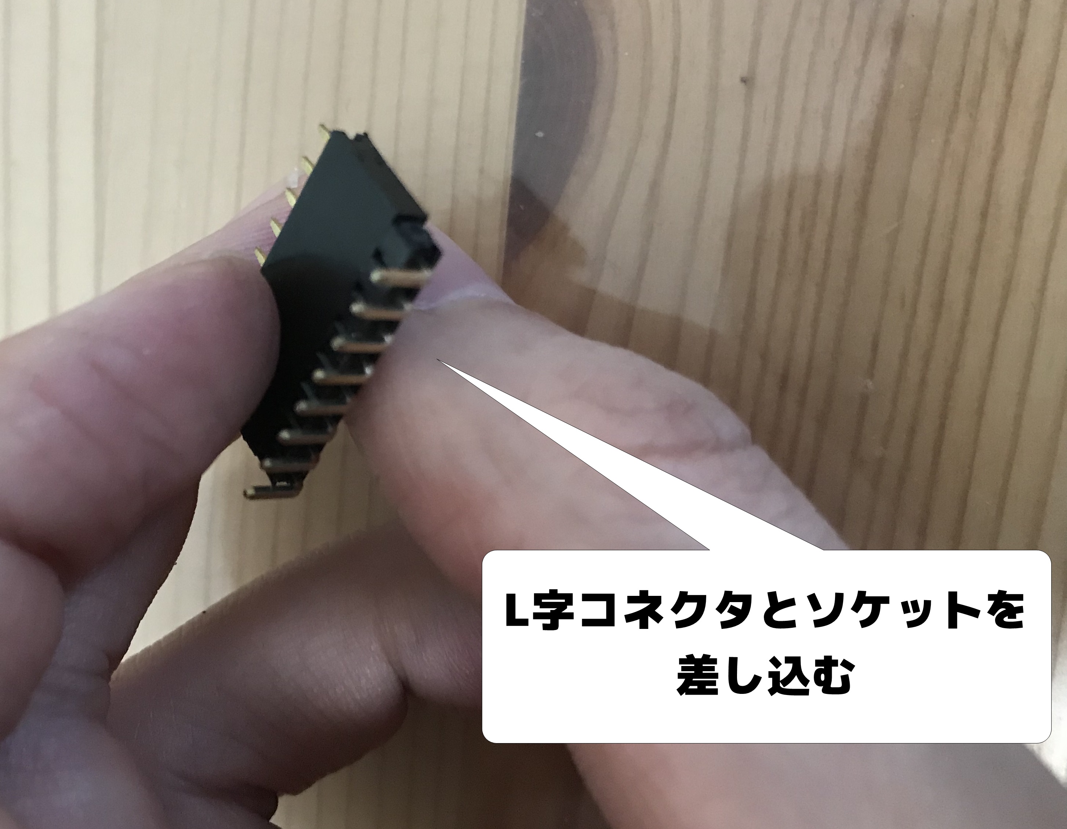
docs/imgs/instruction-out/030-connector.jpg
