inajob/rakuchord/docs/imgs/instruction-out/031-connector-settle.jpg

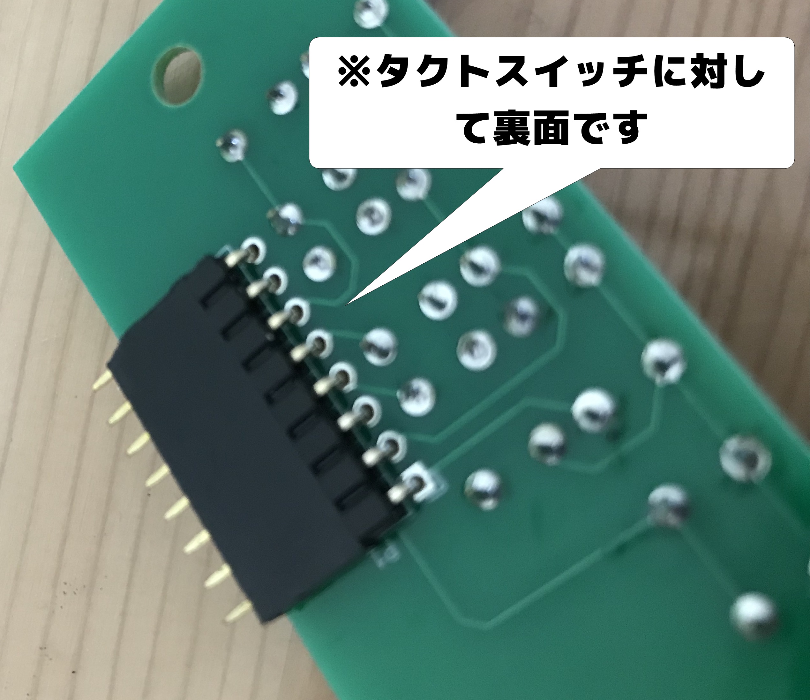
docs/imgs/instruction-out/031-connector-settle.jpg
