inajob/rakuchord/docs/imgs/instruction-out/032-subboard-complete.jpg

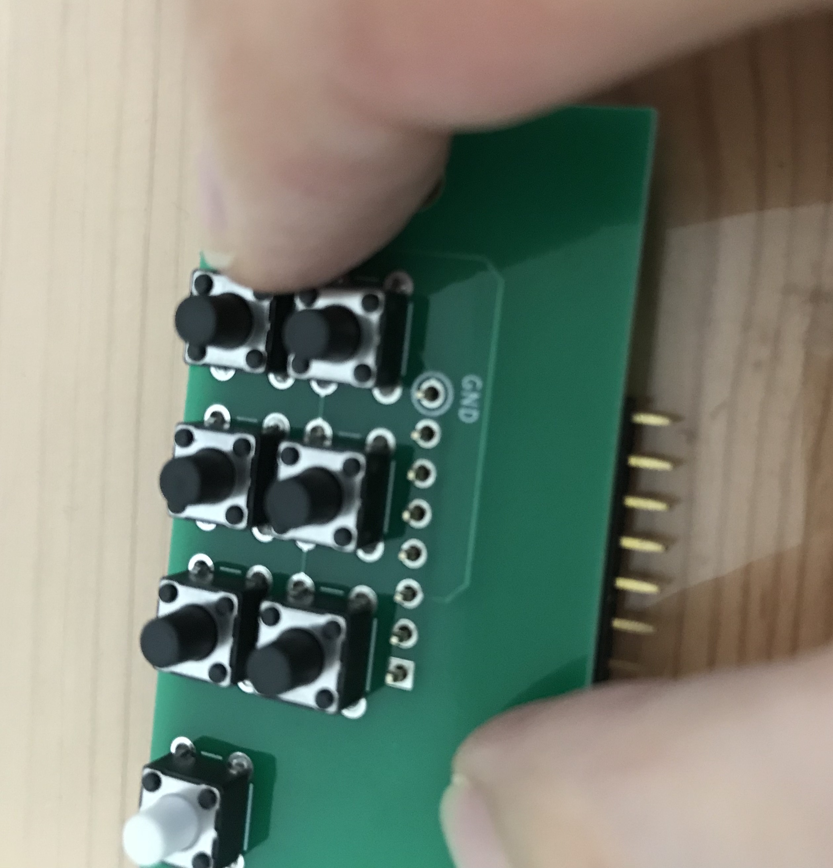
docs/imgs/instruction-out/032-subboard-complete.jpg
