inajob/rakuchord/docs/imgs/instruction-out/033-subboard-case.jpg

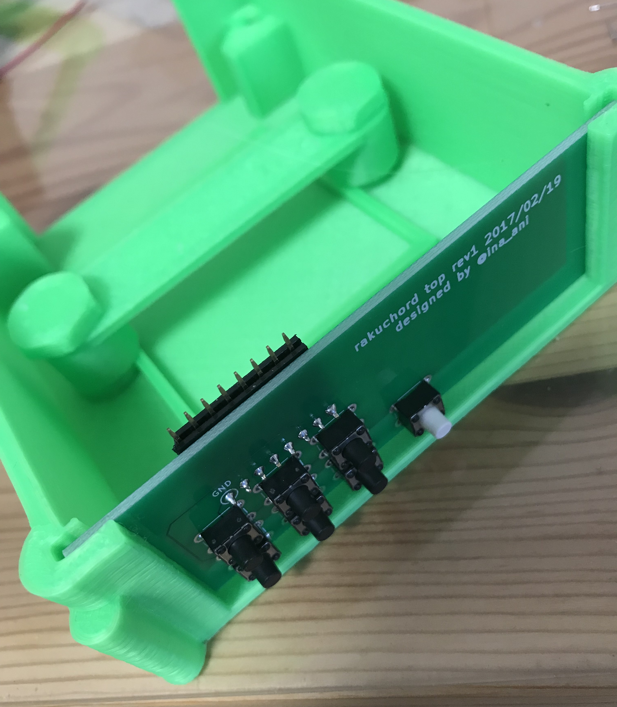
docs/imgs/instruction-out/033-subboard-case.jpg
