inajob/rakuchord/docs/imgs/instruction-out/034-mainboard-case.jpg

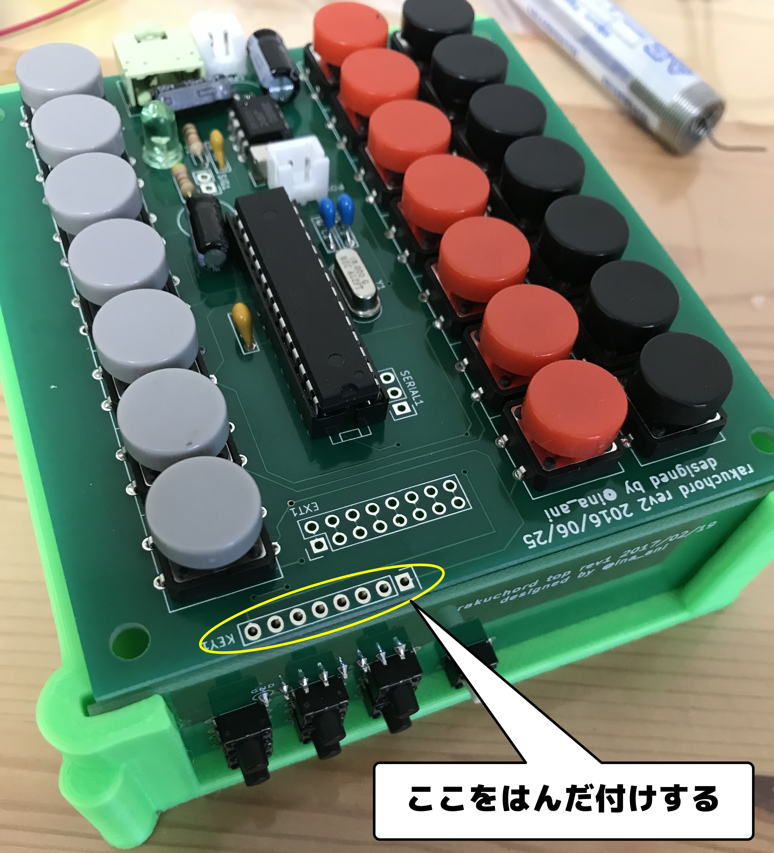
docs/imgs/instruction-out/034-mainboard-case.jpg
