inajob/rakuchord/docs/imgs/instruction-out/035-battery-case.jpg

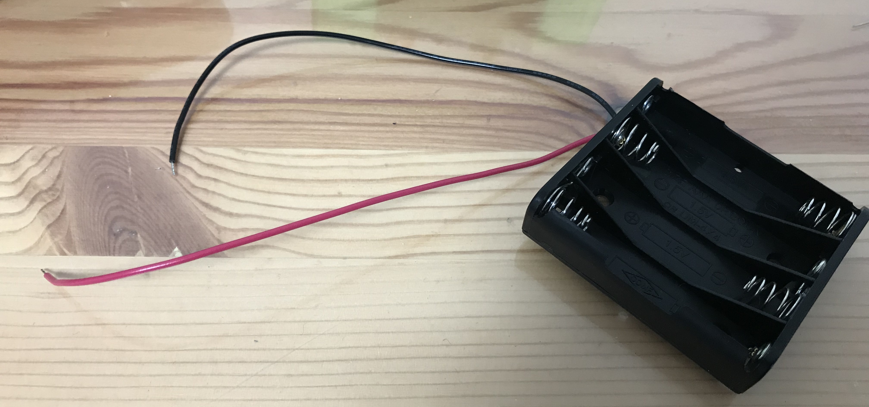
docs/imgs/instruction-out/035-battery-case.jpg
