inajob/rakuchord/docs/imgs/instruction-out/036-battery-contact.jpg

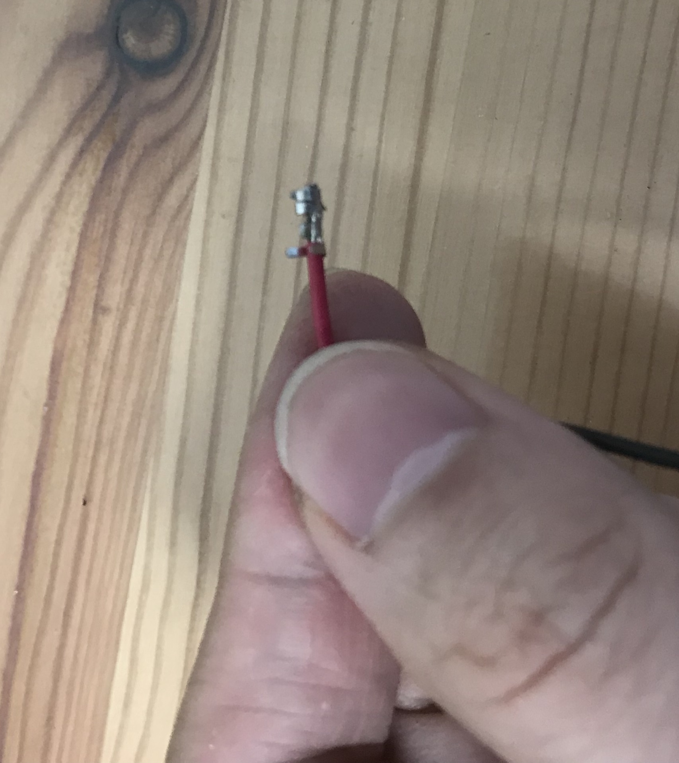
docs/imgs/instruction-out/036-battery-contact.jpg
