inajob/rakuchord/docs/imgs/instruction-out/037-contact-press.jpg

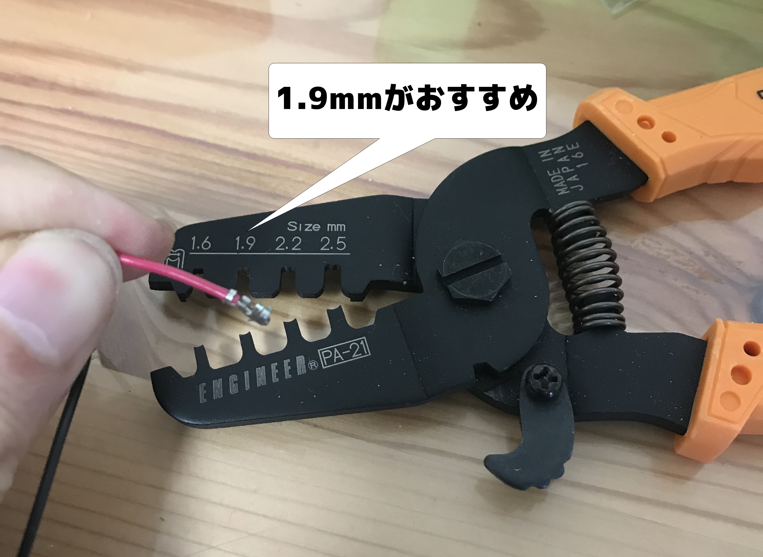
docs/imgs/instruction-out/037-contact-press.jpg
