inajob/rakuchord/docs/imgs/instruction-out/038-speaker-back.jpg

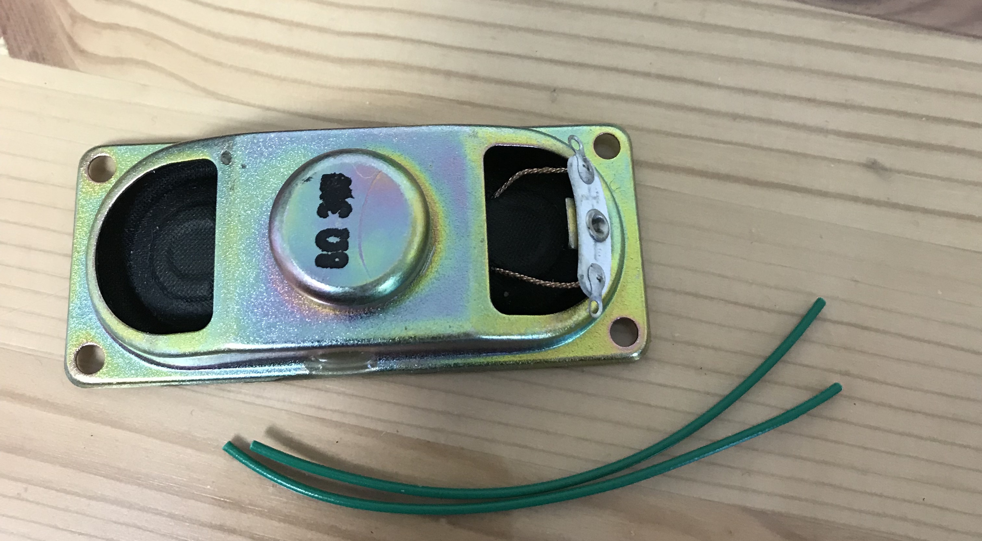
docs/imgs/instruction-out/038-speaker-back.jpg
