inajob/rakuchord/docs/imgs/instruction-out/038-speaker.jpg

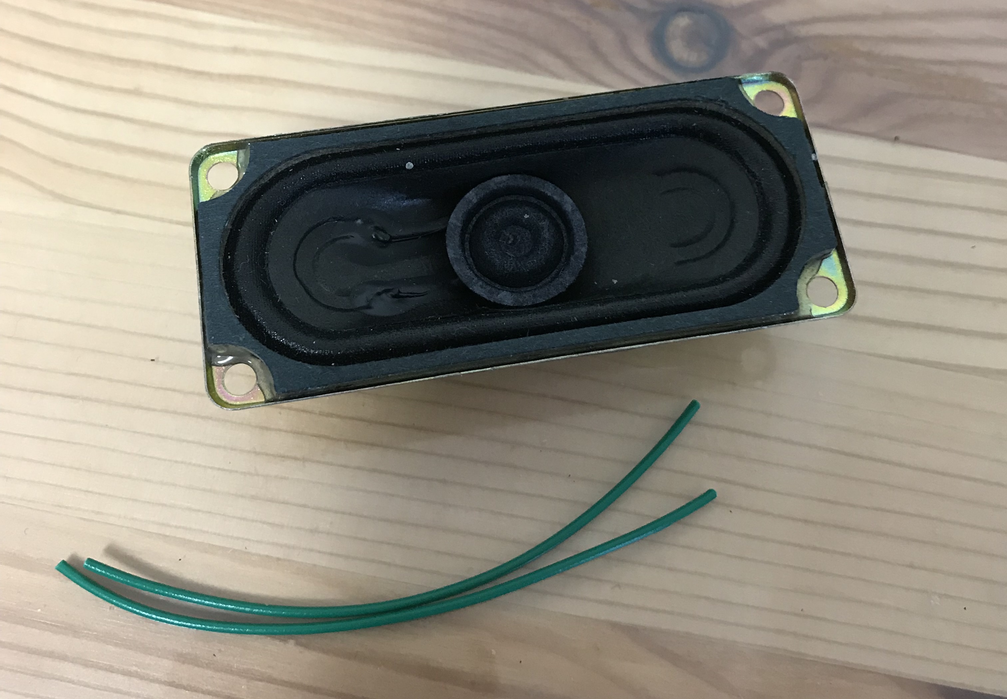
docs/imgs/instruction-out/038-speaker.jpg
