inajob/rakuchord/docs/imgs/instruction-out/039-strip-wire.jpg

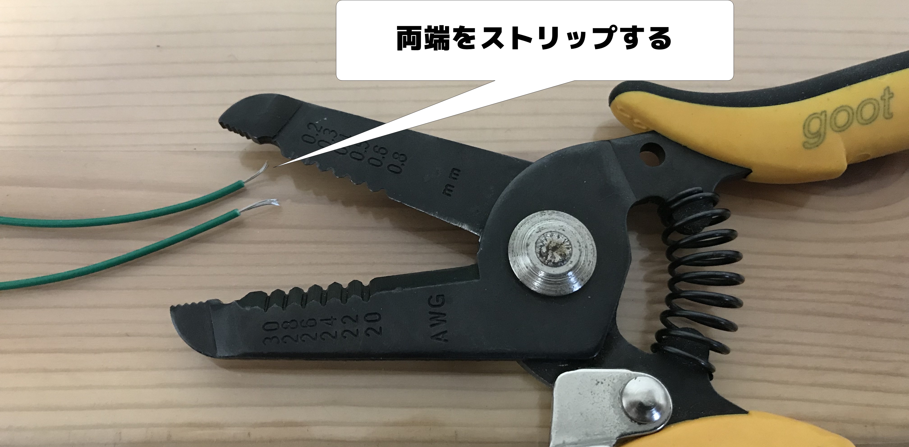
docs/imgs/instruction-out/039-strip-wire.jpg
