inajob/rakuchord/docs/imgs/instruction-out/040-speaker-wired.jpg

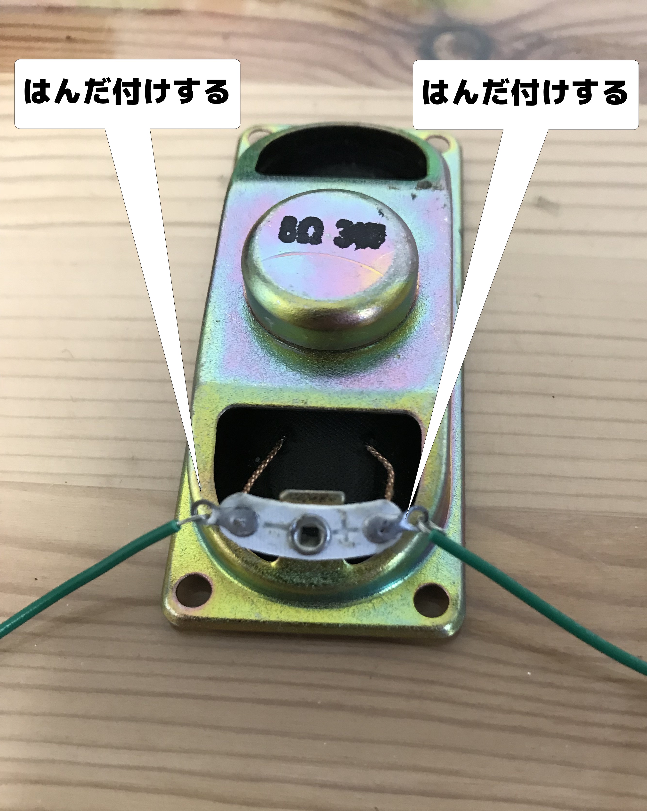
docs/imgs/instruction-out/040-speaker-wired.jpg
