inajob/rakuchord/docs/imgs/instruction-out/041-speaker-case.jpg

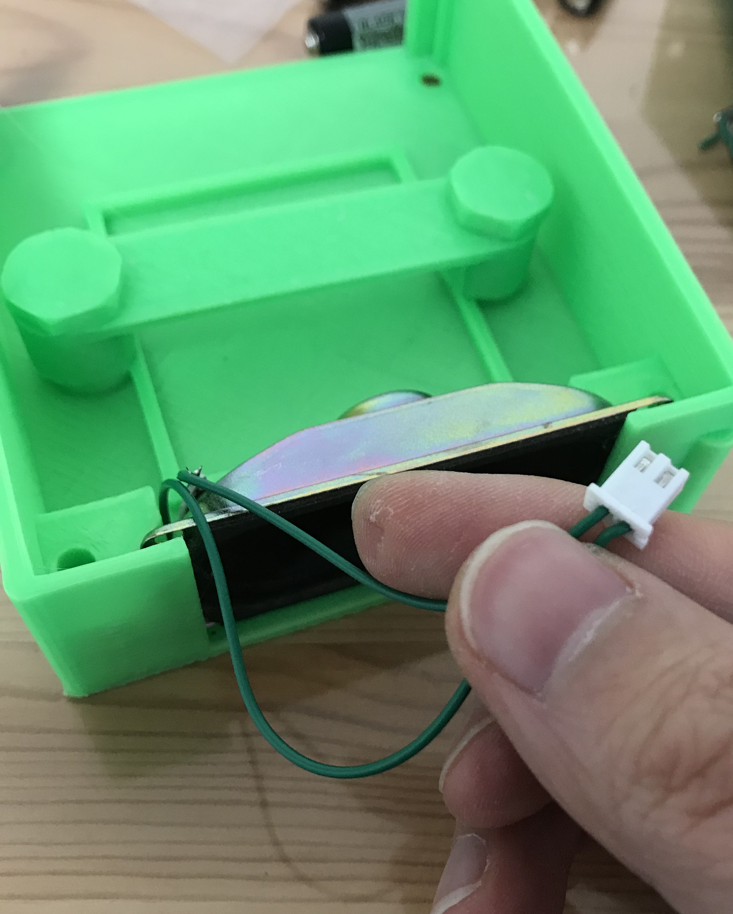
docs/imgs/instruction-out/041-speaker-case.jpg
