inajob/rakuchord/docs/imgs/instruction-out/042-battery-housing.jpg

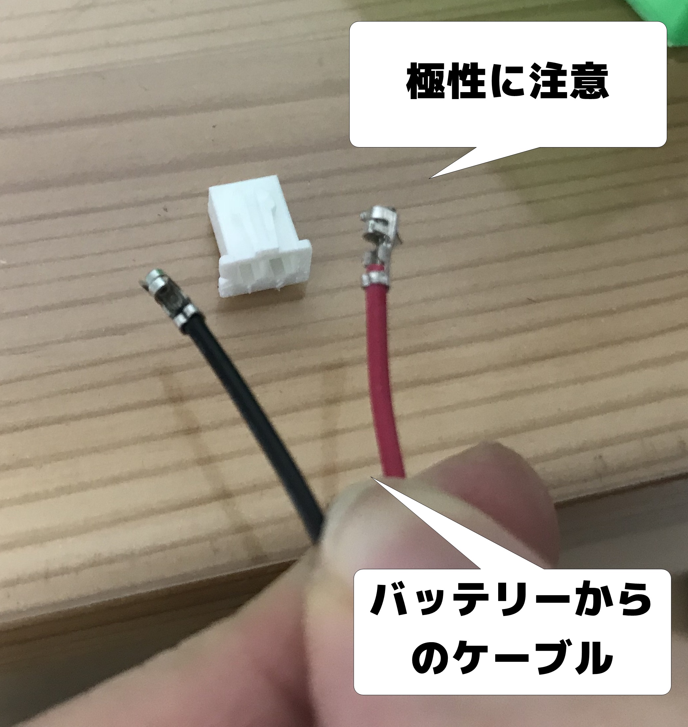
docs/imgs/instruction-out/042-battery-housing.jpg
