inajob/rakuchord/docs/imgs/instruction-out/043-battery-housing2.jpg

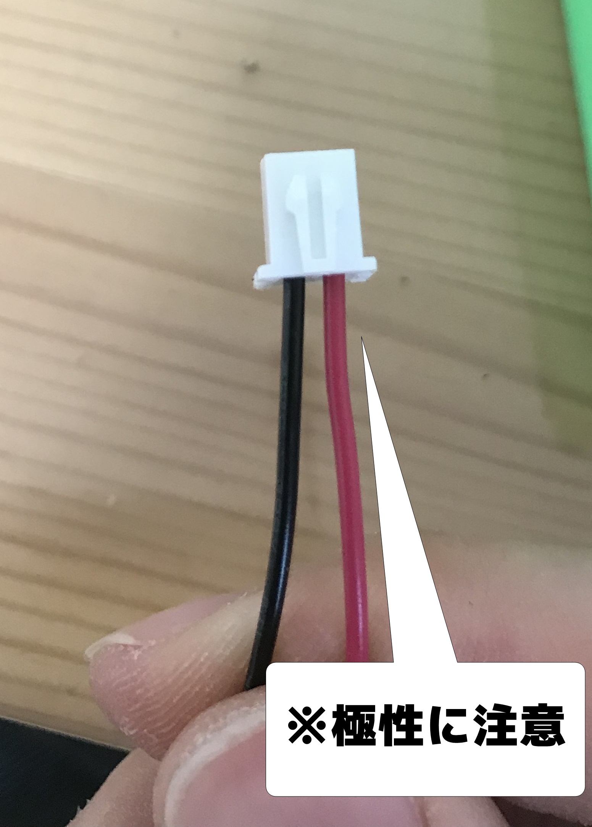
docs/imgs/instruction-out/043-battery-housing2.jpg
