inajob/rakuchord/docs/imgs/instruction-out/045-main-sub-board.jpg

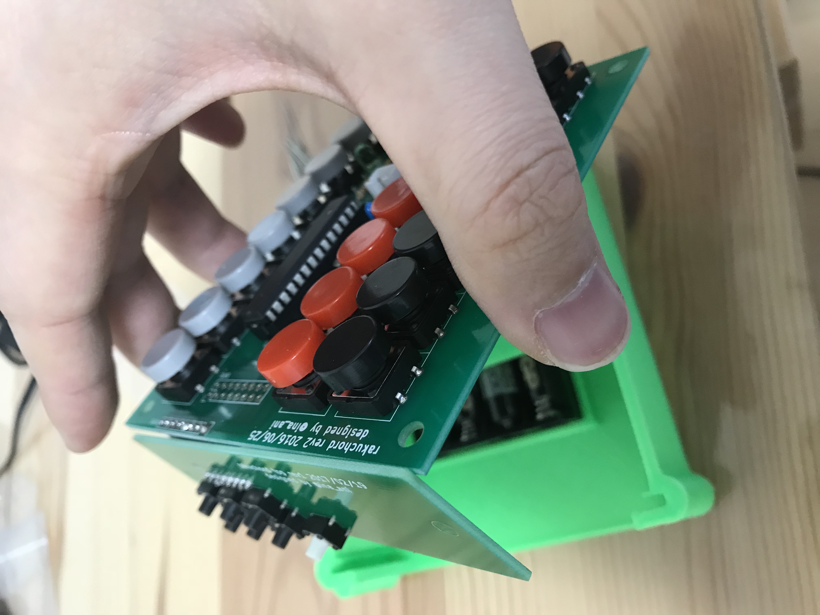
docs/imgs/instruction-out/045-main-sub-board.jpg
