inajob/rakuchord/docs/imgs/instruction-out/046-main-sub-case.jpg

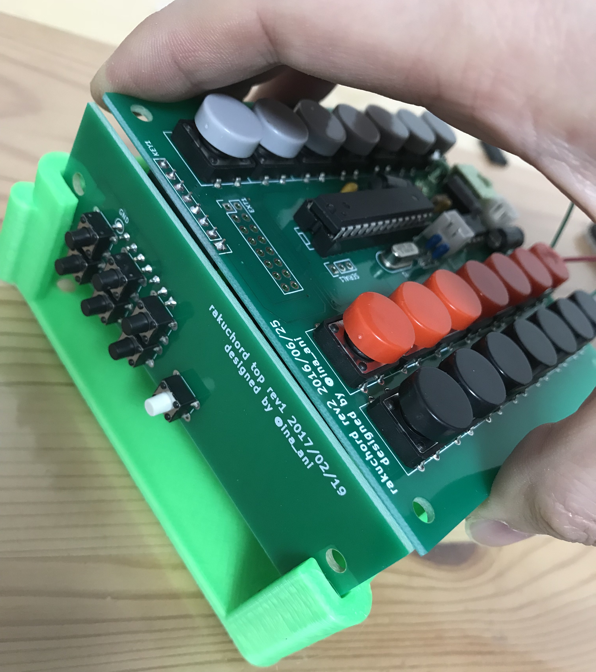
docs/imgs/instruction-out/046-main-sub-case.jpg
