inajob/rakuchord/docs/imgs/instruction-out/047-wired.jpg

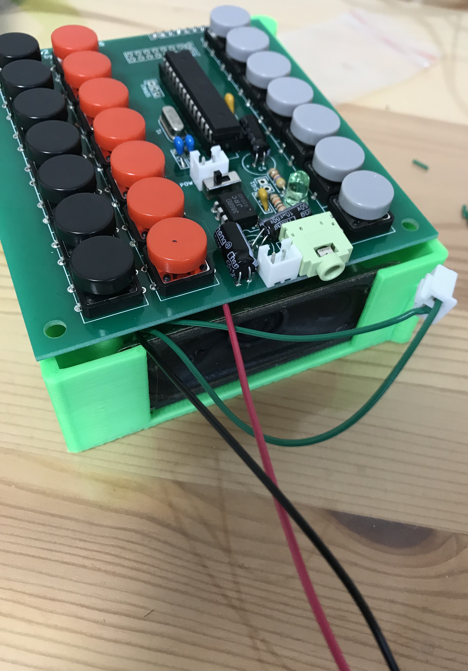
docs/imgs/instruction-out/047-wired.jpg
