inajob/rakuchord/docs/imgs/instruction-out/048-wired-complete.jpg

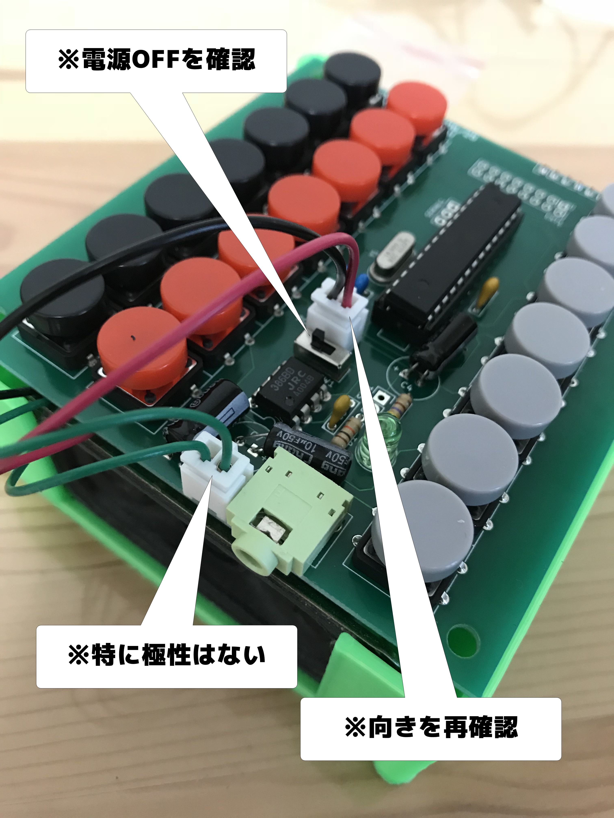
docs/imgs/instruction-out/048-wired-complete.jpg
