inajob/rakuchord/docs/imgs/instruction-out/050-top-case.jpg

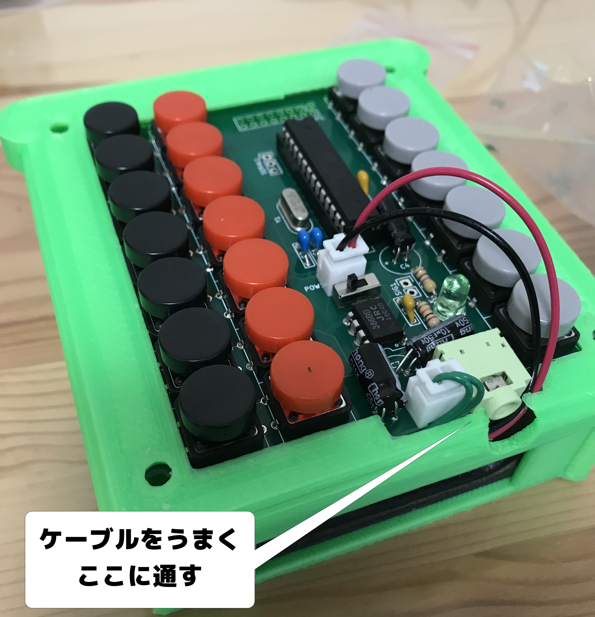
docs/imgs/instruction-out/050-top-case.jpg
