inajob/rakuchord/docs/imgs/instruction-out/051-bolts-nuts.jpg

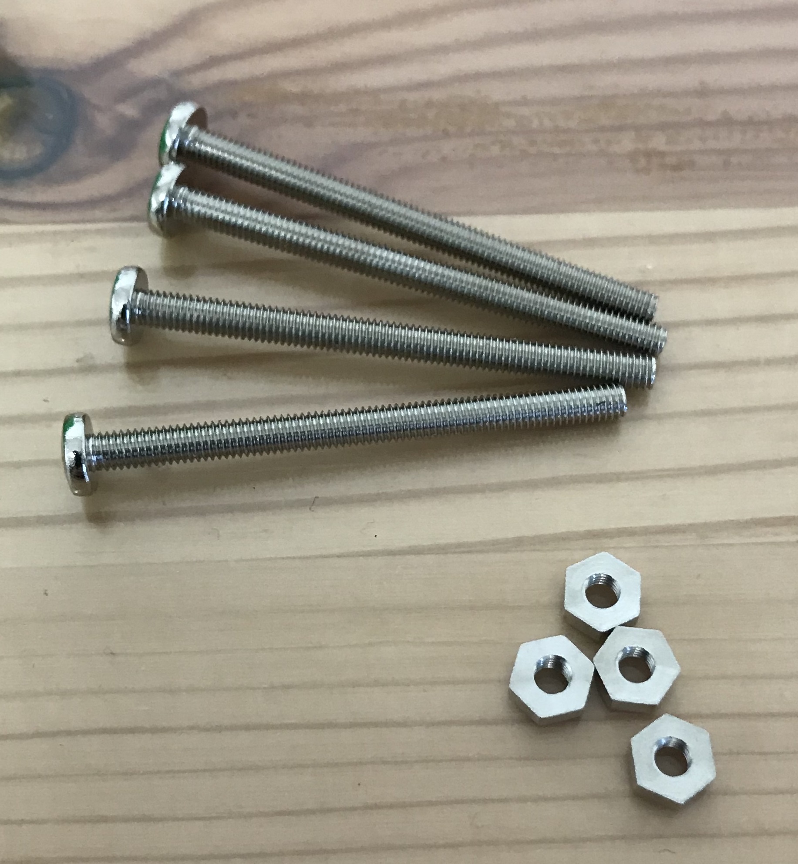
docs/imgs/instruction-out/051-bolts-nuts.jpg
