inajob/rakuchord/docs/imgs/instruction-out/052-bolts.jpg

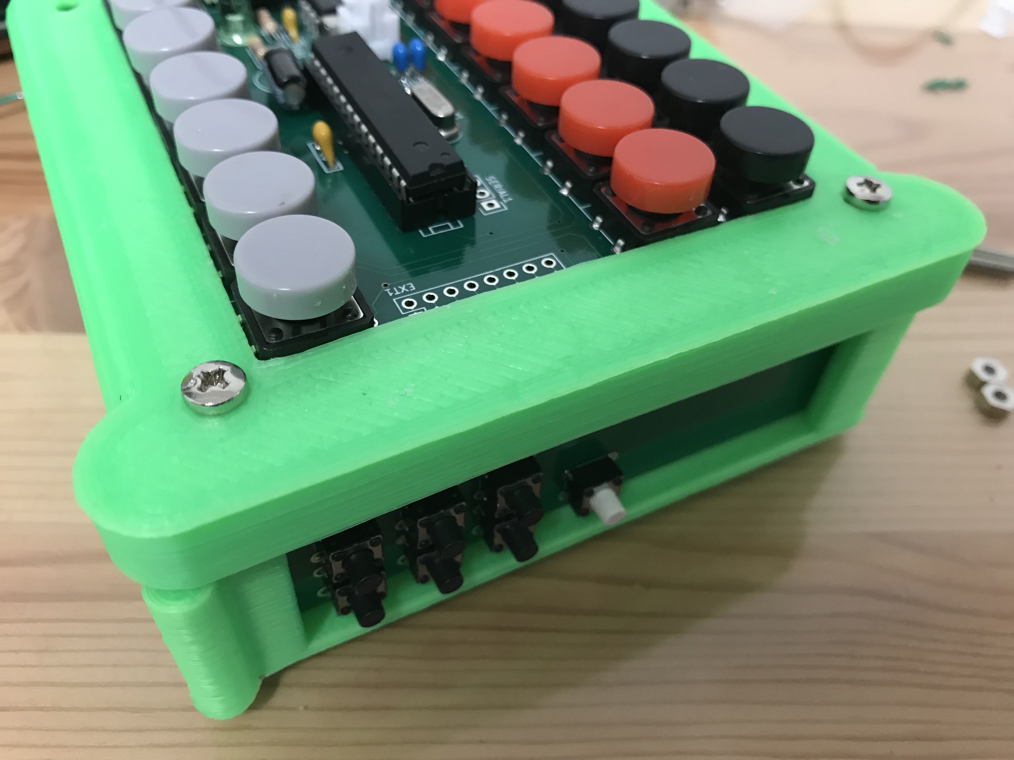
docs/imgs/instruction-out/052-bolts.jpg
