inajob/rakuchord/docs/imgs/instruction-out/053-bolts-dub.jpg

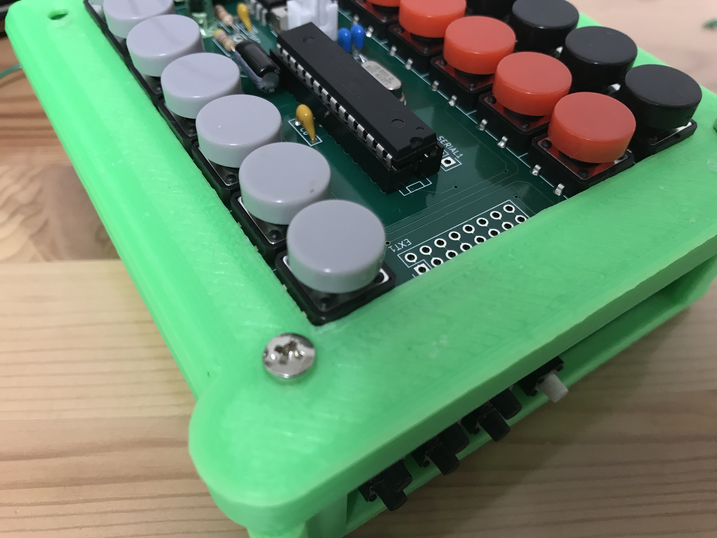
docs/imgs/instruction-out/053-bolts-dub.jpg
