inajob/rakuchord/docs/imgs/instruction-out/054-bolts-back.jpg

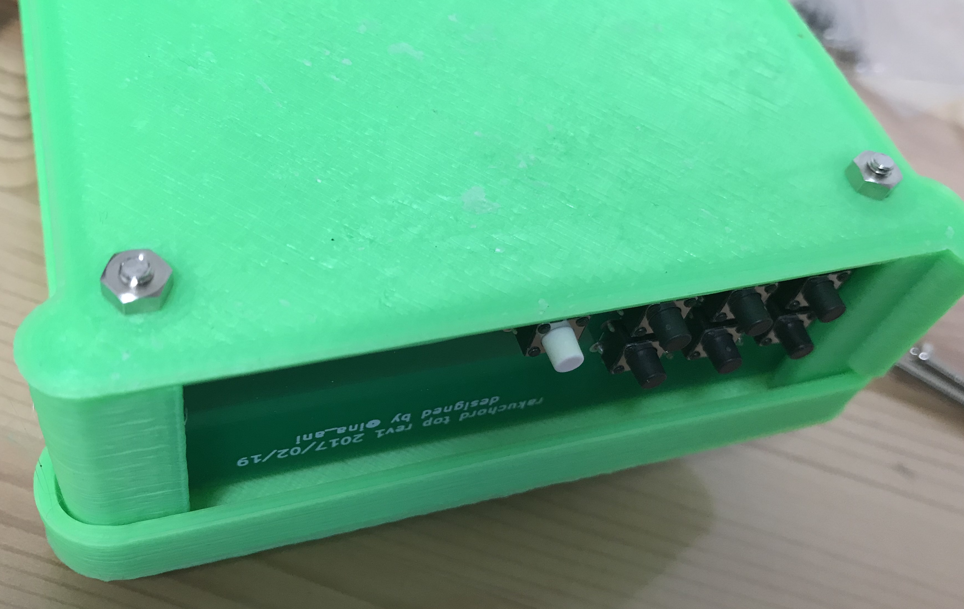
docs/imgs/instruction-out/054-bolts-back.jpg
