inajob/rakuchord/docs/imgs/instruction-out/055-bolts-second.jpg

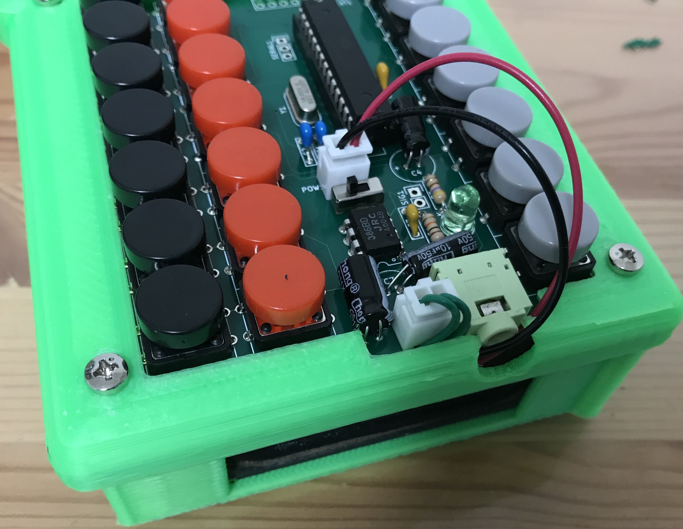
docs/imgs/instruction-out/055-bolts-second.jpg
