inajob/rakuchord/docs/imgs/instruction-out/056-bolts-second-back.jpg

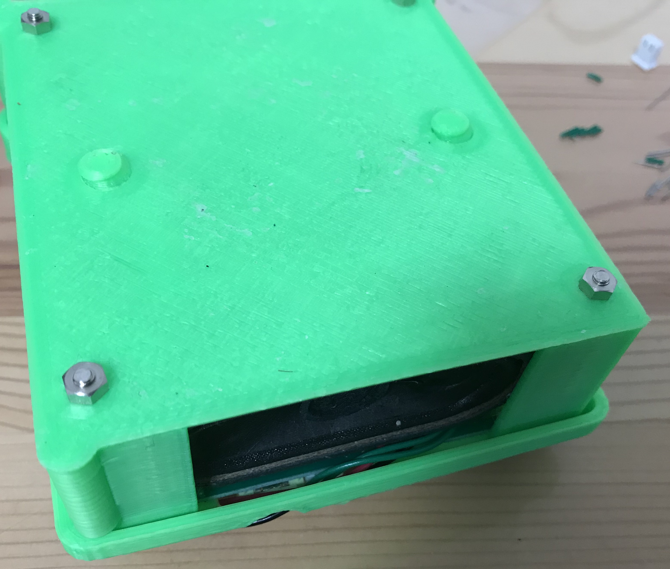
docs/imgs/instruction-out/056-bolts-second-back.jpg
