inajob/rakuchord/docs/imgs/instruction-out/057-complete.jpg

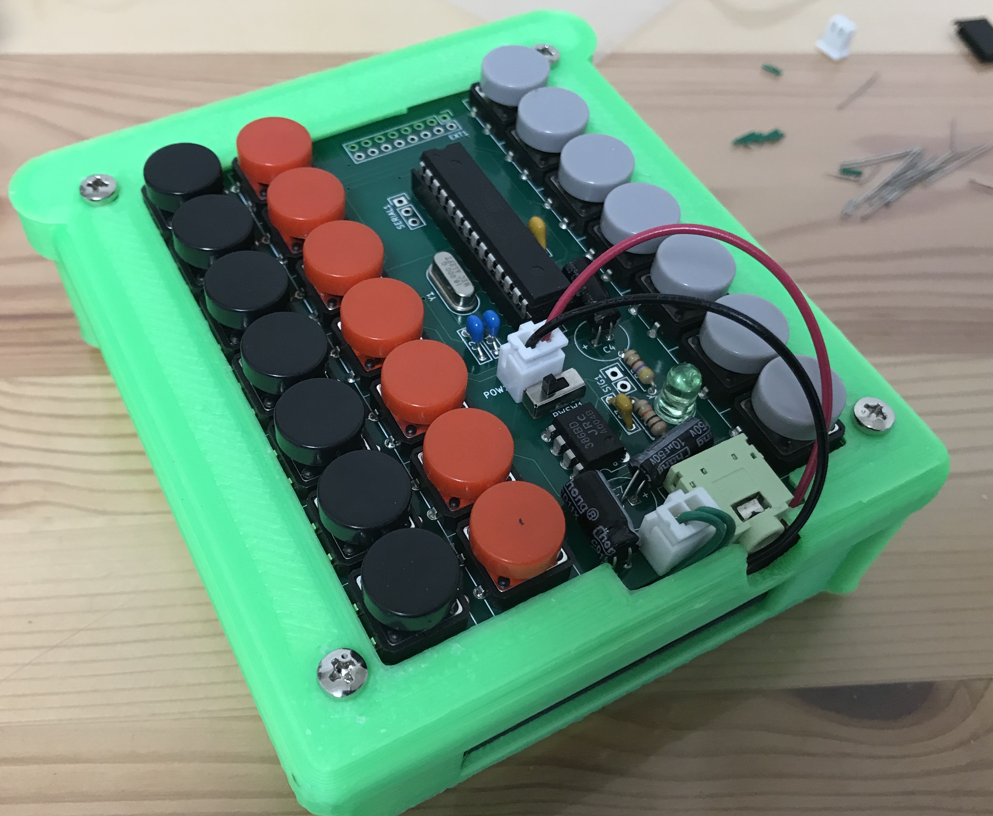
docs/imgs/instruction-out/057-complete.jpg
