inajob/rakuchord/docs/imgs/instruction-out/tools.jpg

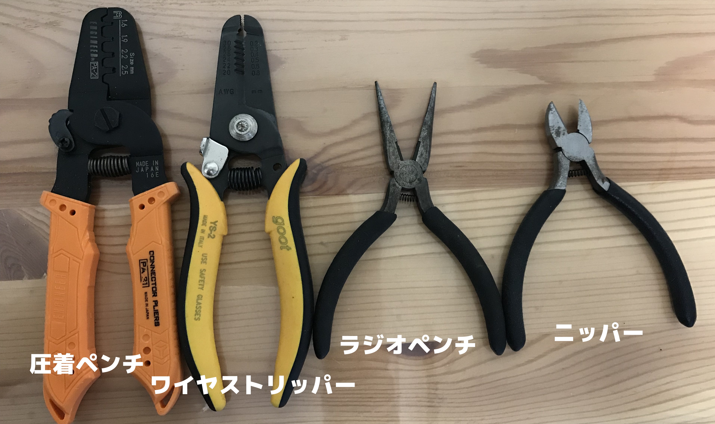
docs/imgs/instruction-out/tools.jpg
