inajob/rakuchord/docs/imgs/instruction-out/015-first-test.jpg

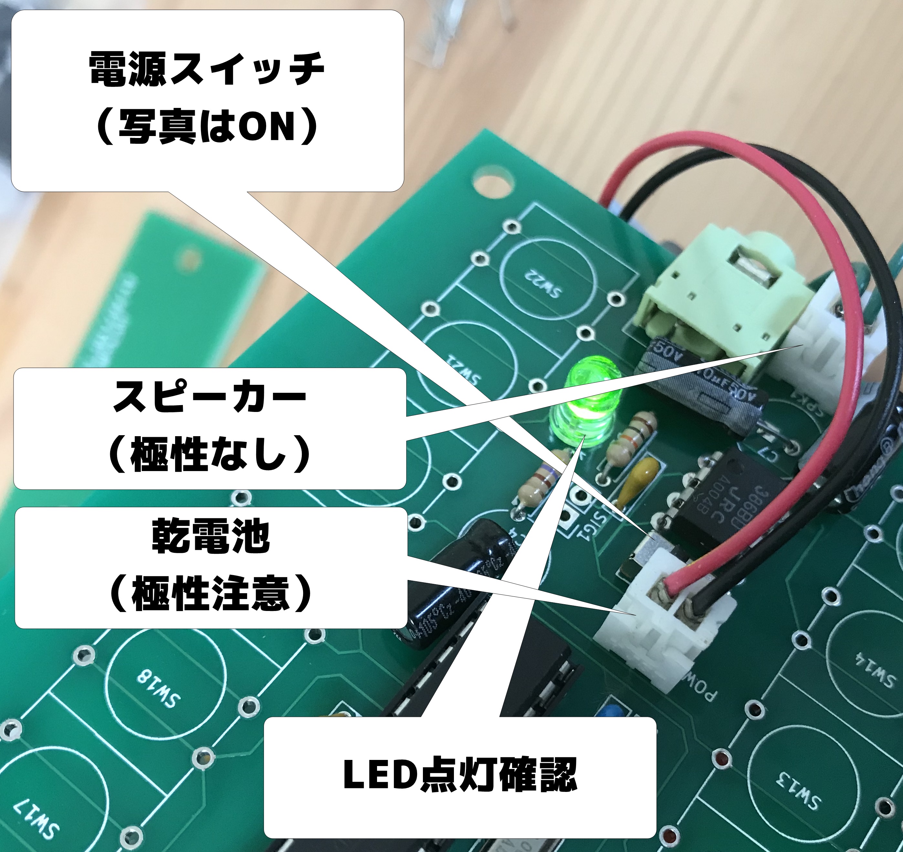
docs/imgs/instruction-out/015-first-test.jpg
