inajob/rakuchord/docs/imgs/instruction-out/049-second-test.jpg

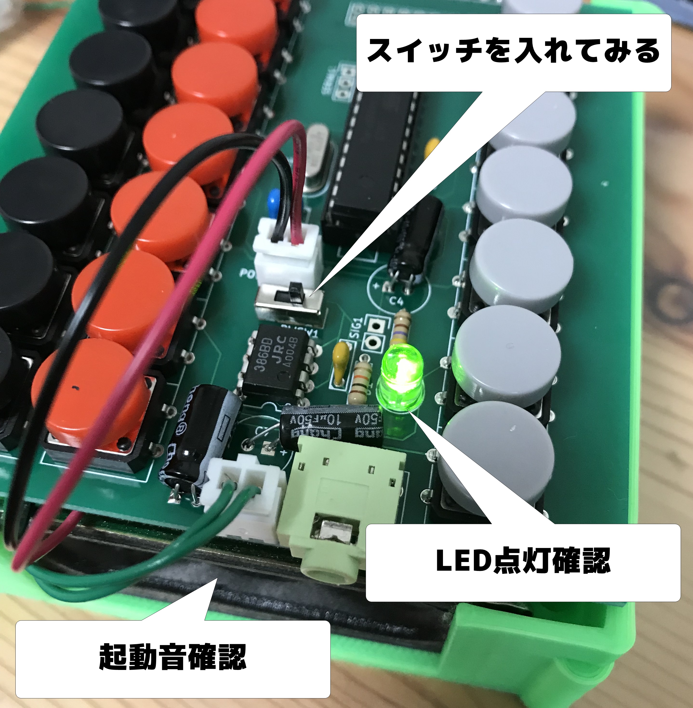
docs/imgs/instruction-out/049-second-test.jpg
