inajob/rakuchord/docs/imgs/changelog/2019-03-change.png

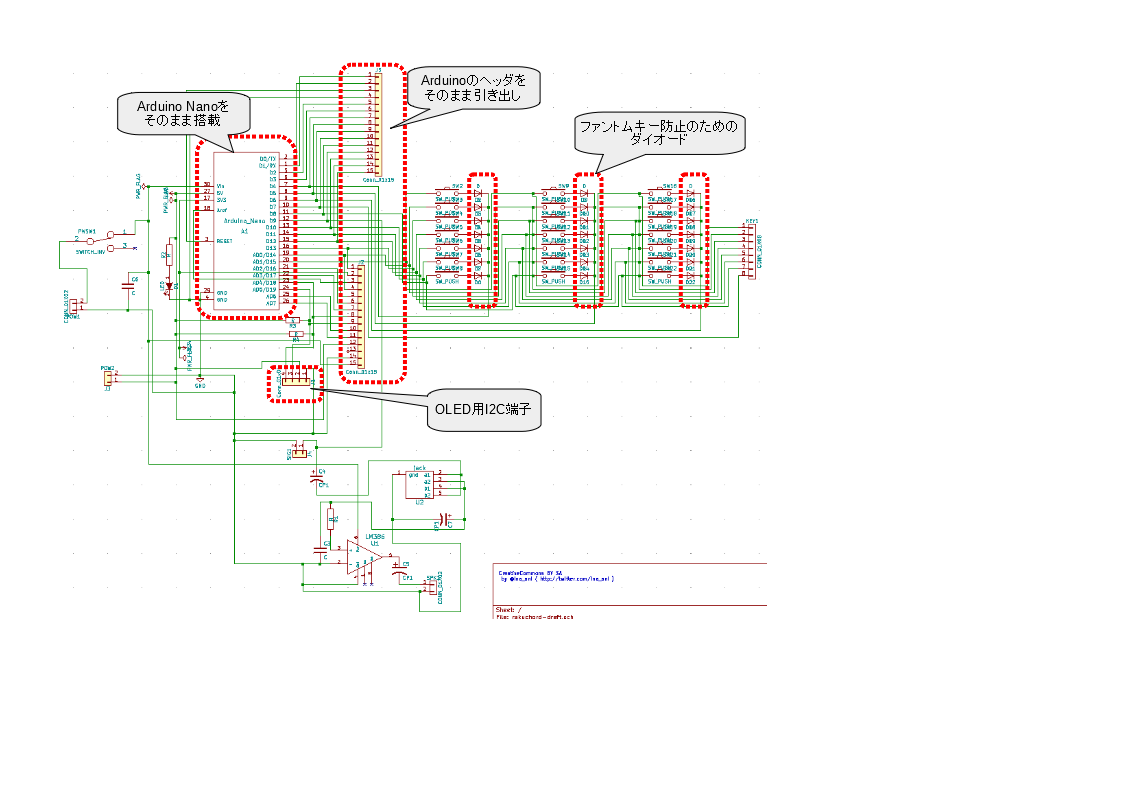
docs/imgs/changelog/2019-03-change.png
