inajob/rakuchord/docs/imgs/instruction-out/016-pin-fix.jpg

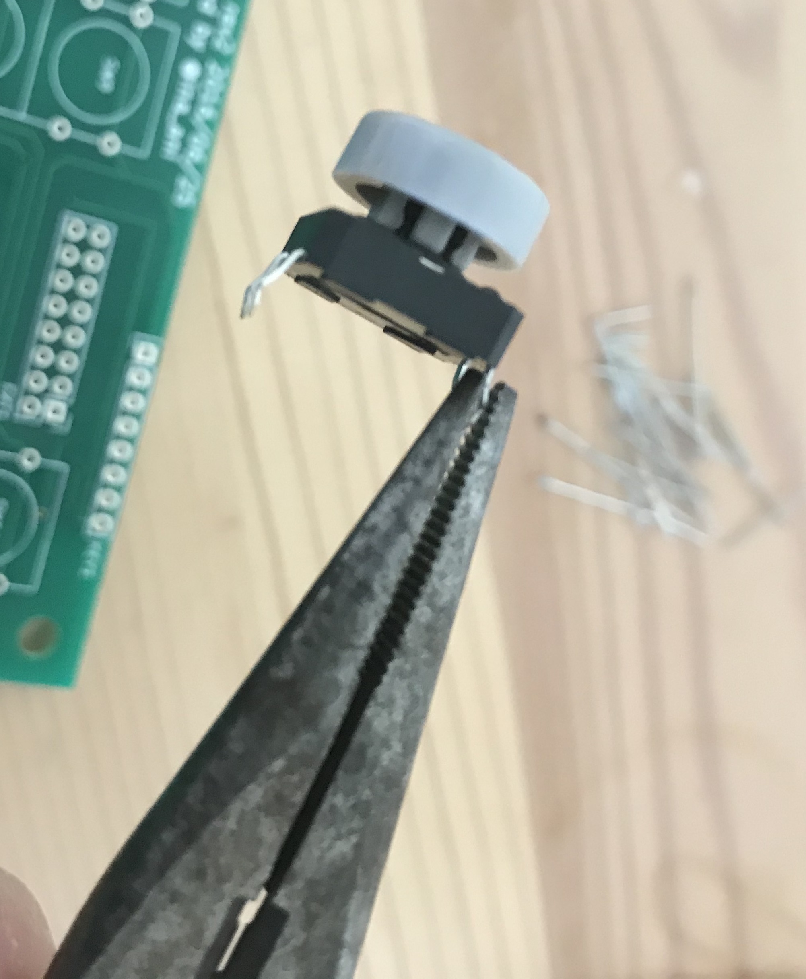
docs/imgs/instruction-out/016-pin-fix.jpg
