inajob/rakuchord/docs/imgs/instruction-out/017-pin-fix-after.jpg

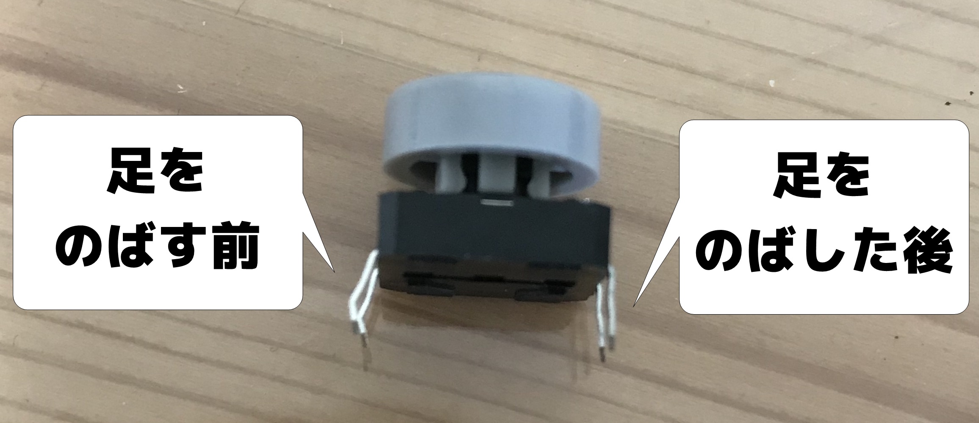
docs/imgs/instruction-out/017-pin-fix-after.jpg
