inajob/rakuchord/firmware/src/MultiTunes.h

#ifndef MultiTunes_h
#define MultiTunes_h

extern volatile unsigned int d[5]; // default value( for debug)
extern volatile unsigned char vol[5]; // volume par channel
extern volatile byte nf;
extern volatile byte nf2;
extern int noise;
extern int noise2;

extern volatile byte vf;

extern byte wave[8][64];


void soundSetup();

#endif
