inajob/rakuchord/firmware/src/tones.h

#define NOTE_C3  131
#define NOTE_CS3 139
#define NOTE_D3  147
#define NOTE_DS3 156
#define NOTE_E3  165
#define NOTE_F3  175
#define NOTE_FS3 185
#define NOTE_G3  196
#define NOTE_GS3 208
#define NOTE_A3  220
#define NOTE_AS3 233
#define NOTE_B3  247
#define NOTE_C4  262
#define NOTE_CS4 277
#define NOTE_D4  294
#define NOTE_DS4 311
#define NOTE_E4  330
#define NOTE_F4  349
#define NOTE_FS4 370
#define NOTE_G4  392
#define NOTE_GS4 415
#define NOTE_A4  440
#define NOTE_AS4 466
#define NOTE_B4  494
#define NOTE_C5  523
#define NOTE_CS5 554
#define NOTE_D5  587
#define NOTE_DS5 622
#define NOTE_E5  659
#define NOTE_F5  698
#define NOTE_FS5 740
#define NOTE_G5  784
#define NOTE_GS5 831
#define NOTE_A5  880
#define NOTE_AS5 932
#define NOTE_B5  988

static const unsigned int tones[] = {
NOTE_C3,NOTE_CS3,
NOTE_D3,NOTE_DS3,
NOTE_E3,
NOTE_F3,NOTE_FS3,
NOTE_G3,NOTE_GS3,
NOTE_A3,NOTE_AS3,
NOTE_B3,
NOTE_C4,NOTE_CS4,
NOTE_D4,NOTE_DS4,
NOTE_E4,
NOTE_F4,NOTE_FS4,
NOTE_G4,NOTE_GS4,
NOTE_A4,NOTE_AS4,
NOTE_B4,
NOTE_C5,NOTE_CS5,
NOTE_D5,NOTE_DS5,
NOTE_E5,
NOTE_F5,NOTE_FS5,
NOTE_G5,NOTE_GS5,
NOTE_A5,NOTE_AS5,
NOTE_B5
};

static const char magic[] = {
0 , 2, 4, 5, 7, 9,11,
12,14,16,17,19,21,23,
24,26,28,29,31,33,35
};
